Kempf/GuidestarLaser/ProjectRequirements/Project_Reviews/Project_Reeview_1/Pitch1.pptx

## Guide Star Laser Interface (Semiconductor Laser on Wattle)

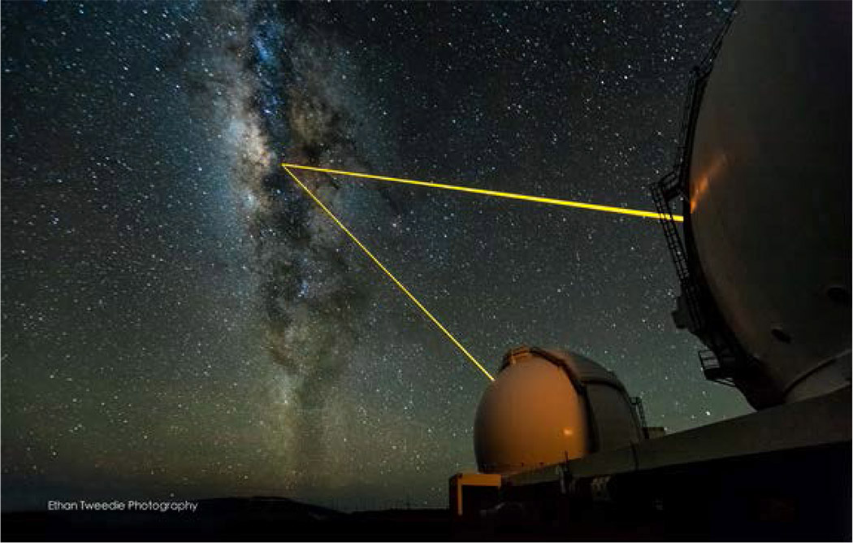
[picture p3: figure]

A. Stuchbery, G. Kennedy, J. Davies, M. Dirnberger, S. Nilon
Client: Céline D’Orgeville
Advanced Instrumentation and Technology Centre (AITC)
Space Environment Research Centre (SERC)

## Slide 2

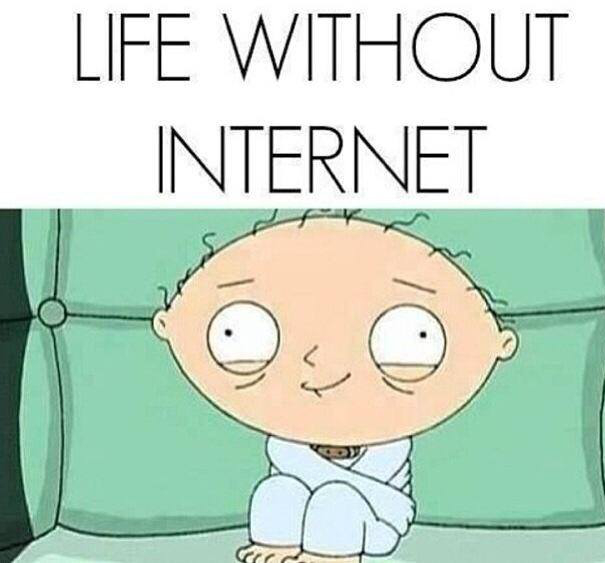
[picture p4: figure]

## Adaptive Optics (AO) – What is it?

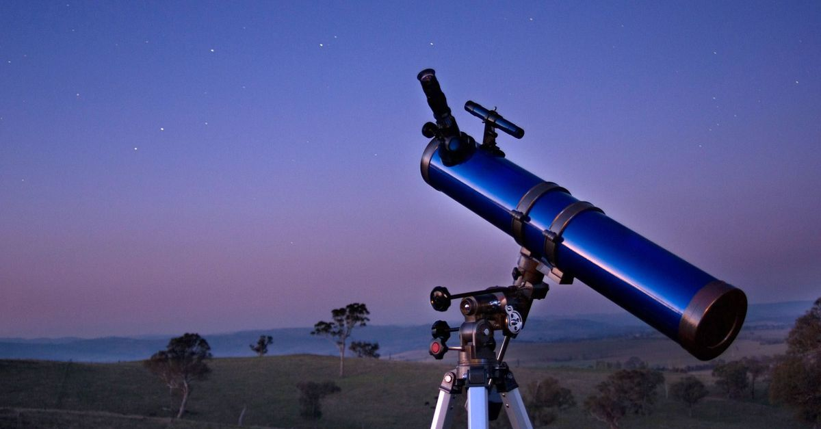
[picture p5: figure]

Animation curtesy of Anna Zovaro, PhD student

## Adaptive Optics (AO) – What is it good for?

Uranus
Credit Keck Observatory

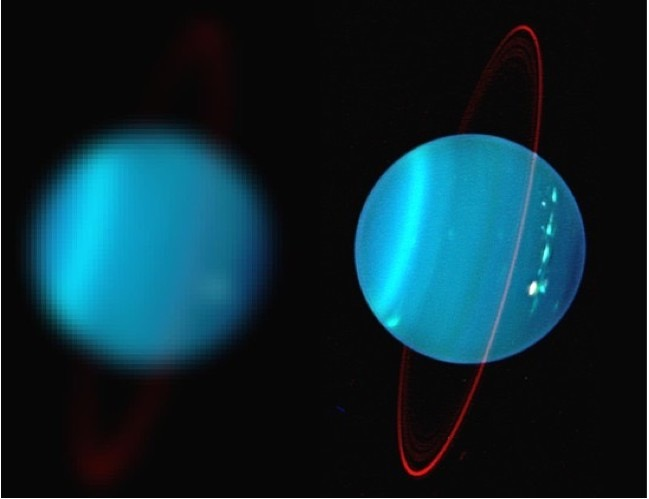
[picture p6: figure]

More than absolutely nothing!

Without AO

With AO

## Toptica Laser

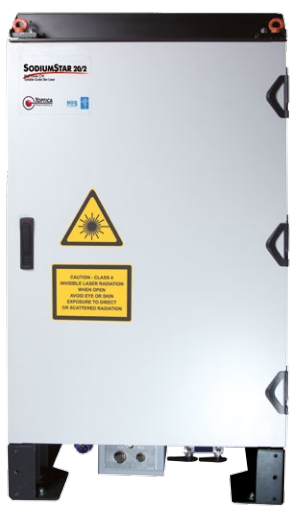
[picture p7: figure]
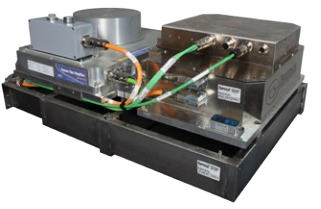
[picture p8: figure]

## Interface Tree

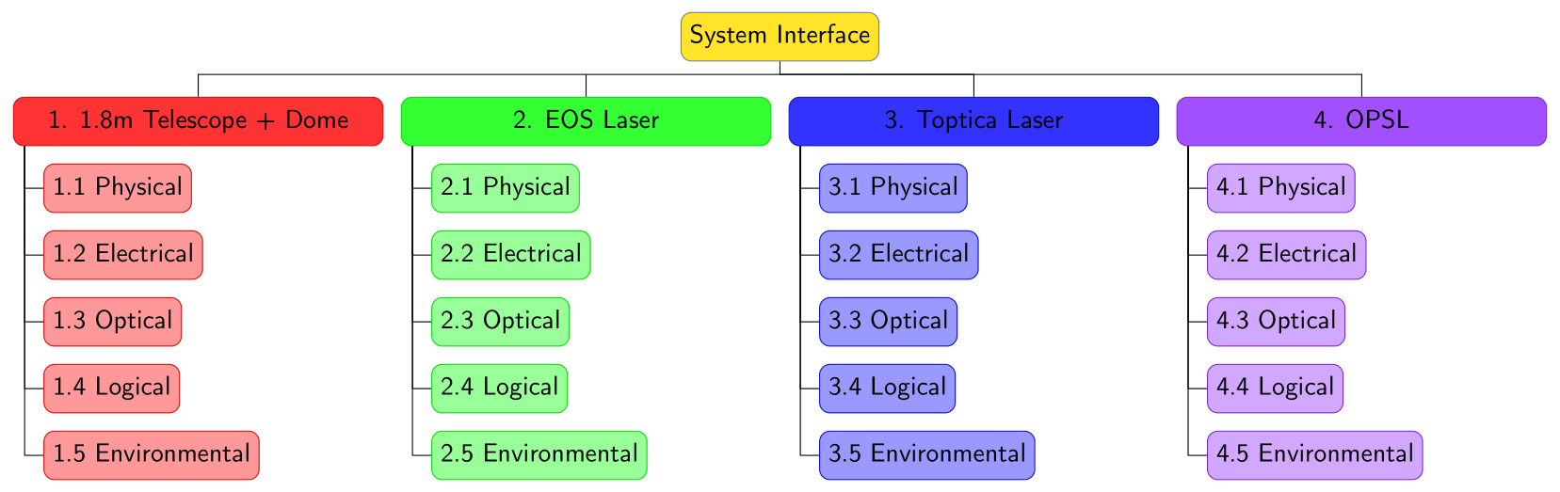
[picture p9: figure]
