Kempf/GuidestarLaser/ProjectRequirements/Resources/Background_Documents/Useful_Links.docx

Vibration Dampening Mounts Supplier with Fishwick Distribution Centre:

http://www.mackayrubber.com.au/products/vibration-isolators/
