Kempf/GuidestarLaser/ProjectRequirements/Solution_Concepts/Brainstorms/A-EOS_Toptica_ANU-VERT.pdf

⊗

Mounting Plate

EOS Breadboards

ANU GSL

Toptica
GSL
