Kempf/GuidestarLaser/ProjectRequirements/Solution_Concepts/Brainstorms/B-EOS_ANU.pdf

Mounting Plate

EOS Breadboard

EOS Breadboard

EOS Breadboard

ANU | GSL
| ⊗

ANU GSL
