Kempf/GuidestarLaser/ProjectRequirements/Solution_Concepts/Brainstorms/C-Toptica_ANU.pdf

Mounting Plate

⊗

Beam
Selector

Toptica
GSL

Breadboard

ANU GSL
