Kempf/GuidestarLaser/ProjectRequirements/Artefacts/Contact_list.xlsx

Name | Role | Contact about | Contact details
ANU ENGN4221
Chris Browne | Big Boss/Mastermind | Course questions | chris.browne@anu.edu.au
Cedric Scheerlinck | Tutor |  | cedric.scheerlinck@anu.edu.au
Our client at AITC
Céline d'Orgeville | Client/Supervisor | Everything, semiconductor laser | celine.dorgeville@anu.edu.au Office: (02) 6125 6374 AITC1 - First floor Mobile: +61 (0)451 681 991 Home: (02) 61667089 Skype: celine_dorgeville
Brady Espeland | Technical lead systems engineer mentor? |  | brady.espeland@anu.edu.au (02) 6125 6376 AITC Level 2
Bart Fordham | Opto-Mechanical Engineer |  | u5389681@anu.edu.au (02) 6197 0151 L1.06
Elliott Thorn | PhD in laser guide star facility |  | elliott.thorn@anu.edu.au (02) 6125 6372 L1.06
EOS (Electro Optic Systems)
James Webb | Chief Engineer/Scientist | EOS Laser ('inside the box') | jwebb@eosspacesystems.com +61 2 6222 7961
Mark Blundell | Project Manager | EOS Laser / Telescope | mblundell@eos-aus.com +61 (0)428 114 844 +61 2 6222 7941
Chris Moore | Telescope Site Manager | Telescope Access | cmoore@eos-aus.com
Allan Smith | IT
Andrew Gray | EOS Senior Technician
Jack Gray | Electronics stuff | CAN | Mechanical, left, left
