Kempf/GuidestarLaser/Current_Status/README.md

## Current_Status
Scheduling, organisation, etc.

### Directories

### Files

*	`Project_Schedule.xlsx`:	Outline of the semester dates, as well as key course deadlines. This will be updated to include milestones and additional deadlines
*	`Project_Hours.xlsx`: [google doc](https://docs.google.com/spreadsheets/d/1dUo6-rTq1Kz_F9VqjadB9rXlVd1LVuZzNobbM8MXEa4/edit?usp=sharing) covering hours done by team members - Note: Follow the following link
*	`Weekly_And_Audit_Summaries.pdf`:	Summary Document. Details the key events and outcomes for each week. Document also details the weekly events that are scheduled. Overleaf: https://www.overleaf.com/10734401hpdwygsbymfb
