Kempf/GuidestarLaser/Client_Communications/README.md

## Client Communications:

### Directories:
*	**Emails**: Contains all important email correspondences with clients
*	**Meeting_Notes**: contains information recieved in meetings with various personell
*	**Project_Background_Information**: Background files, papers and references.

### Files: 
Contains additional files relating to client correspondence (This will potentially contain duplicates of minutes for client meetings)

*   [Questions for AITC staff](https://docs.google.com/document/d/1zAk25DJ26Gl5TWY5K3axyuuhdbPYalDZMd1OXUz_-uc/edit?usp=sharing) (google doc)

*	[Questions for ANU Laser team](https://docs.google.com/document/d/101ov5f6TUorRwxF0RoaHoPD7qzghxyLS7KKh2AlDFOE/edit?usp=sharing) (google doc)
		
*	**Project_Contracts.pdf**:	Contains list of contacts for the project work
