Kempf/GuidestarLaser/ProjectRequirements/Project_Reviews/Project_Review_2/Pitch2.pptx

## Guide Star Laser Interface (Semiconductor Laser on Wattle)


A. Stuchbery, G. Kennedy, J. Davies, M. Dirnberger, S. Nilon
Client: Céline D’Orgeville
Advanced Instrumentation and Technology Centre (AITC)
Space Environment Research Centre (SERC)

## LIFE WITHOUT INTERNET

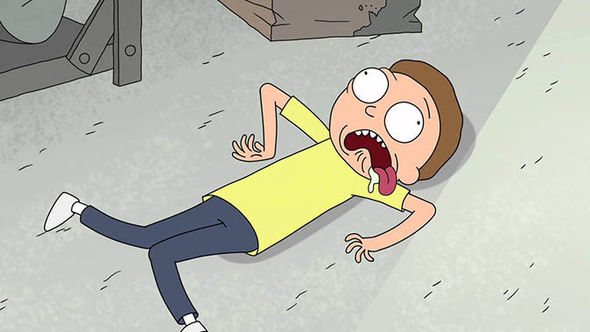
[picture p76: figure]

## Progress

- Verification of initial SSS
- Delivered 120+ preliminary requirements
- Solution agnostic conceptual designs
- Our Client is happy! So are all our stakeholders!

Stakeholders

Our Client Celine

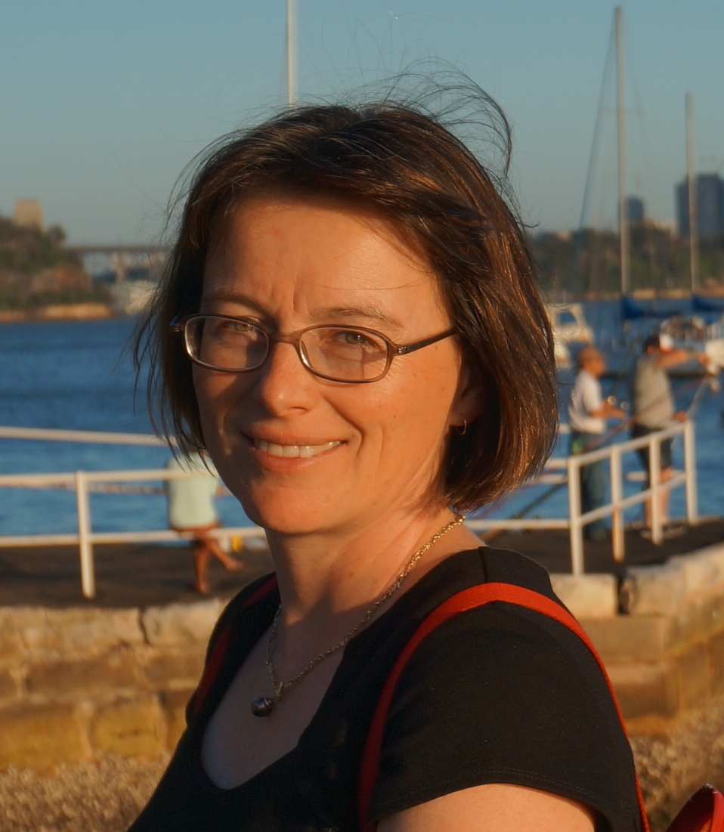
[picture p77: figure]
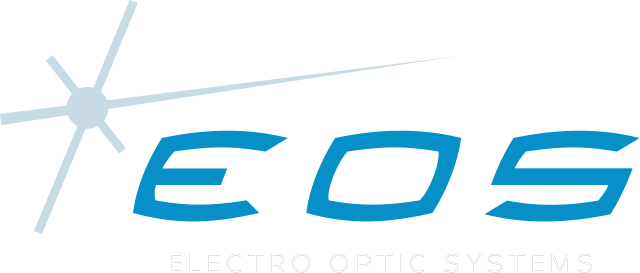
[picture p78: figure]

Notes: Also keeping our stakeholder in the loop, managing relations with all stakeholders
Logos

## Requirements

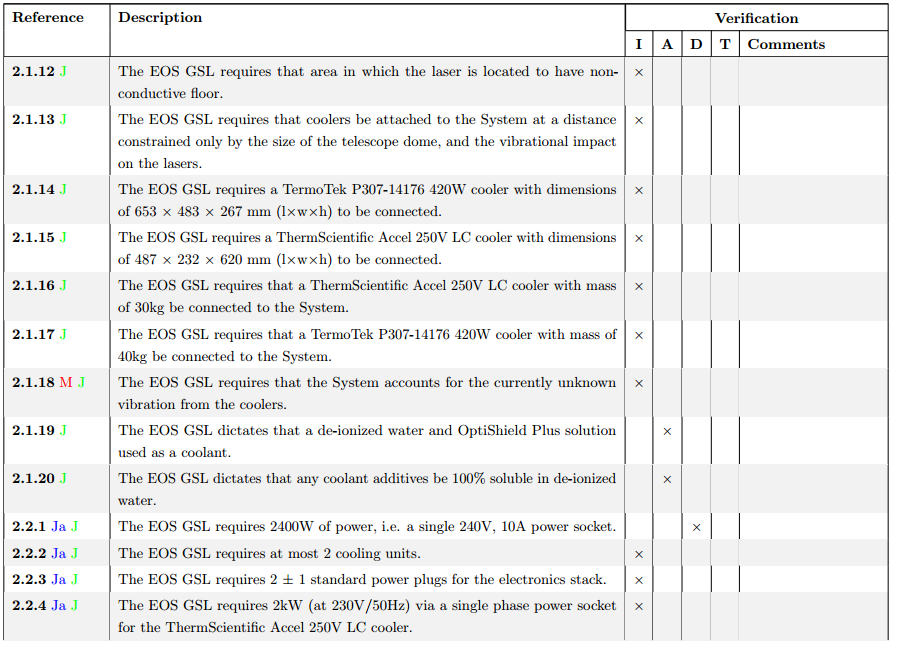
[picture p79: figure]

Notes: Also keeping our stakeholder in the loop, managing relations with all stakeholders
Logos

## Solution Agnostic Concepts

## System Requirements Management

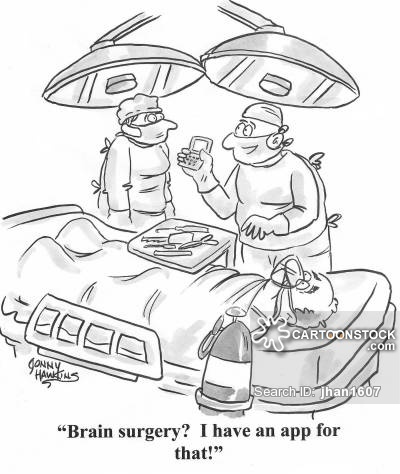
[picture p80: figure]

Our LaTeX macros are available on Tech Launcher. Thank you to Markus!
bit.do (http://bit.do/4221macros)/4221macros (http://bit.do/4221macros)

a macro

## Interface Management

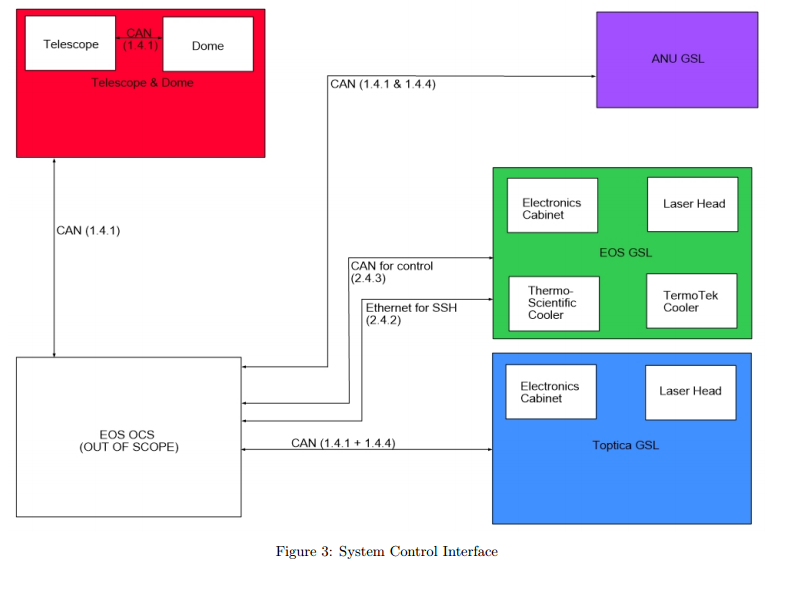
[picture p81: figure]

Notes: Also keeping our stakeholder in the loop, managing relations with all stakeholders
Logos

## From Here

- On schedule
- Facetime organise with out client
- Continue developing conceptual designs
- Finalise requirements
- Make sure our client stays Happy!

## Questions

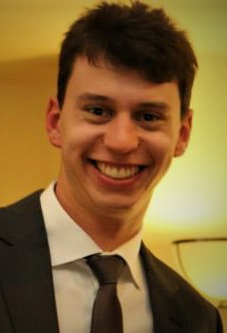
[picture p82: figure]

Alex
Sys-Eng, CAD

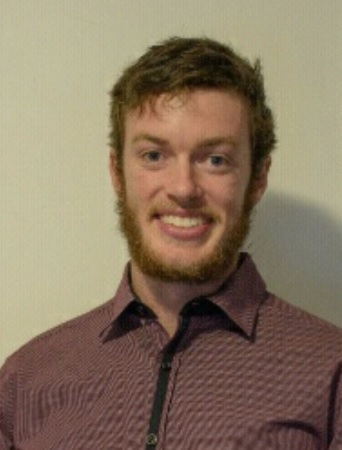
[picture p83: figure]

Gerard
Sys-Eng

Jordan
Sys-Eng

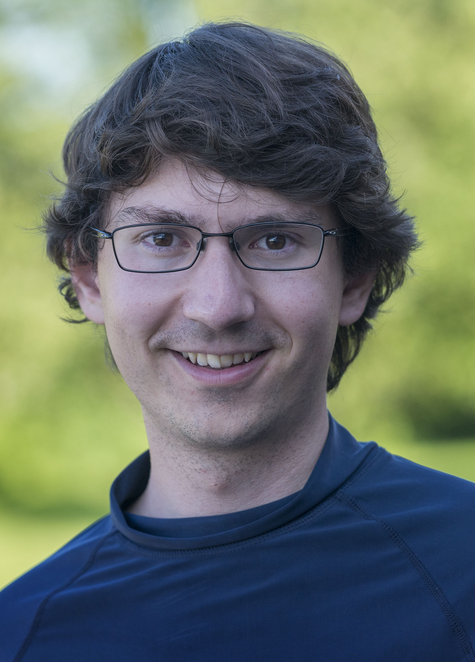
[picture p84: figure]

Markus
LaTeX Wizard

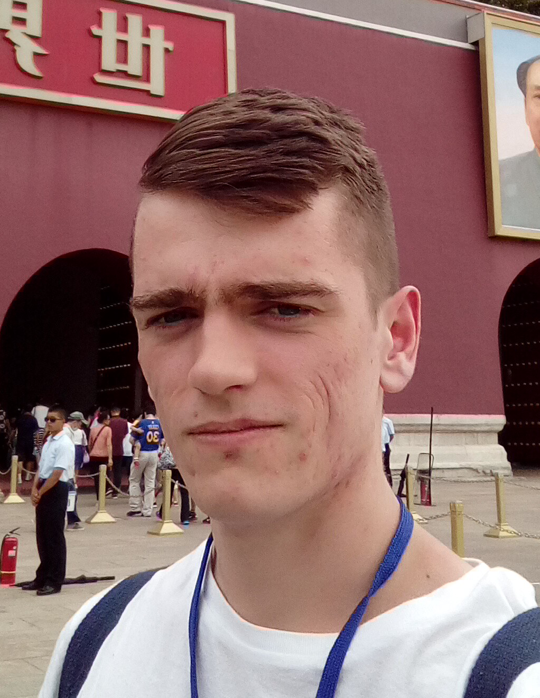
[picture p85: figure]

Samson
Control-Sys
