Kempf/GuidestarLaser/Working_Files/Concept_Design_Report_Documentation/EOS_DesignReport_Process.pdf

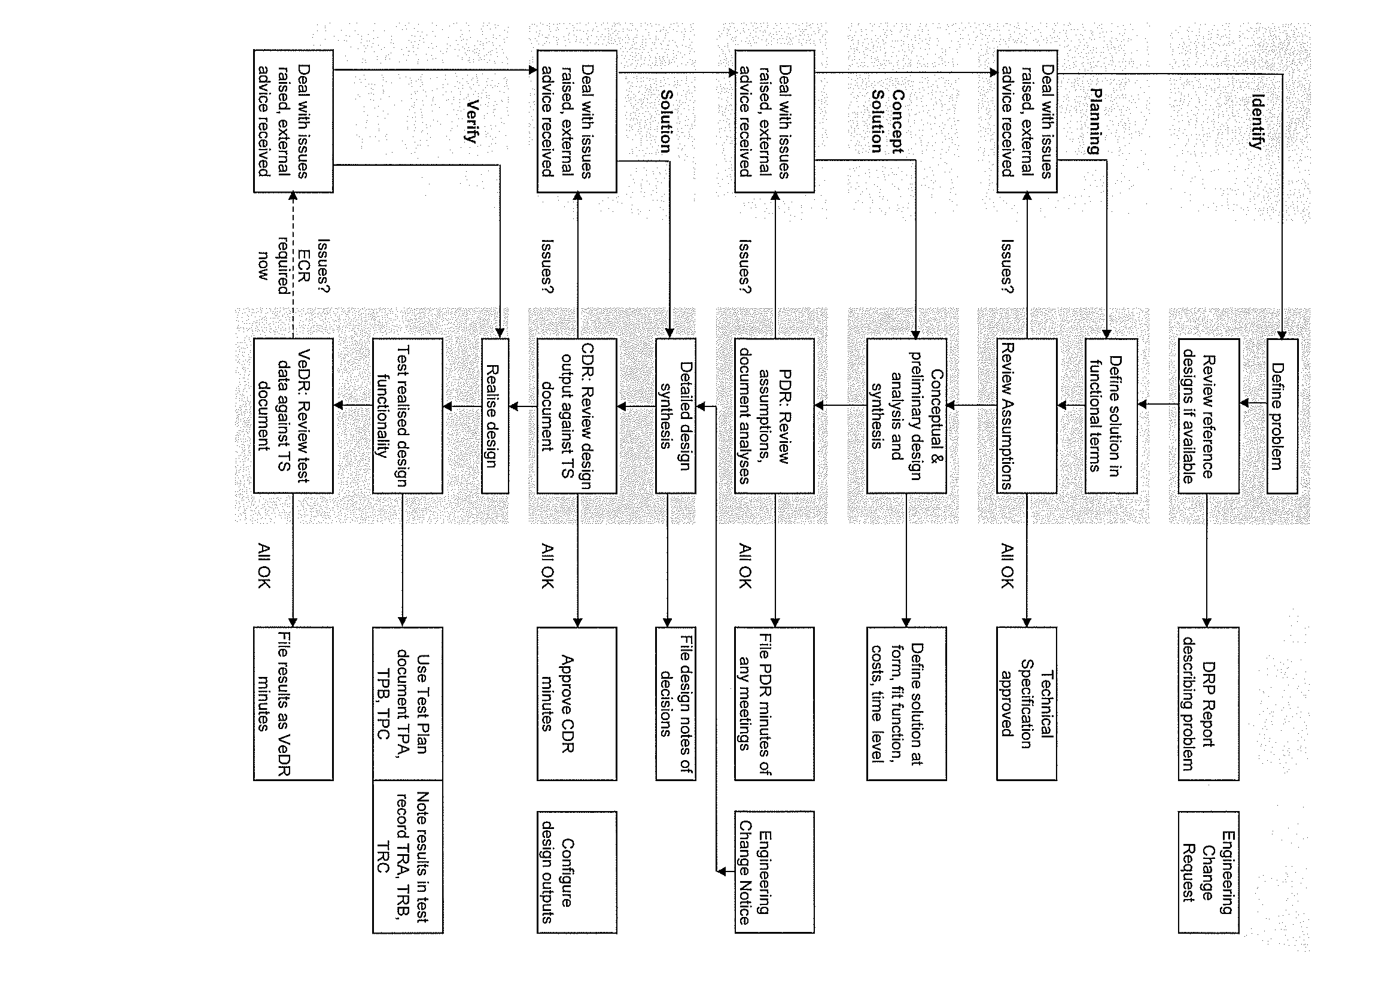
[picture p86: page 1]
