Kempf/GuidestarLaser/Client_Communications/Emails/Telescope_6_Oct_Jak.pdf

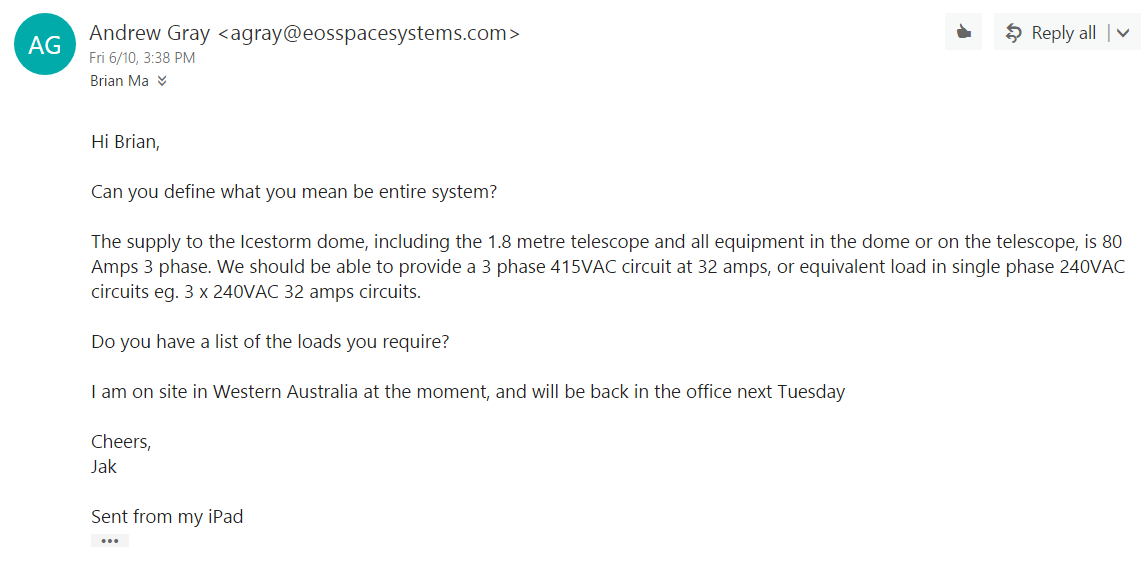
[picture p89: figure]
