Kempf/GuidestarLaser/ProjectRequirements/Artefacts/Project_Schedule.xlsx

Involve Celine | Involve Tutor | Involves Team | Involves Everyone | Course Schedule: | http://bit.do/TechLauncher
University Week | Monday | Tuesday | Wednesday | Thursday | Friday | Saturday | Sunday
1 | 2017-02-20 | 2017-02-21 | 2017-02-22 | 2017-02-23 | 2017-02-24 | 2017-02-25 | 2017-02-26
 |  |  |  |  |  | Team Foundation Day
2 | 2017-02-27 | 2017-02-28 | 2017-03-01 | 2017-03-02 | 2017-03-03 | 2017-03-04 | 2017-03-05
 |  |  |  | Client Meeting 1, 09:30, AITC
 |  |  |  | Tutor Meeting 1, 15:00-16:00, e240
3 | 2017-03-06 | 2017-03-07 | 2017-03-08 | 2017-03-09 | 2017-03-10 | 2017-03-11 | 2017-03-12
 | Getting Started Workshop |  | Extra Team Meeting |  | Work @ Stromlo 09:00 - 17:00
 | Course Feedback Session 1
4 | 2017-03-13 | 2017-03-14 | 2017-03-15 | 2017-03-16 | 2017-03-17 | 2017-03-18 | 2017-03-19
 | Pitching Workshop |  |  | Tutor Meeting 2, 13:30-14:30, e240 | Work @ Stromlo 09:00 - 17:00
5 | 2017-03-20 | 2017-03-21 | 2017-03-22 | 2017-03-23 | 2017-03-24 | 2017-03-25 | 2017-03-26
Project Review 1 (25%) |  |  |  | Pitch 1, 1600-1700, Physics Link | Work @ Stromlo 09:00 - 17:00
Date TBA
6 | 2017-03-27 | 2017-03-28 | 2017-03-29 | 2017-03-30 | 2017-03-31 | 2017-04-01 | 2017-04-02
 | Course Imporvement Focus Groups |  |  | Tutor Meeting 3, 13:30-14:30, e240 | Work @ Stromlo 09:00 - 17:00
Teaching Break | 2017-04-03 | 2017-04-04 | 2017-04-05 | 2017-04-06 | 2017-04-07 | 2017-04-08 | 2017-04-09
 | Course Feedback Session 2
Teaching Break | 2017-04-10 | 2017-04-11 | 2017-04-12 | 2017-04-13 | 2017-04-14 | 2017-04-15 | 2017-04-16
 |  |  |  |  | Work @ Stromlo 09:00 - 17:00
7 | 2017-04-17 | 2017-04-18 | 2017-04-19 | 2017-04-20 | 2017-04-21 | 2017-04-22 | 2017-04-23
 |  |  |  | Tutor Meeting 4, 13:30-14:30, e240 | Work @ Stromlo 09:00 - 17:00
8 | 2017-04-24 | 2017-04-25 | 2017-04-26 | 2017-04-27 | 2017-04-28 | 2017-04-29 | 2017-04-30
Project Review 2 (25%) |  |  |  |  | Work @ Stromlo 09:00 - 17:00
Date TBA
9 | 2017-05-01 | 2017-05-02 | 2017-05-03 | 2017-05-04 | 2017-05-05 | 2017-05-06 | 2017-05-07
Poster (5%) | Networking Workshop |  |  | Tutor Meeting 5, 13:30-14:30, e240 | Work @ Stromlo 09:00 - 17:00
10 | 2017-05-08 | 2017-05-09 | 2017-05-10 | 2017-05-11 | 2017-05-12 | 2017-05-13 | 2017-05-14
Project Showcase (5%) |  |  |  |  | Work @ Stromlo 09:00 - 17:00
Date TBA
11 | 2017-05-15 | 2017-05-16 | 2017-05-17 | 2017-05-18 | 2017-05-19 | 2017-05-20 | 2017-05-21
Project Review 3 (25%) | Course Improvement Focus Groups |  |  | Tutor Meeting 6, 13:30-14:30, e240
Date TBA
12 | 2017-05-22 | 2017-05-23 | 2017-05-24 | 2017-05-25 | 2017-05-26 | 2017-05-27 | 2017-05-28
