Kempf/GuidestarLaser/ProjectRequirements/Previous_Team_Work_Contents.pdf

Google Drive Contents Page

(For the benefit of markers)

Home Page Files:
- Contents Page
- Project Hours: This sheet is where we log what tasks we have each worked on or completed with the corresponding hours spent. Note that our weeks run from Friday to Thursday to be structured around the client meetings on Fridays.

Folder contents:
- Artefacts: contains documents, schematics, files relevant to project.
- Constraint calcs: Copies of constraint calculations.
- Diagrams: contains 3D renders of laser and telescope systems and subsystems
- Meetings: contains meeting agendas that are emailed to the relevant attendees prior to each meeting, and updated with notes post meeting.
- Project Reviews: contains Pitch outlines and Project reports
- Resources: contains relevant background information, articles, etc
- Background Documents: contains academic papers
■ Toptica Laser: Documents relating to the toptica laser
- Toptica @ ESO: Papers about ESO implementation of Toptica laser
■ International case studies: General information on similar implementation strategies
- Course Information: contains pdfs of all course information
- Textbooks: contains relevant textbooks
- Press Images: Nice pictures for posters and visualisation
- Solution Concepts: contains solution illustration files
- SolidWorks: contains Solidworks solution files
- Brainstorms: contains brainstorming solution scribbles
- Other: contains other stuffs
