Kempf/GuidestarLaser/Previous_Team_Work/Project_Reviews/OLD/Pitch_2.pptx

## Guide Star Laser Interface (Semiconductor Laser on Wattle)

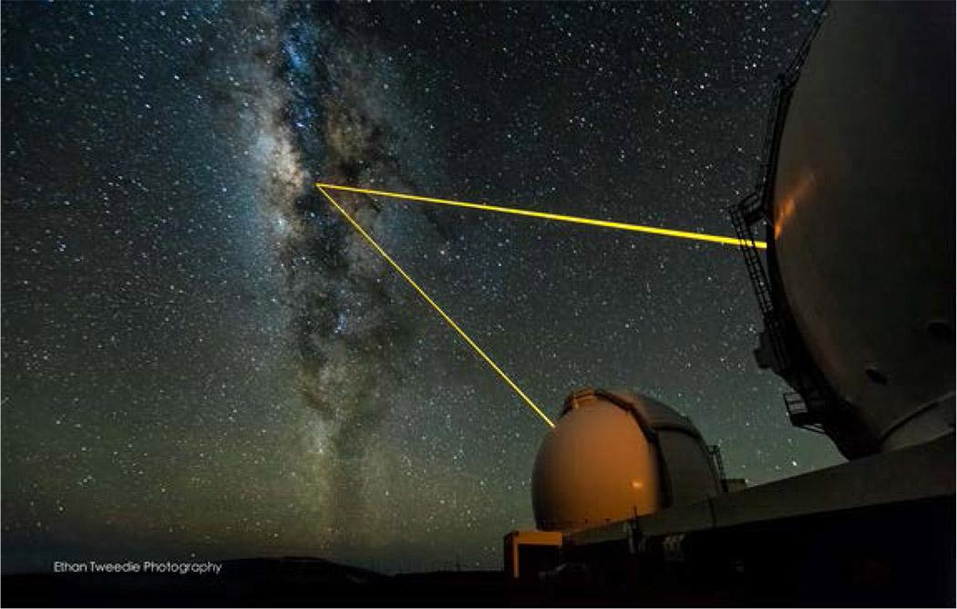
[picture p90: figure]

A. Stuchbery, G. Kennedy, J. Davies, M. Dirnberger, S. Nilon
Client: Céline D’Orgeville
Advanced Instrumentation and Technology Centre (AITC)
Space Environment Research Centre (SERC)

## LIFE WITHOUT INTERNET


## Progress

- Verification of Initial SSS
- Delivered 120+ Preliminary Requirements
- Solution Agnostic Preliminary Concepts
- Our Client is happy! So are all our stakeholders!


Our Client Celine

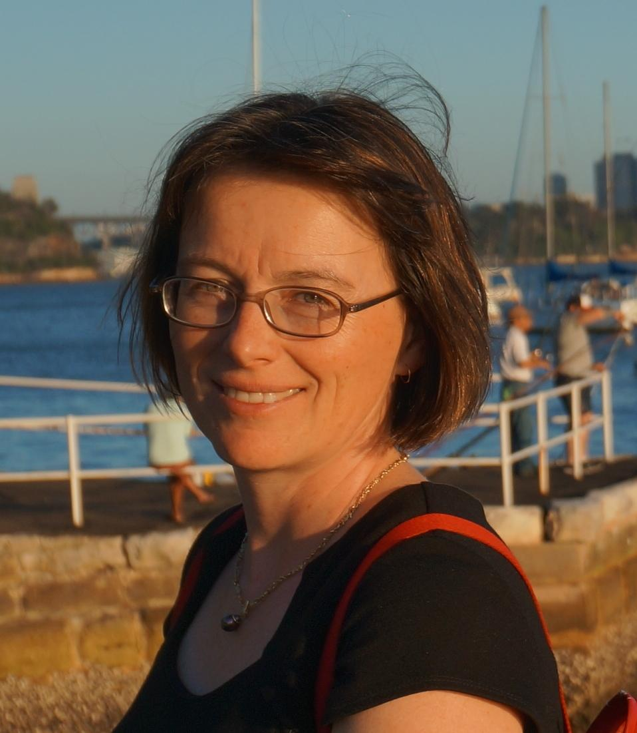
[picture p91: figure]
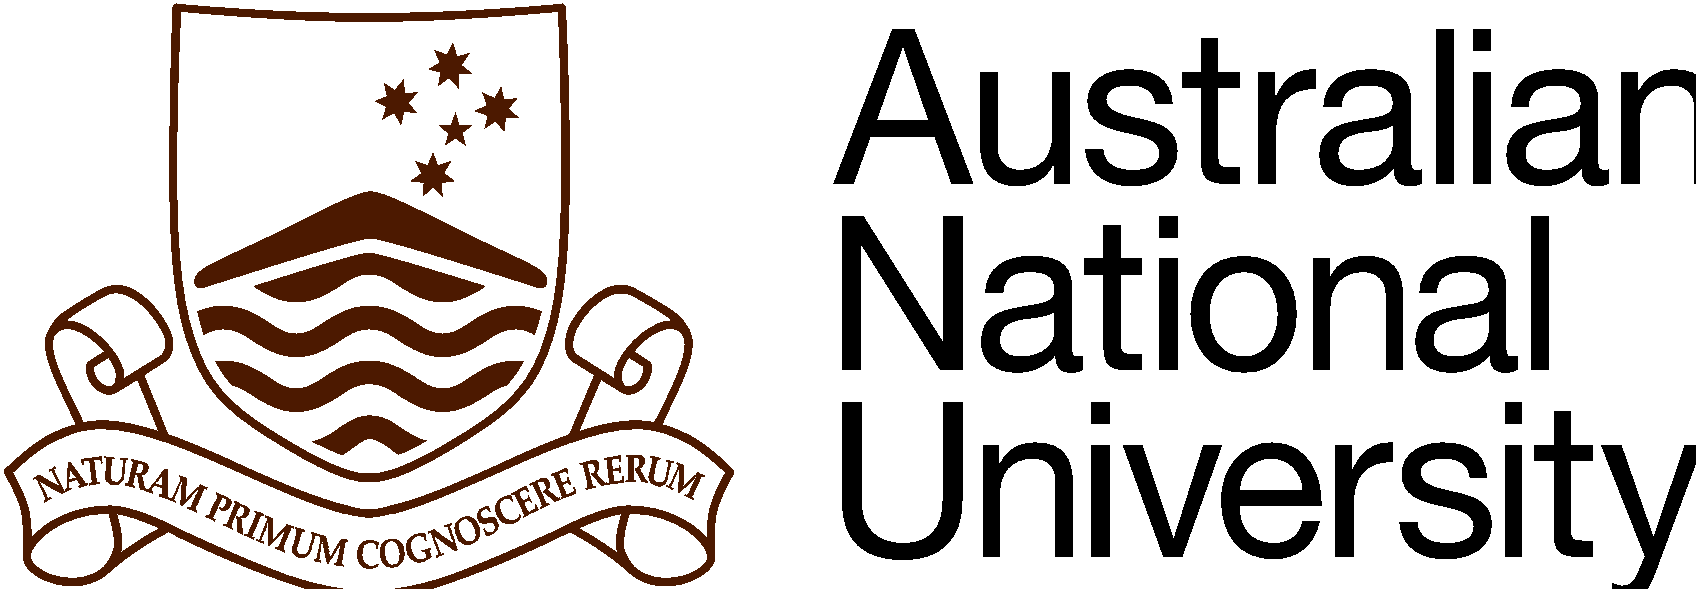
[picture p92: figure]
anu-logo-colour.pdf

Notes: Also keeping our stakeholder in the loop, managing relations with all stakeholders
Logos

## Solution Agnostic Concepts

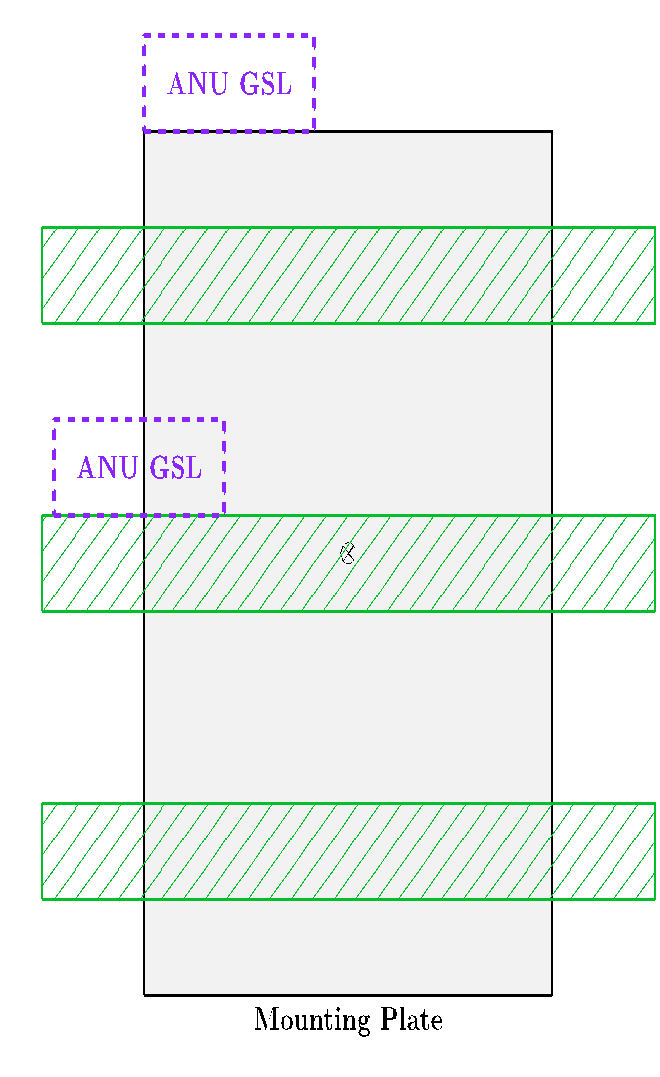
[picture p93: figure]
2 EOS_OPSL.pdf
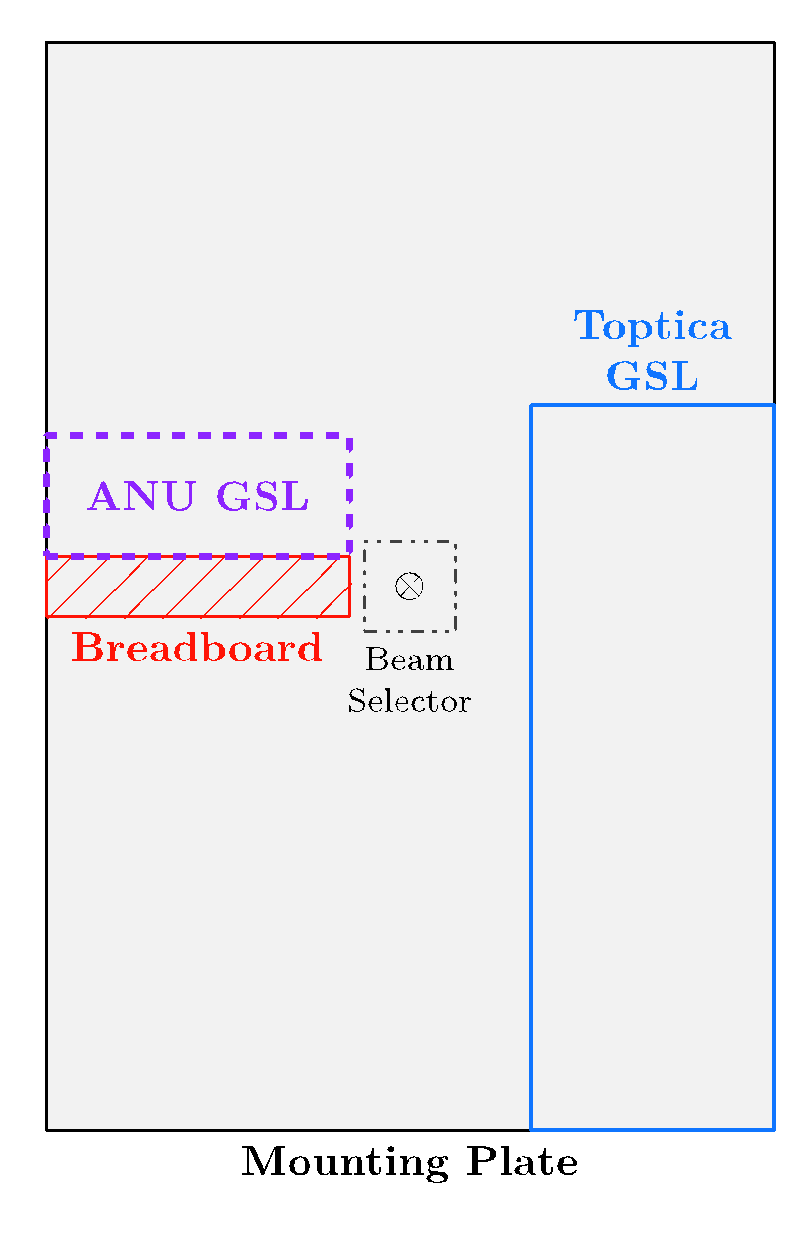
[picture p94: figure]
2 Toptica_OPSL.pdf
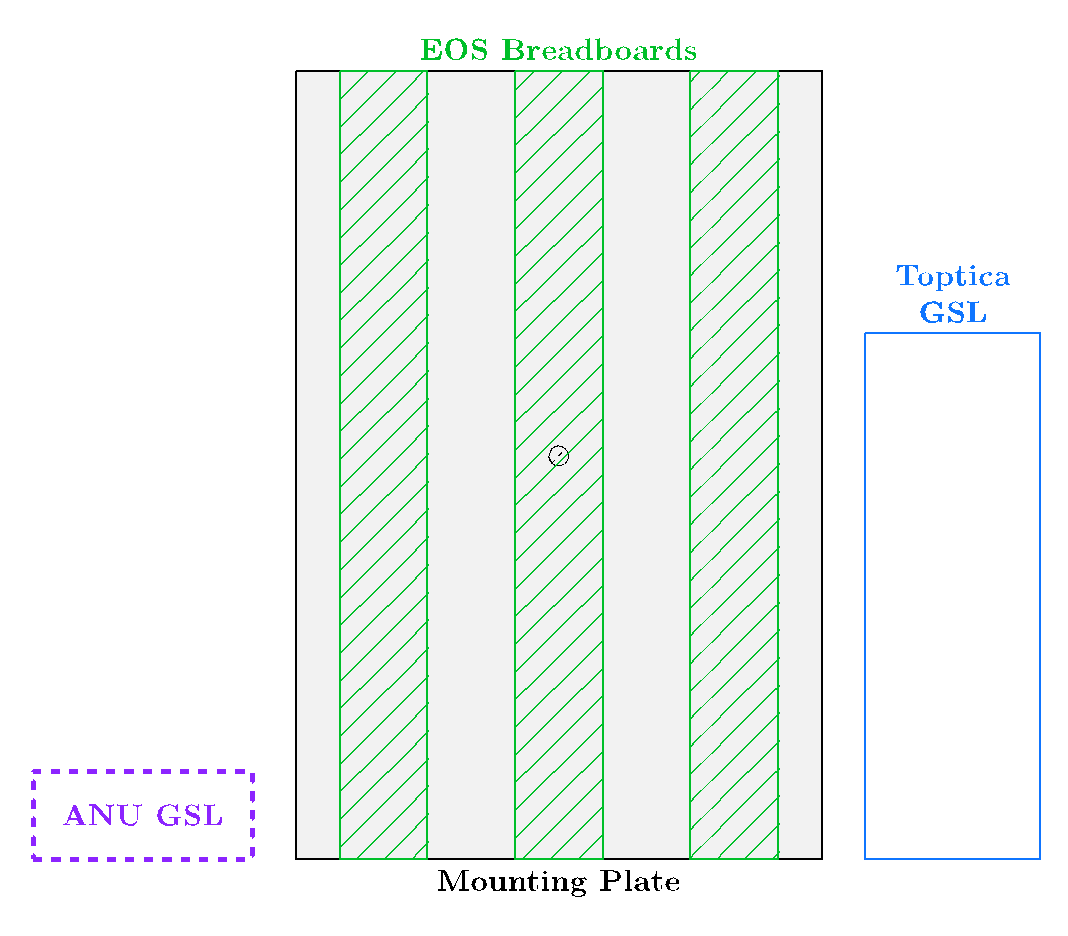
[picture p95: figure]
3 EOS_Toptica_ANU_VERT.pdf

## System Requirements Management


Our LaTeX macros are available on Tech Launcher. Thank you to Markus!
bit.do/4221macros

a macro

## From Here

- On schedule
- Facetime organise with out client
- Continue developing conceptual designs
- Finalise requirements
- Make sure our client stays Happy!

## Questions

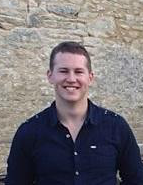
[picture p96: figure]

Jordan
Sys-Eng

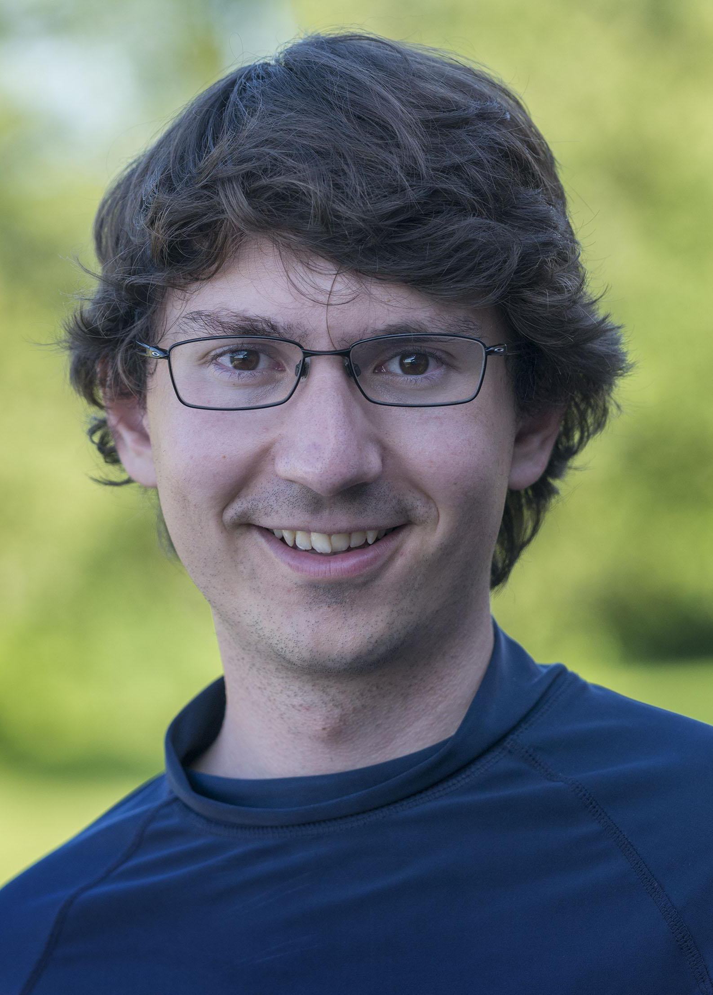
[picture p97: figure]

Markus
LaTeX Wizard

Alex
Sys-Eng

Gerard
Sys-Eng

Samson
Pick a RO
