Kempf/GuidestarLaser/Client_Communications/Meeting_Notes/J_Webb_8_9/breadboard_diagram.jpg

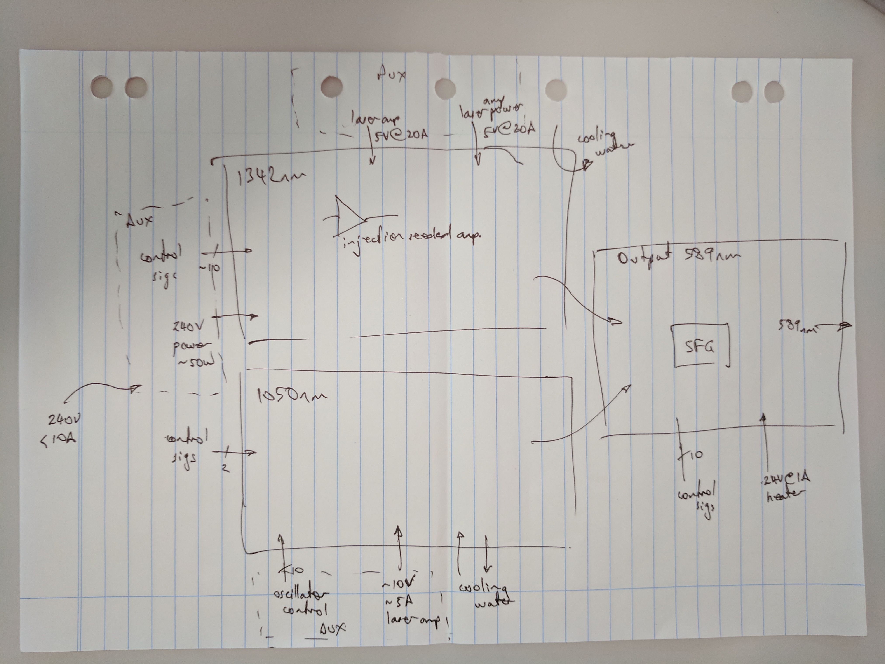
Client_Communications/Meeting_Notes/J_Webb_8_9/breadboard_diagram.jpg
