Kempf/GuidestarLaser/Client_Communications/Meeting_Notes/J_Webb_8_9/vibration_sensitivity.jpg

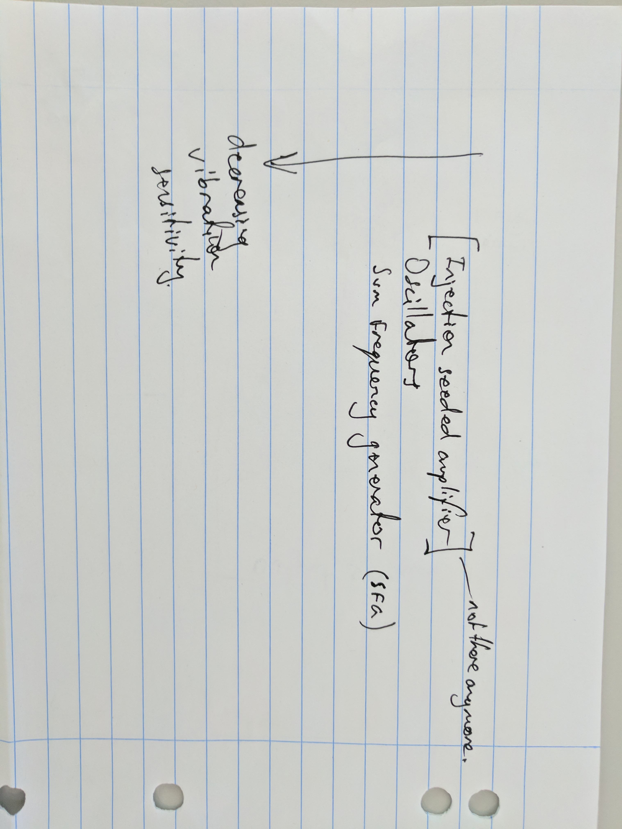
Client_Communications/Meeting_Notes/J_Webb_8_9/vibration_sensitivity.jpg
