Kempf/GuidestarLaser/ProjectRequirements/Artefacts/ConstraintCalcs/20170421_160722.jpg

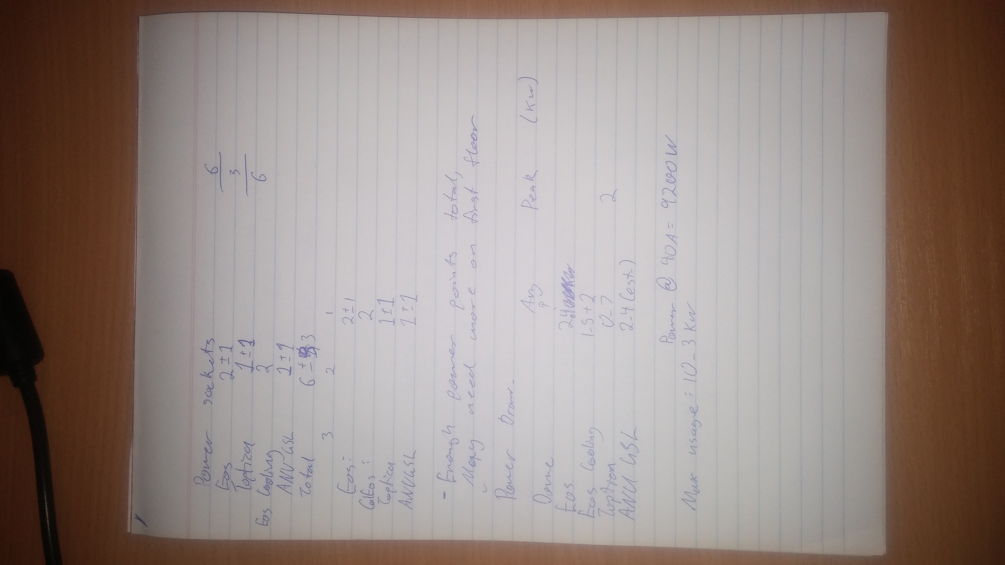
ProjectRequirements/Artefacts/ConstraintCalcs/20170421_160722.jpg
