Kempf/GuidestarLaser/ProjectRequirements/Other/Schematics/PowerInterface.jpg

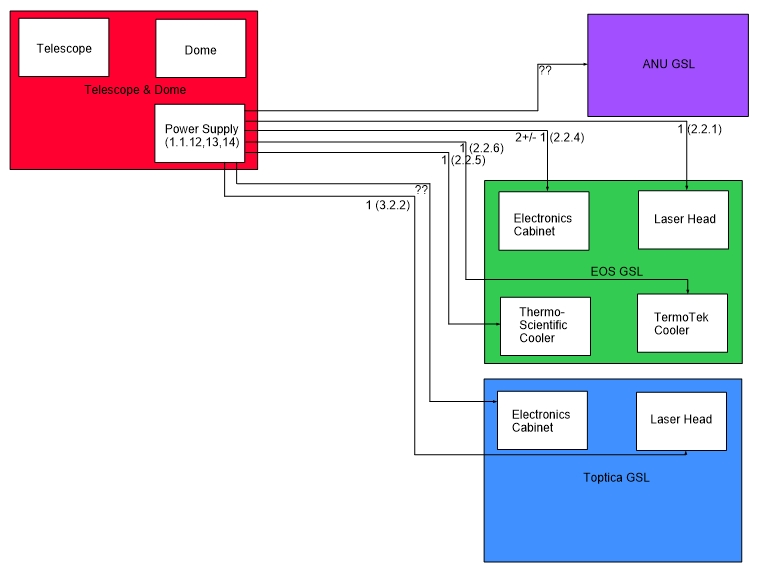
ProjectRequirements/Other/Schematics/PowerInterface.jpg
