Kempf/GuidestarLaser/ProjectRequirements/Project_Reviews/Poster/Context-idea.png

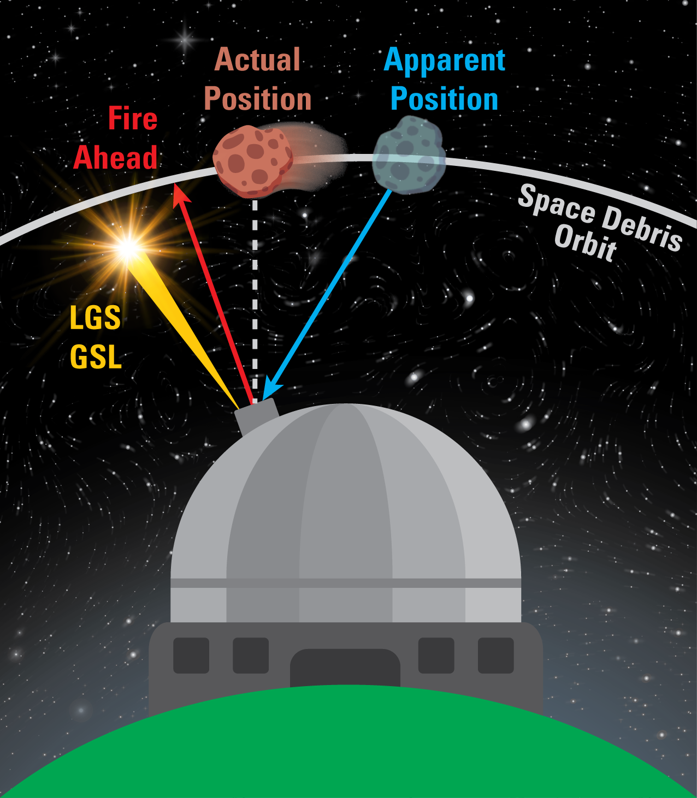
ProjectRequirements/Project_Reviews/Poster/Context-idea.png
