Kempf/GuidestarLaser/ProjectRequirements/Resources/Photographs_ESO-Paranal/eso1613d.jpg

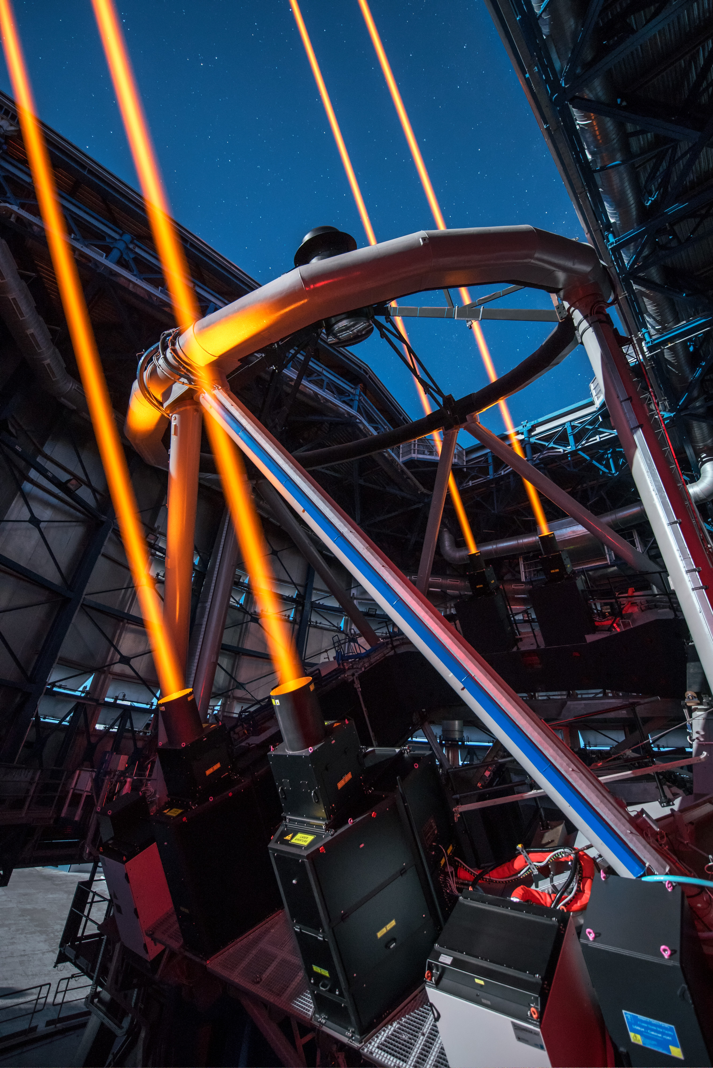
ProjectRequirements/Resources/Photographs_ESO-Paranal/eso1613d.jpg
