Kempf/GuidestarLaser/ProjectRequirements/Resources/Photographs_ESO-Paranal/eso1613g.jpg

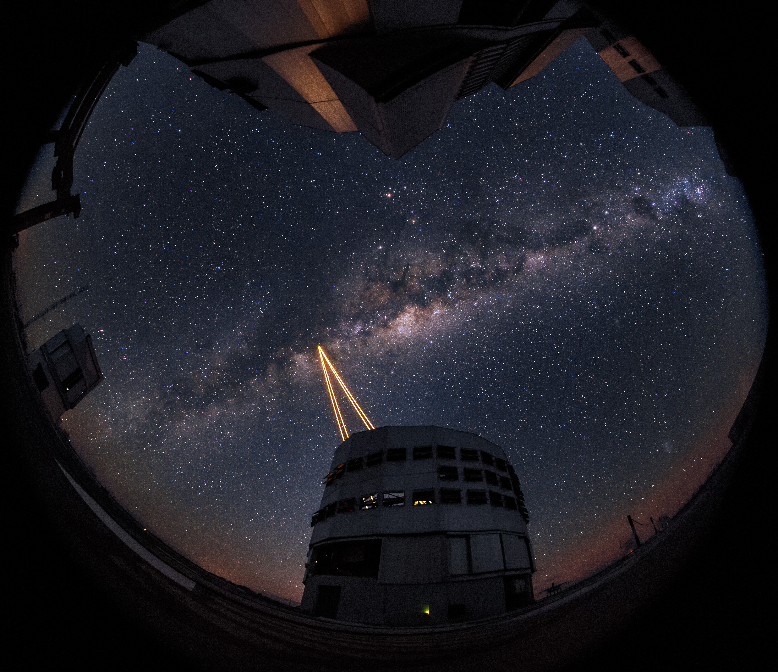
ProjectRequirements/Resources/Photographs_ESO-Paranal/eso1613g.jpg
