Kempf/GuidestarLaser/ProjectRequirements/Solution_Concepts/Brainstorms/A-EOS_Toptica_ANU-VERT.jpg

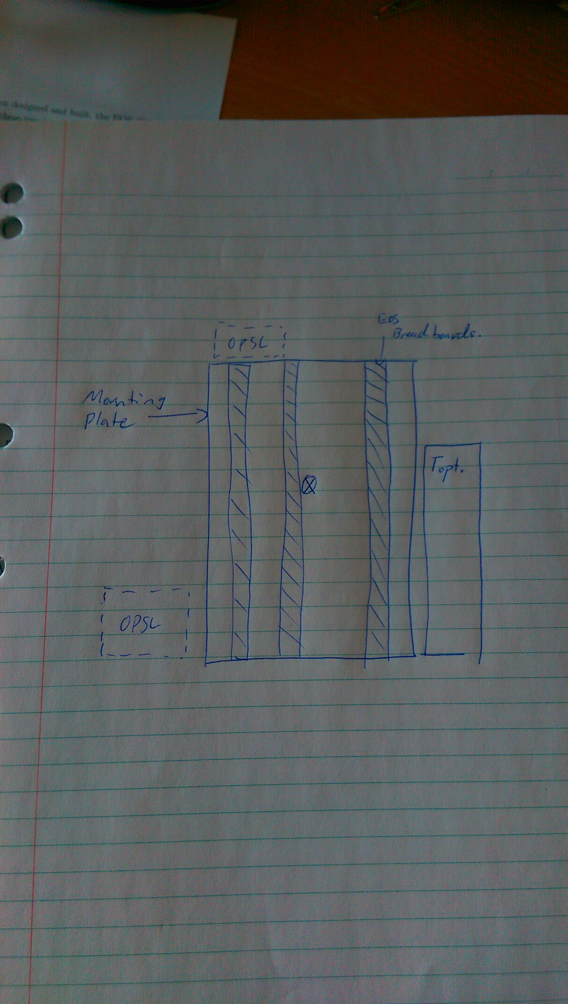
ProjectRequirements/Solution_Concepts/Brainstorms/A-EOS_Toptica_ANU-VERT.jpg
