Kempf/GuidestarLaser/ProjectRequirements/Solution_Concepts/Brainstorms/B-EOS_ANU.jpg

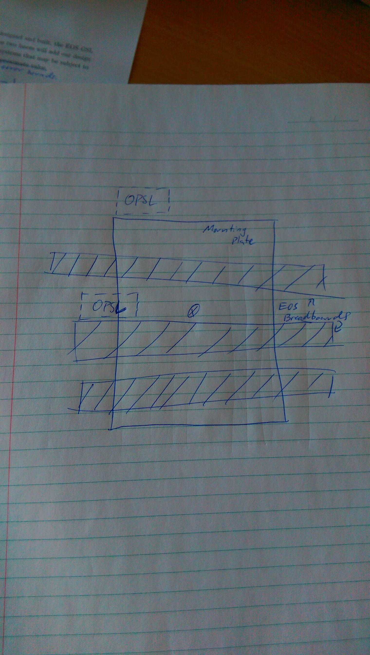
ProjectRequirements/Solution_Concepts/Brainstorms/B-EOS_ANU.jpg
