Kempf/GuidestarLaser/ProjectRequirements/Solution_Concepts/Brainstorms/C-Toptica_ANU.jpg

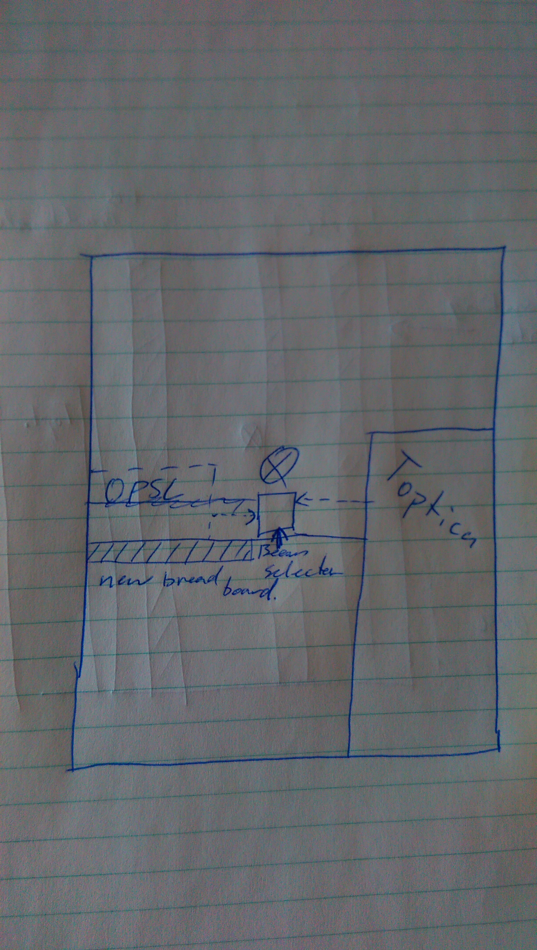
ProjectRequirements/Solution_Concepts/Brainstorms/C-Toptica_ANU.jpg
