Kempf/GuidestarLaser/Working_Files/Dome_Photos/1A.jpg

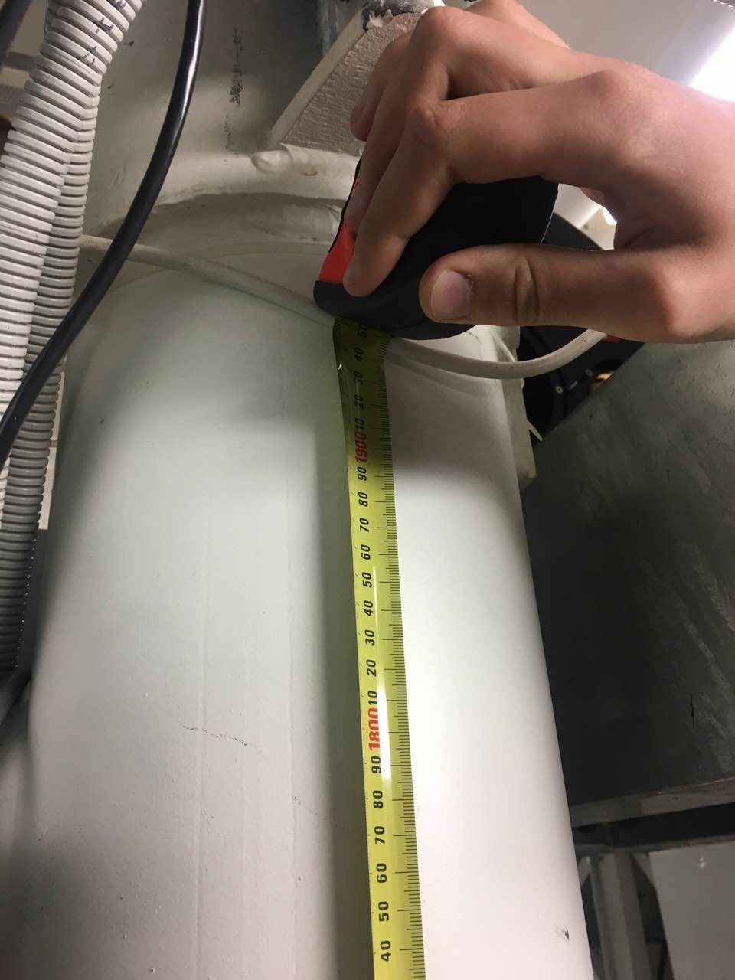
Working_Files/Dome_Photos/1A.jpg
