Kempf/GuidestarLaser/Working_Files/Dome_Photos/1B.jpg

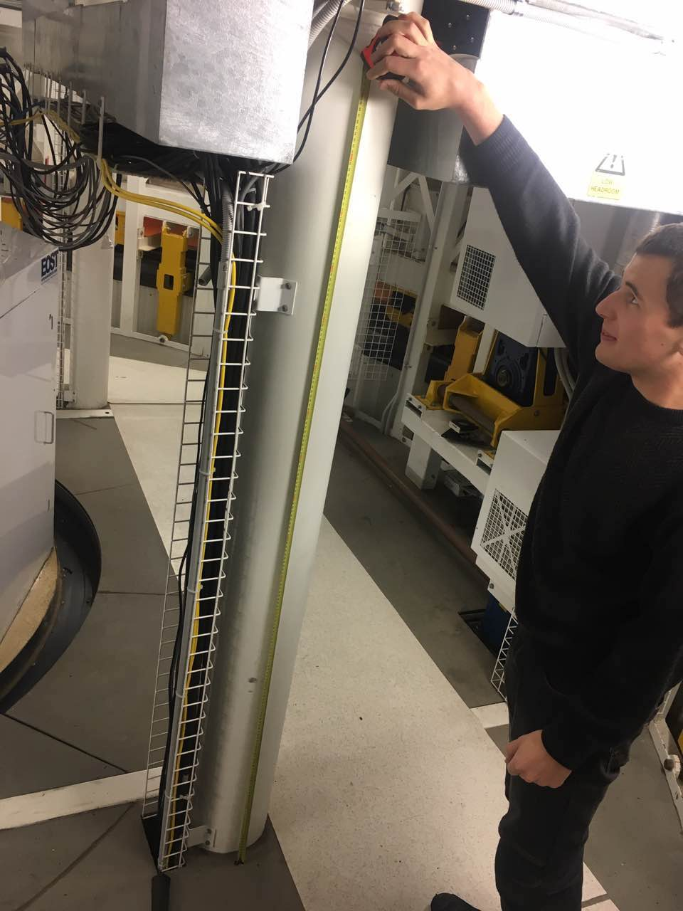
Working_Files/Dome_Photos/1B.jpg
