Kempf/GuidestarLaser/Working_Files/Dome_Photos/2A.jpg

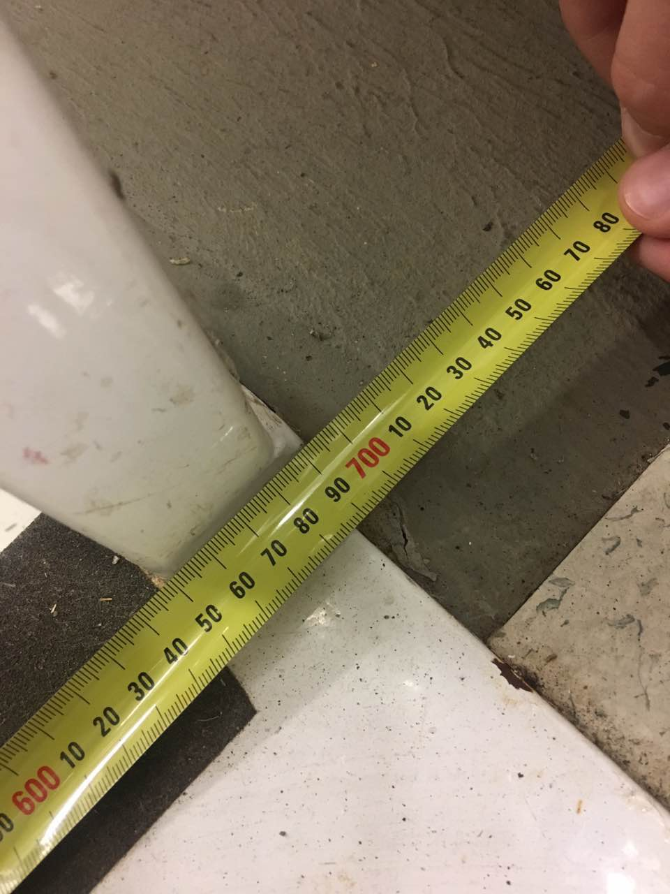
Working_Files/Dome_Photos/2A.jpg
