Kempf/GuidestarLaser/Working_Files/Dome_Photos/2B.jpg

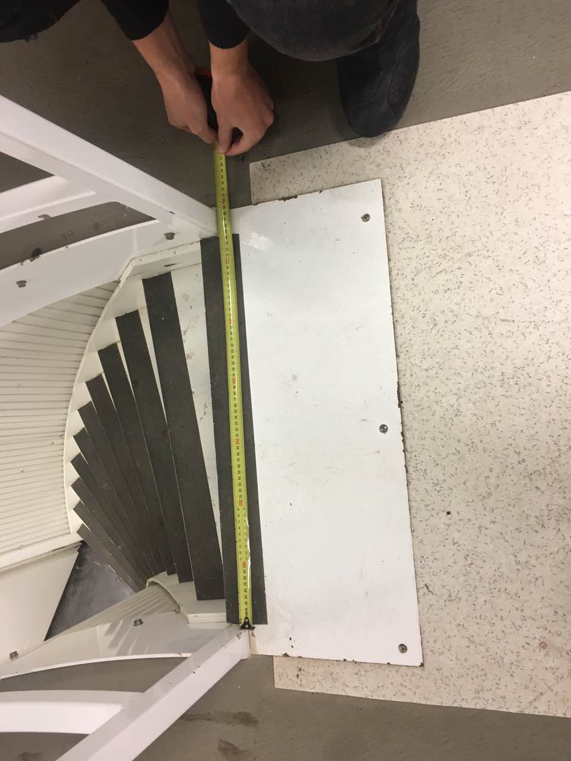
Working_Files/Dome_Photos/2B.jpg
