Kempf/GuidestarLaser/Working_Files/Dome_Photos/3A.jpg

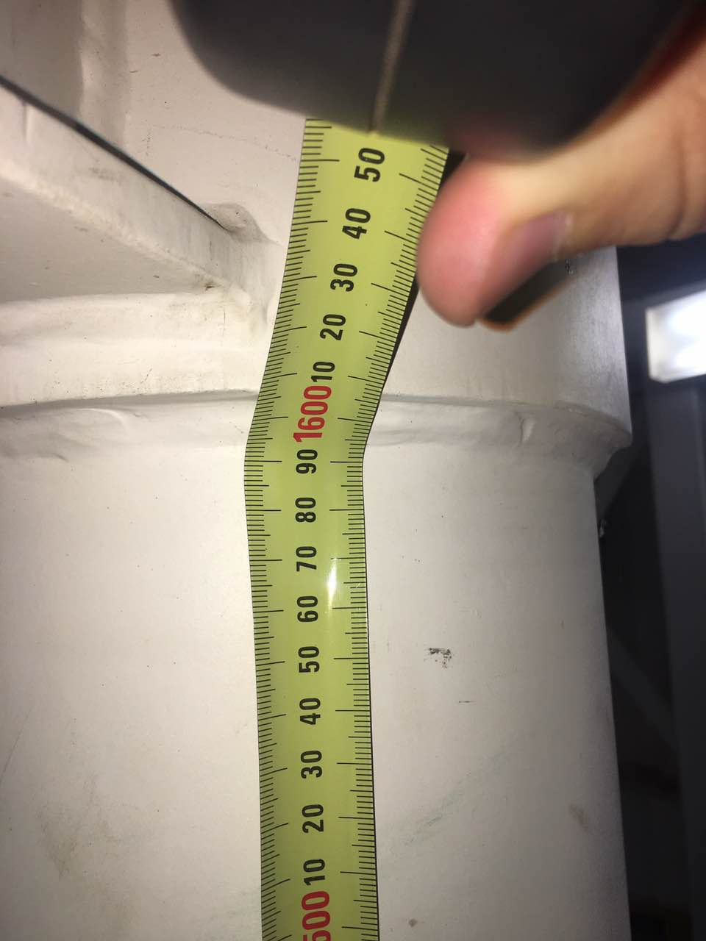
Working_Files/Dome_Photos/3A.jpg
