Kempf/GuidestarLaser/Working_Files/Dome_Photos/3B.jpg

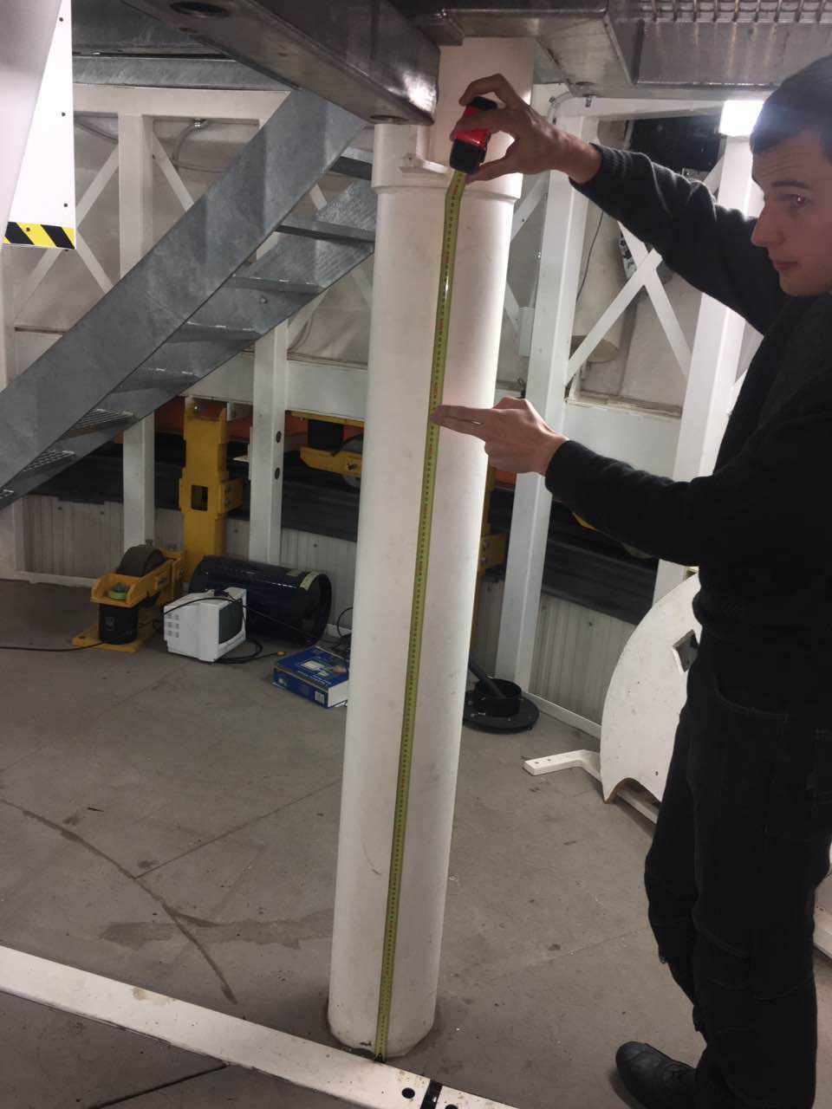
Working_Files/Dome_Photos/3B.jpg
