Kempf/GuidestarLaser/Working_Files/Dome_Photos/4A.jpg

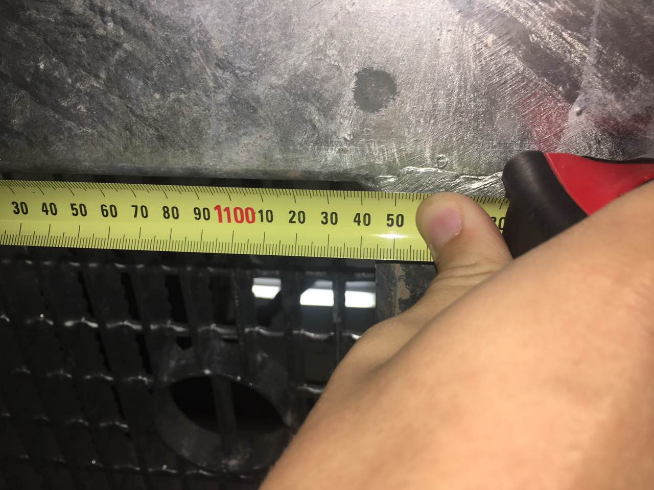
Working_Files/Dome_Photos/4A.jpg
