Kempf/GuidestarLaser/Working_Files/Dome_Photos/4B.jpg

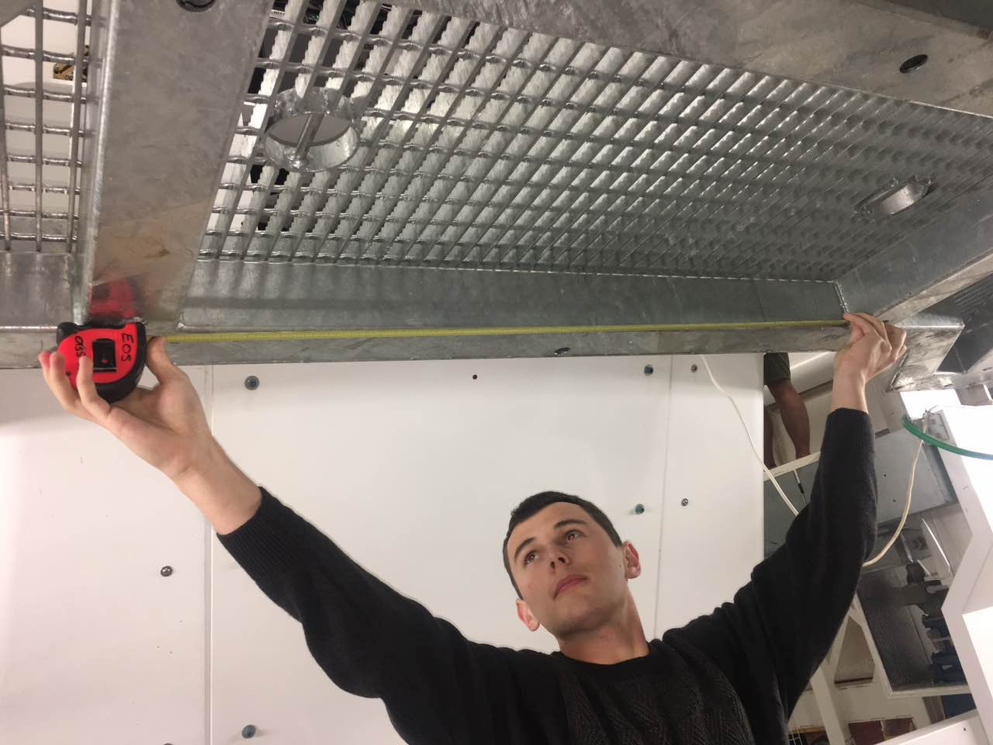
Working_Files/Dome_Photos/4B.jpg
