Kempf/GuidestarLaser/Working_Files/Dome_Photos/5A.jpg

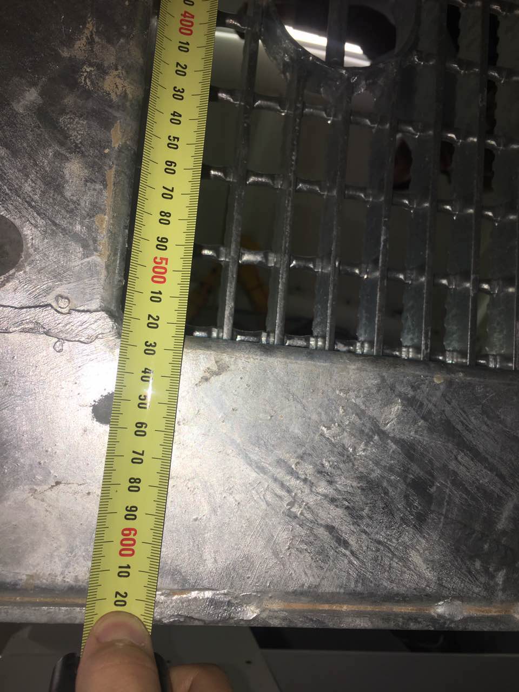
Working_Files/Dome_Photos/5A.jpg
