Kempf/GuidestarLaser/Working_Files/Dome_Photos/5B.jpg

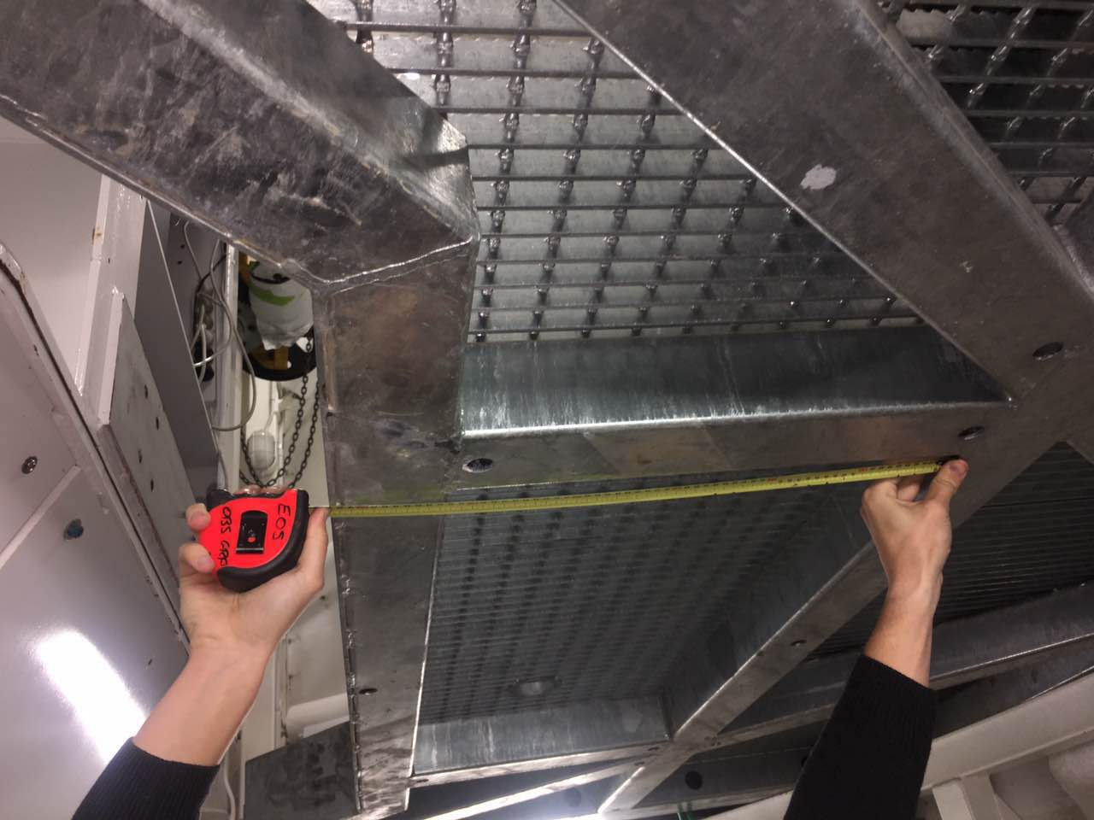
Working_Files/Dome_Photos/5B.jpg
