Kempf/GuidestarLaser/Working_Files/Dome_Photos/6A.jpg

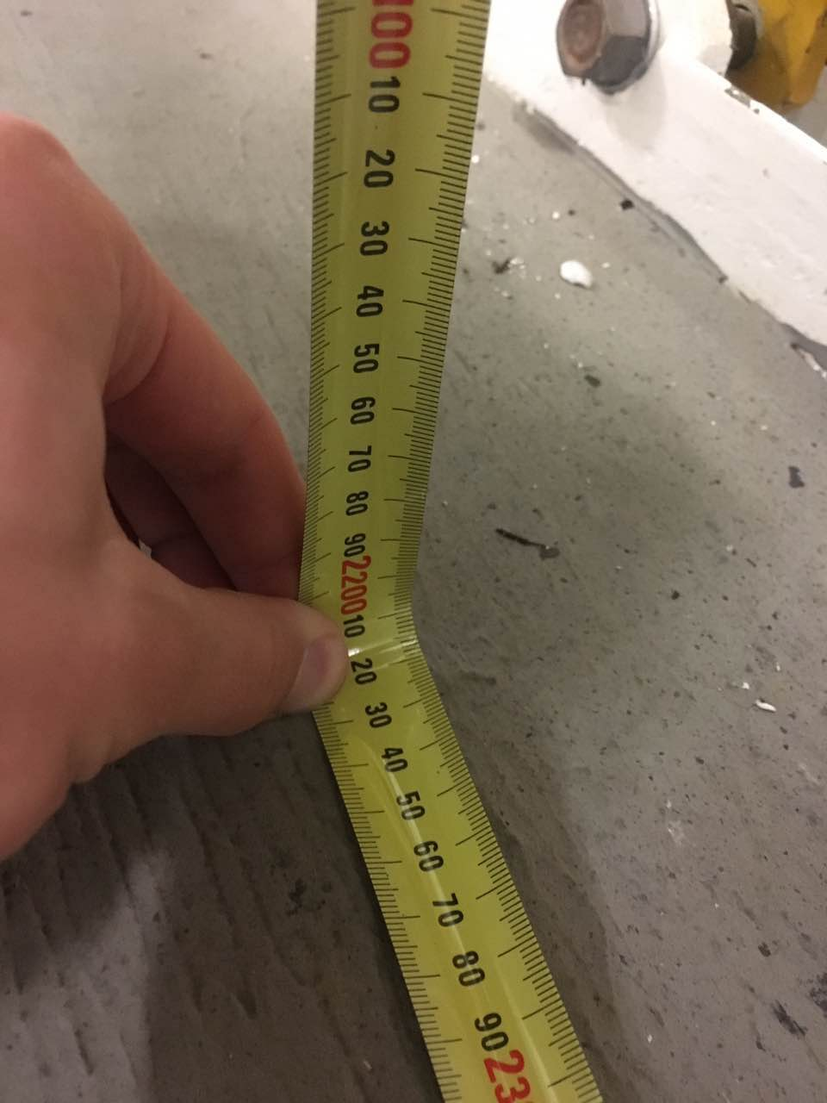
Working_Files/Dome_Photos/6A.jpg
