Kempf/GuidestarLaser/Working_Files/Dome_Photos/6B.jpg

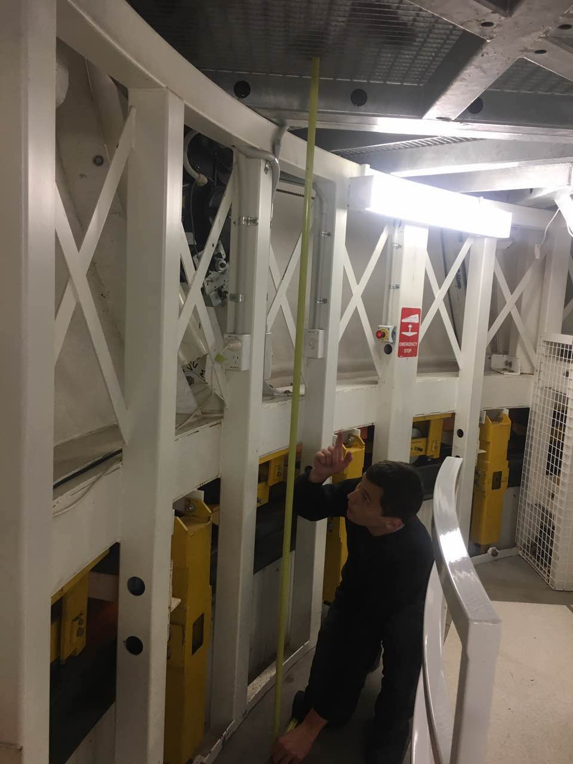
Working_Files/Dome_Photos/6B.jpg
