Kempf/GuidestarLaser/Working_Files/Dome_Photos/7A.jpg

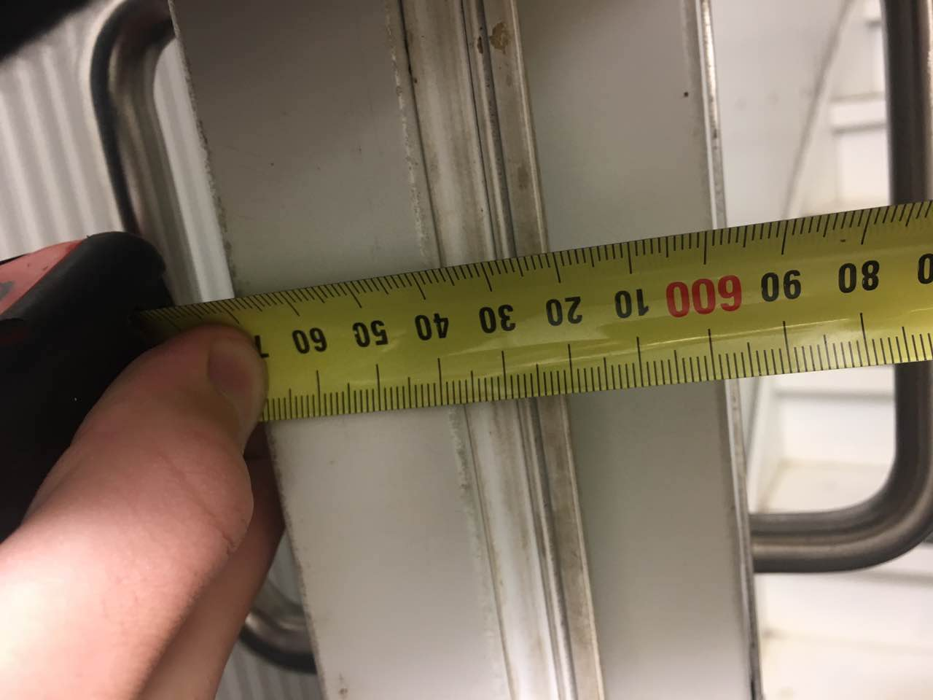
Working_Files/Dome_Photos/7A.jpg
