Kempf/GuidestarLaser/Working_Files/Dome_Photos/7B.jpg

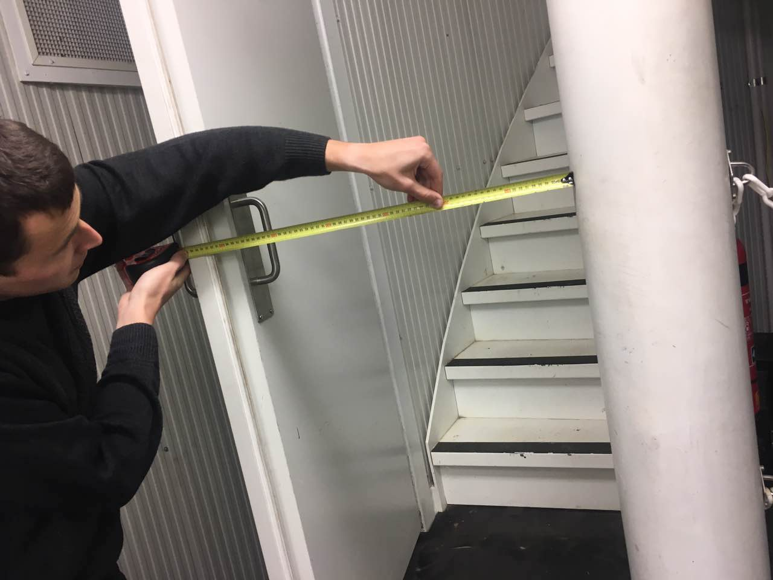
Working_Files/Dome_Photos/7B.jpg
