Kempf/GuidestarLaser/Working_Files/Dome_Photos/8A.jpg

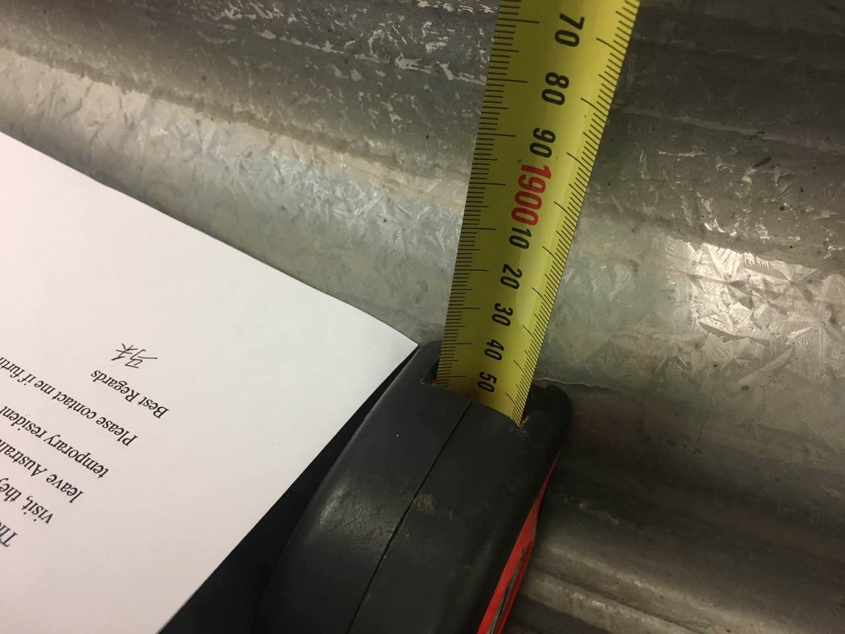
Working_Files/Dome_Photos/8A.jpg
