Kempf/GuidestarLaser/Working_Files/Dome_Photos/8B.jpg

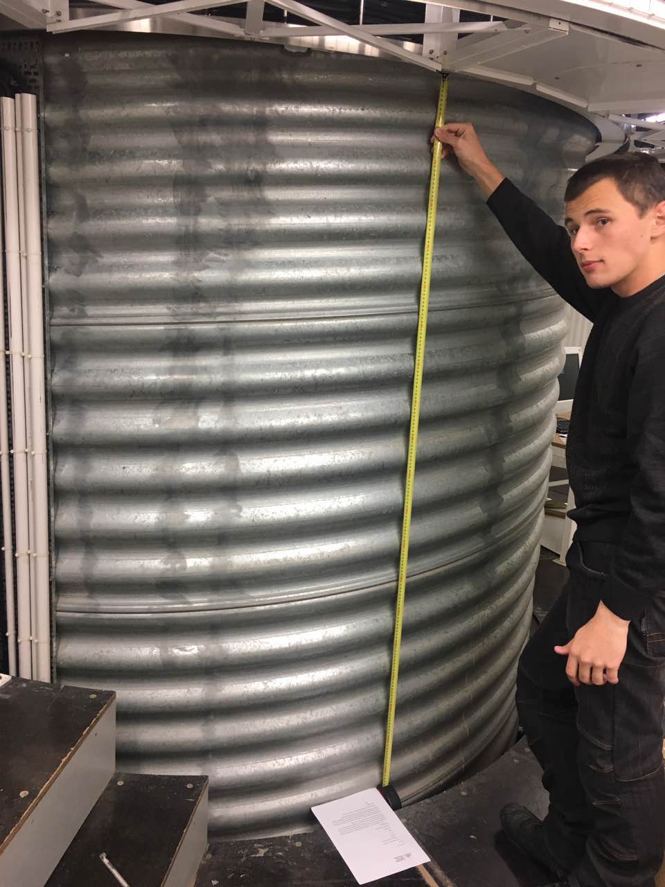
Working_Files/Dome_Photos/8B.jpg
