Kempf/GuidestarLaser/Working_Files/Dome_Photos/9A.jpg

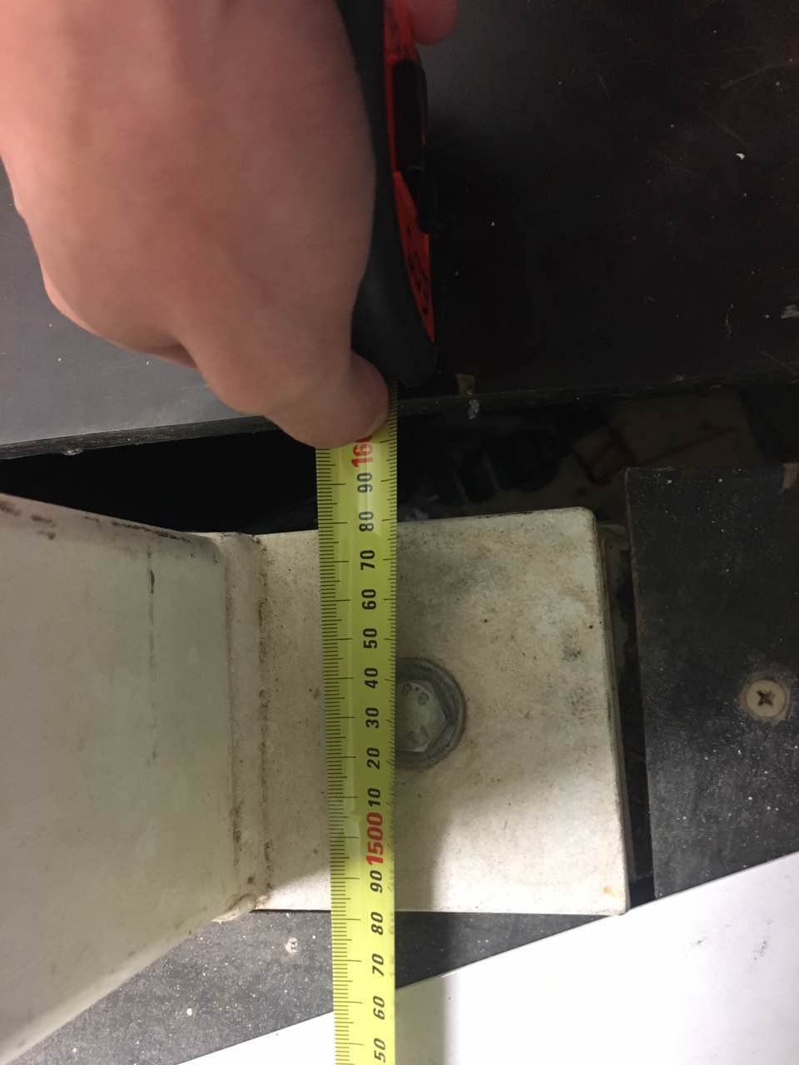
Working_Files/Dome_Photos/9A.jpg
