Kempf/GuidestarLaser/Working_Files/Dome_Photos/9B.jpg

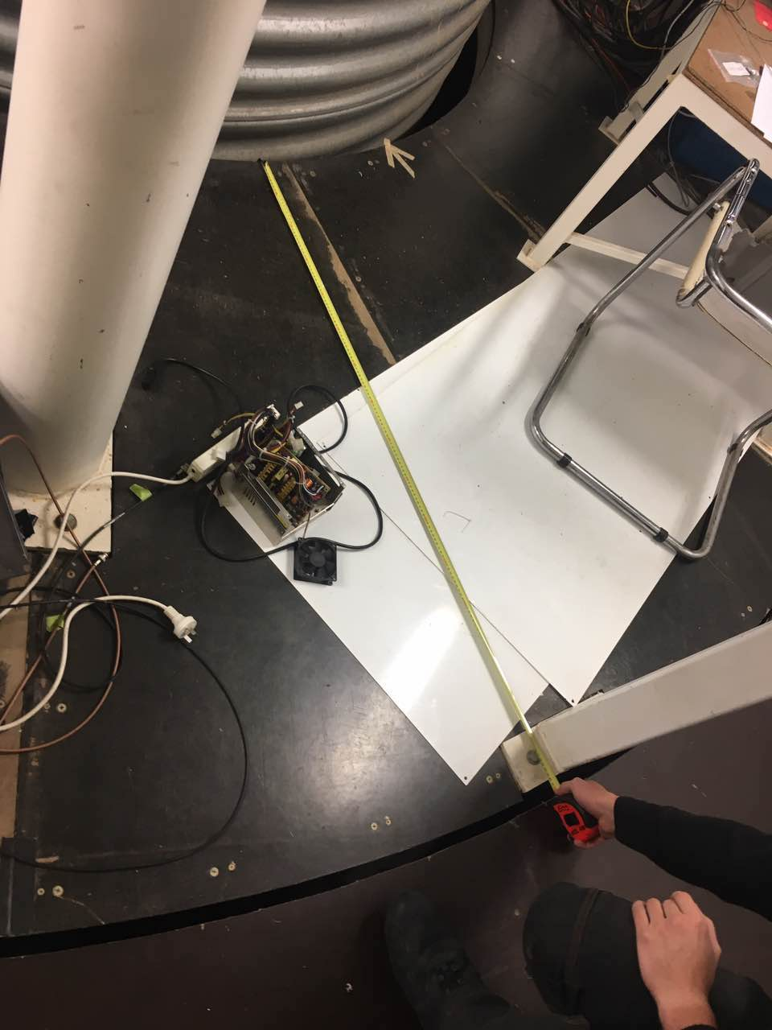
Working_Files/Dome_Photos/9B.jpg
