Kempf/GuidestarLaser/Working_Files/Dome_Photos/10A.jpg

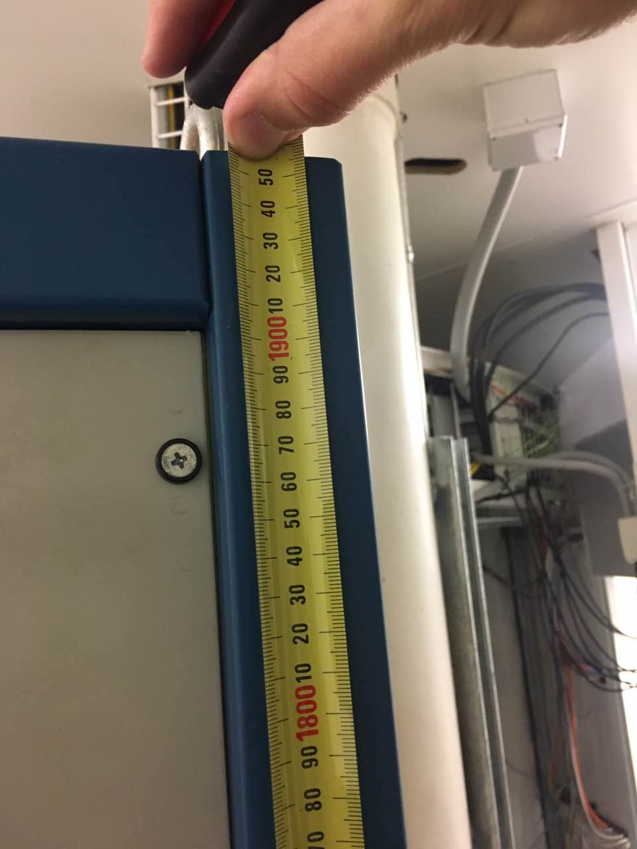
Working_Files/Dome_Photos/10A.jpg
