Kempf/GuidestarLaser/Working_Files/Dome_Photos/10B.jpg

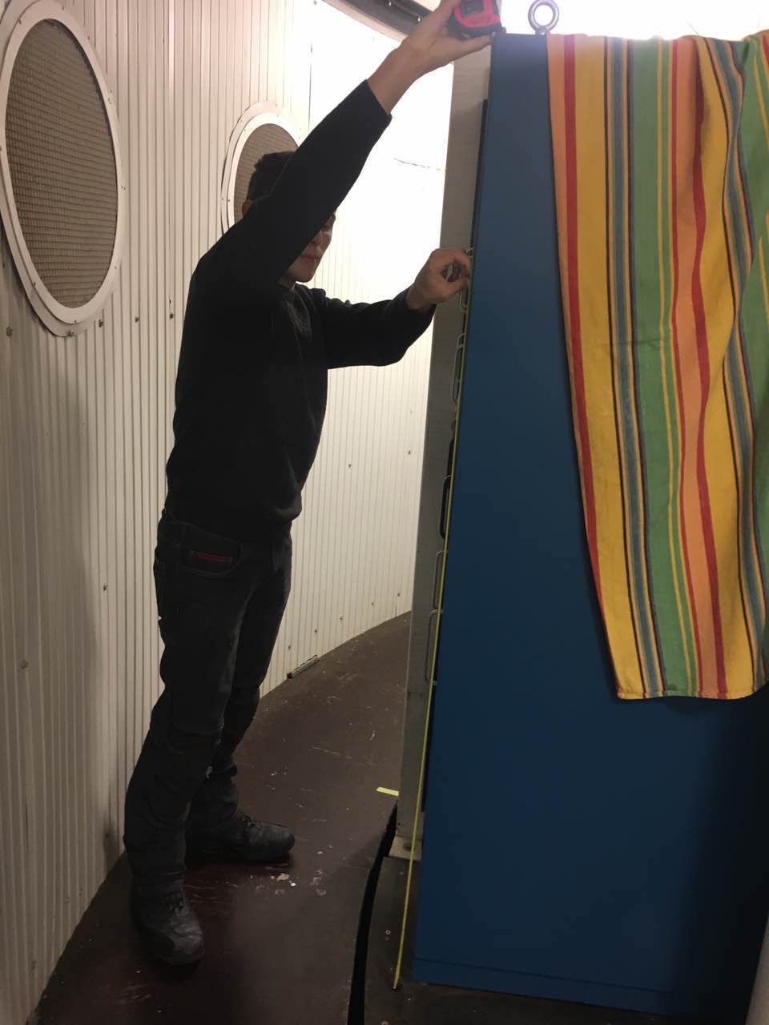
Working_Files/Dome_Photos/10B.jpg
