Kempf/GuidestarLaser/Working_Files/Dome_Photos/11A.jpg

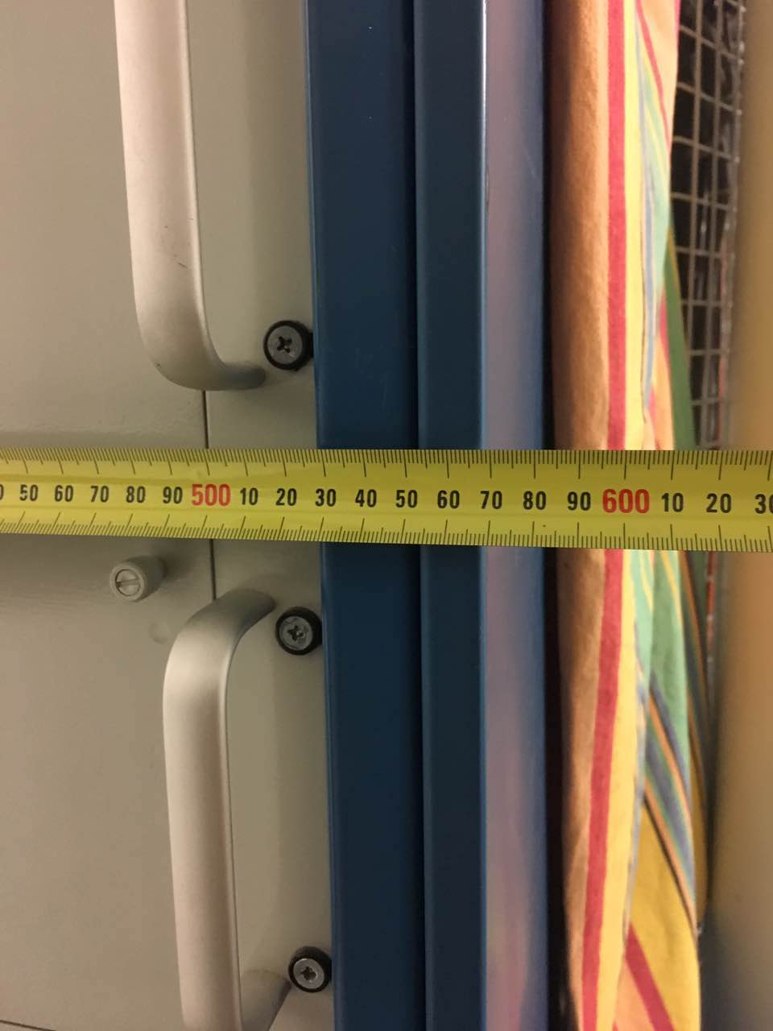
Working_Files/Dome_Photos/11A.jpg
