Kempf/GuidestarLaser/Working_Files/Dome_Photos/11B.jpg

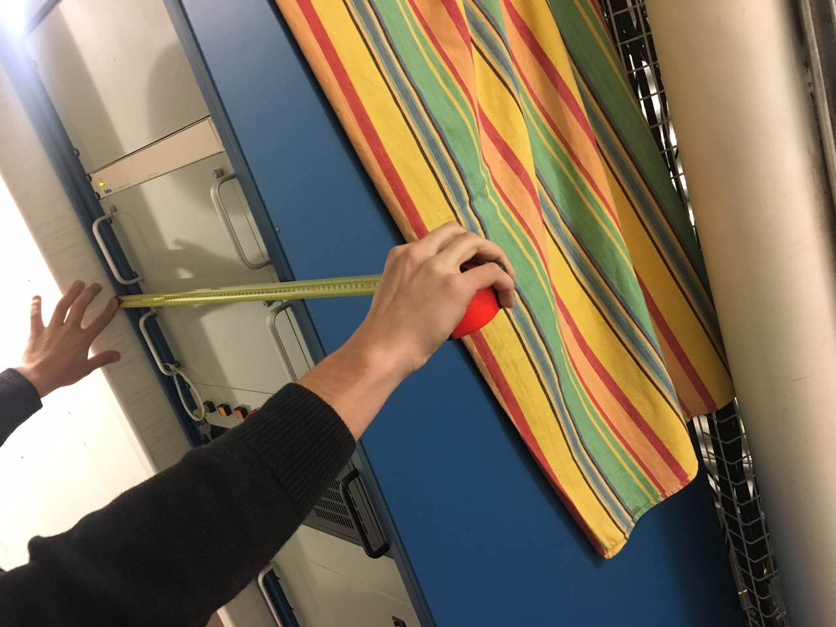
Working_Files/Dome_Photos/11B.jpg
