Kempf/GuidestarLaser/Working_Files/Dome_Photos/12A.jpg

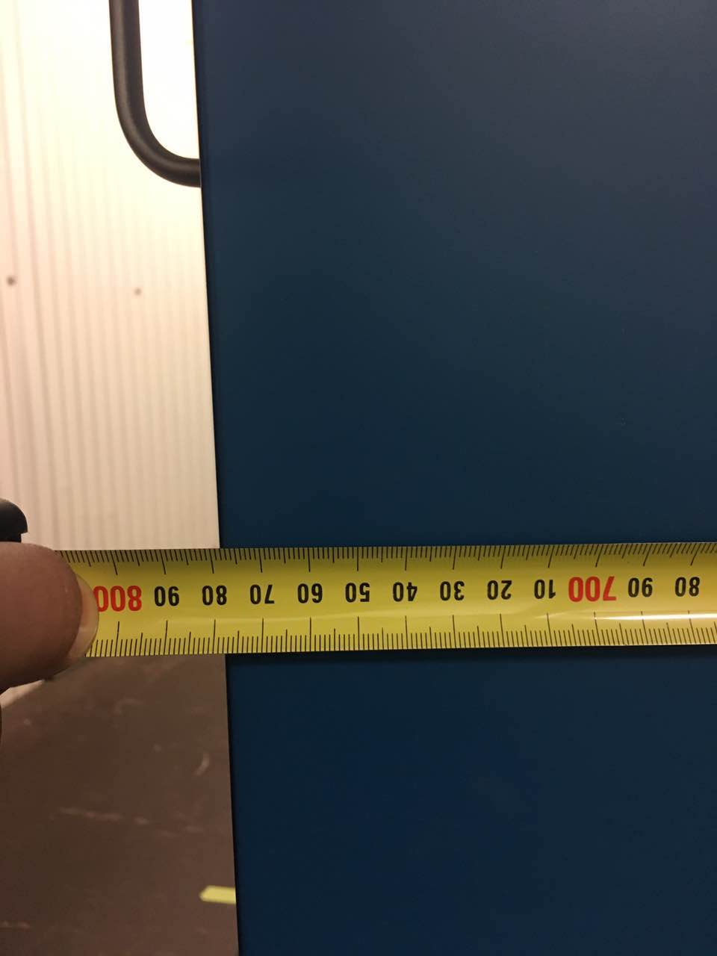
Working_Files/Dome_Photos/12A.jpg
