Kempf/GuidestarLaser/Working_Files/Dome_Photos/12B.jpg

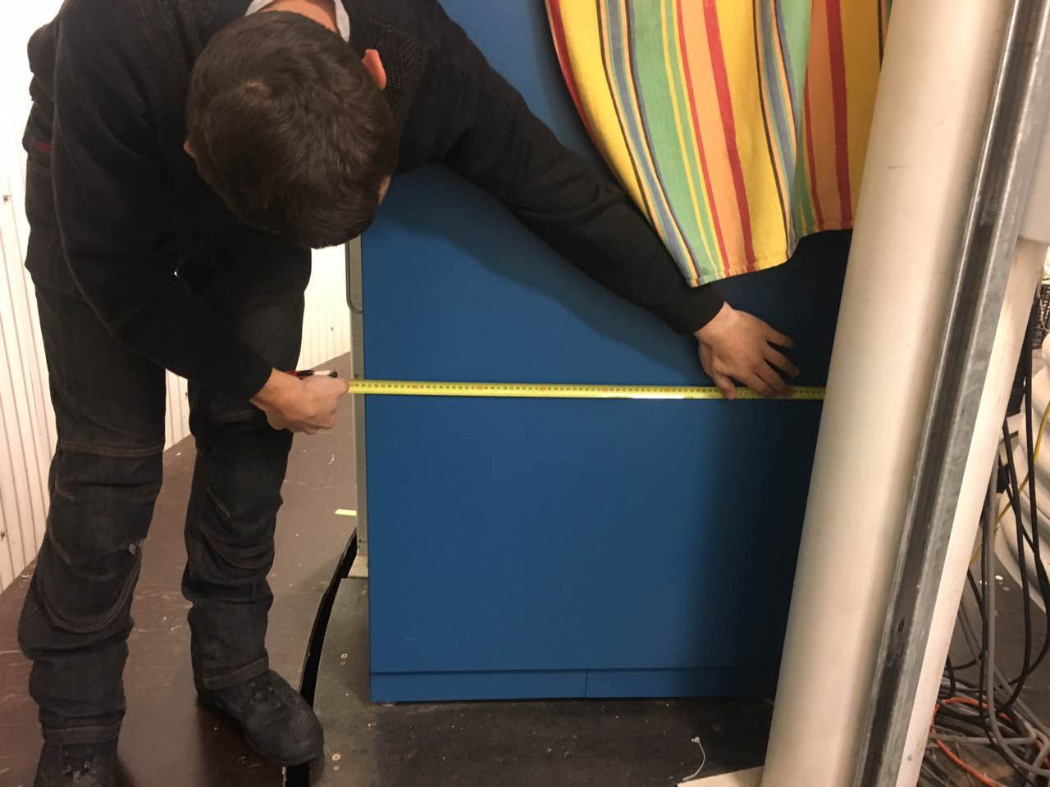
Working_Files/Dome_Photos/12B.jpg
