Kempf/GuidestarLaser/Working_Files/Dome_Photos/13A.jpg

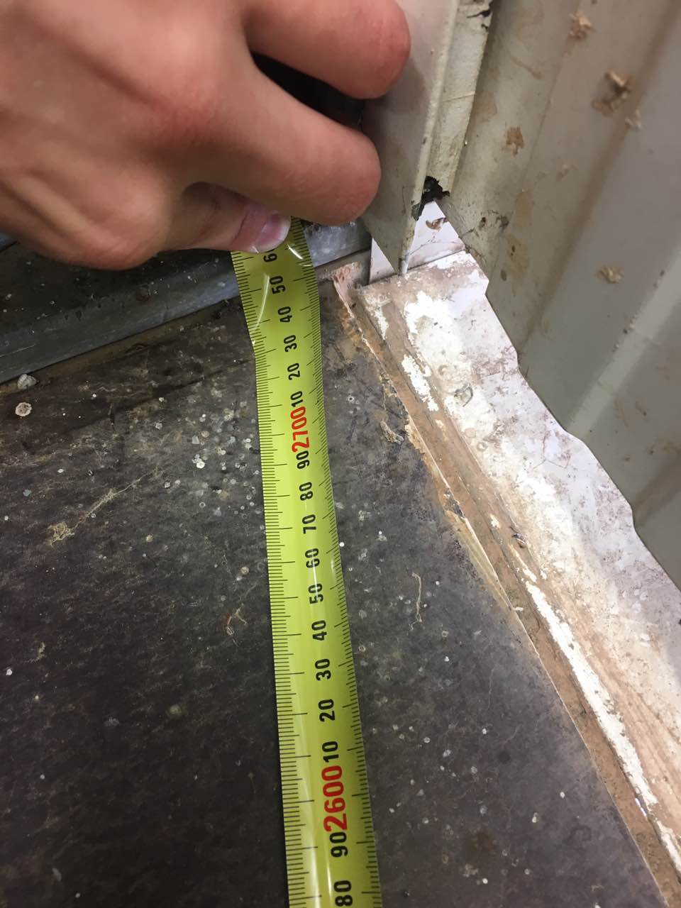
Working_Files/Dome_Photos/13A.jpg
