Kempf/GuidestarLaser/Working_Files/Dome_Photos/13B.jpg

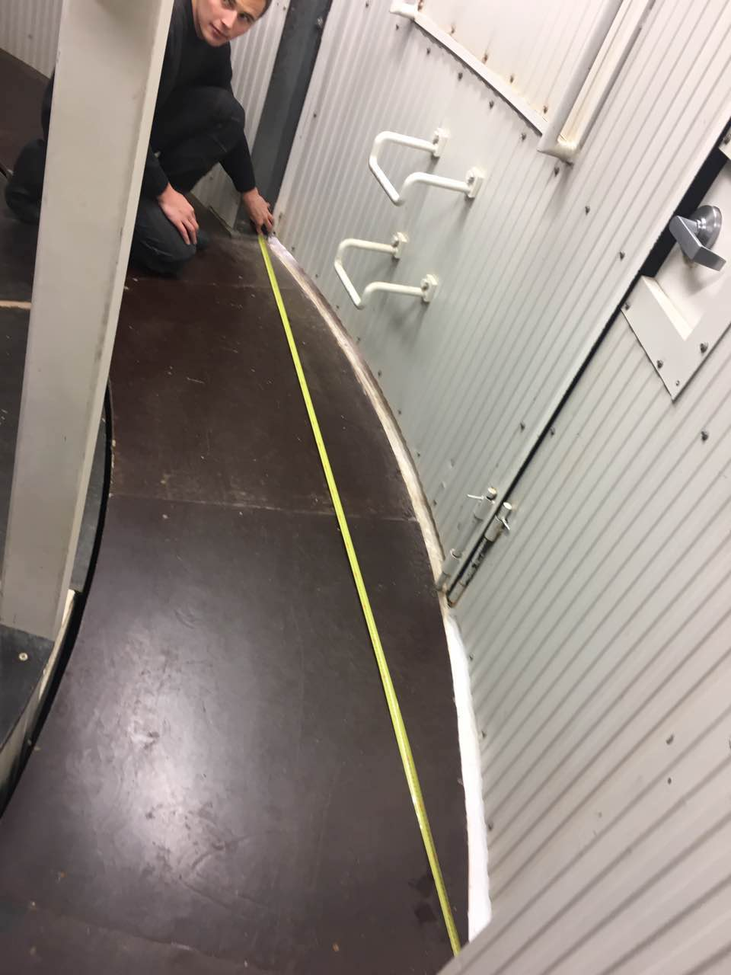
Working_Files/Dome_Photos/13B.jpg
