Kempf/GuidestarLaser/Working_Files/Dome_Photos/14A.jpg

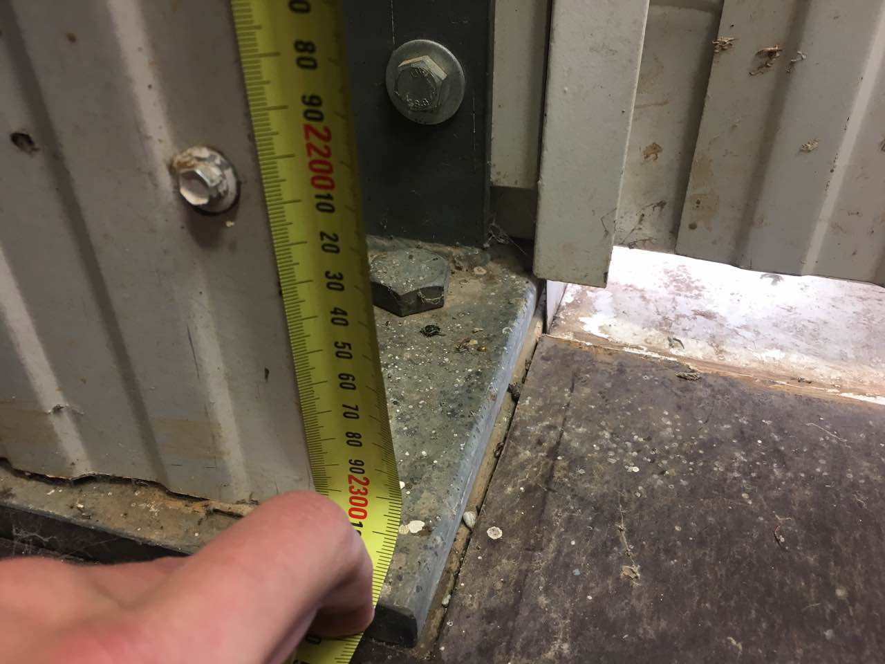
Working_Files/Dome_Photos/14A.jpg
