Kempf/GuidestarLaser/Working_Files/Dome_Photos/14B.jpg

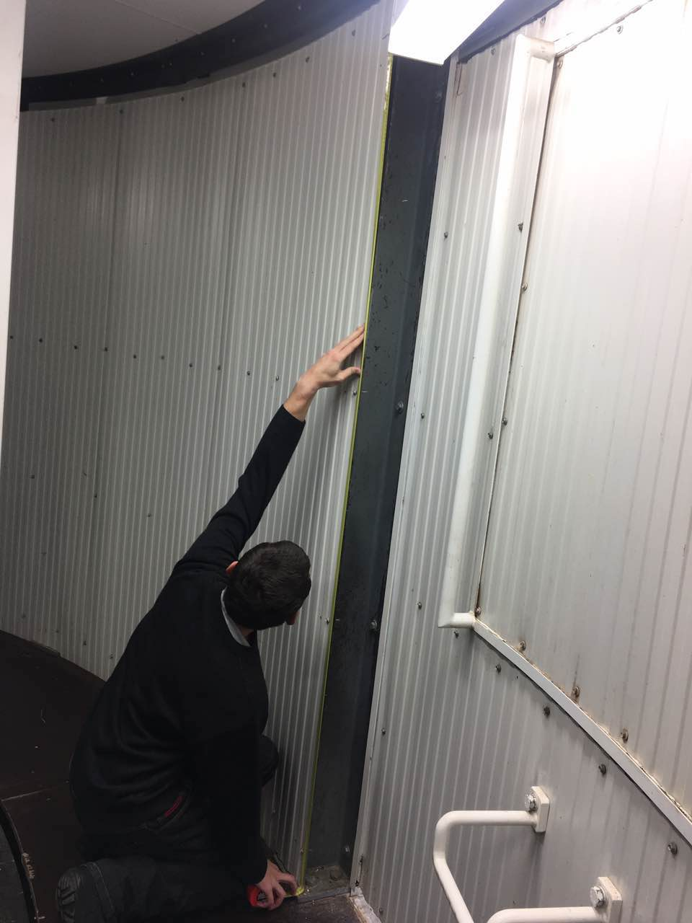
Working_Files/Dome_Photos/14B.jpg
