Kempf/GuidestarLaser/Working_Files/Electrical_Interface_Preliminary_Design/levels.png

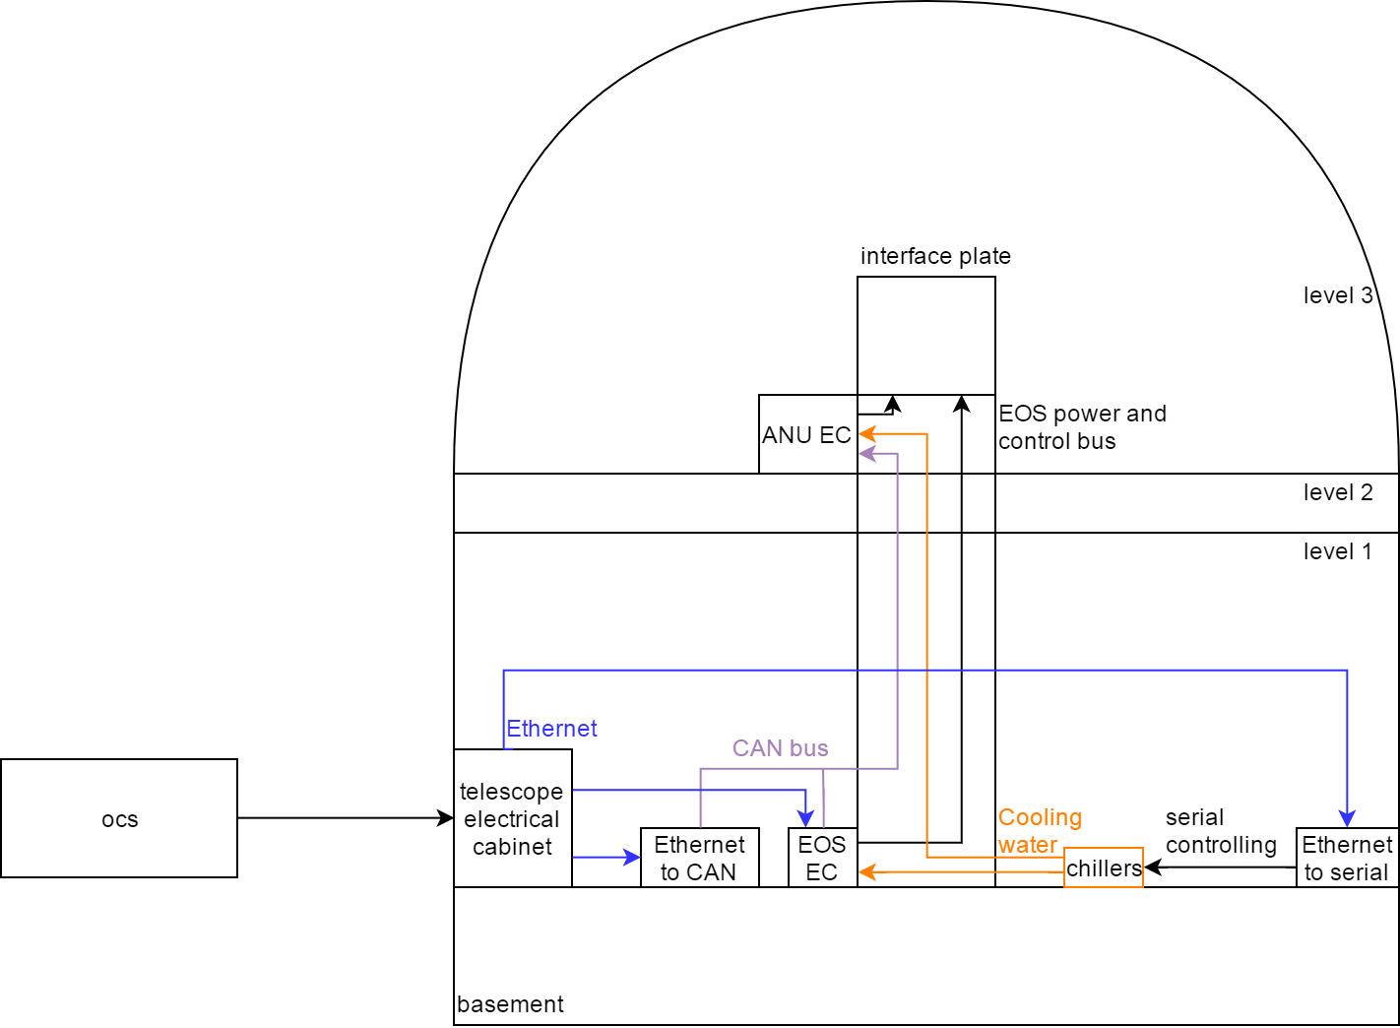
Working_Files/Electrical_Interface_Preliminary_Design/levels.png
