Kempf/GuidestarLaser/Working_Files/Electrical_Interface_Preliminary_Design/top_level.png

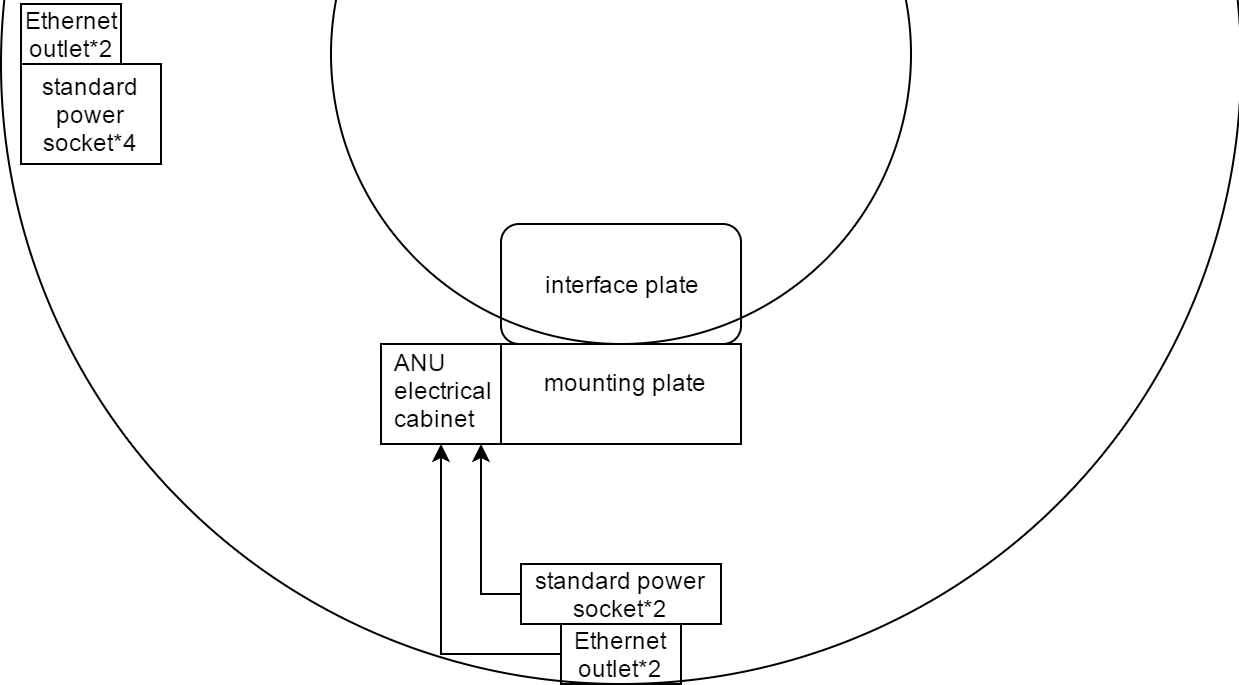
Working_Files/Electrical_Interface_Preliminary_Design/top_level.png
