Kempf/GuidestarLaser/Working_Files/Environmental_Interface_Preliminary_Design/Air2.PNG

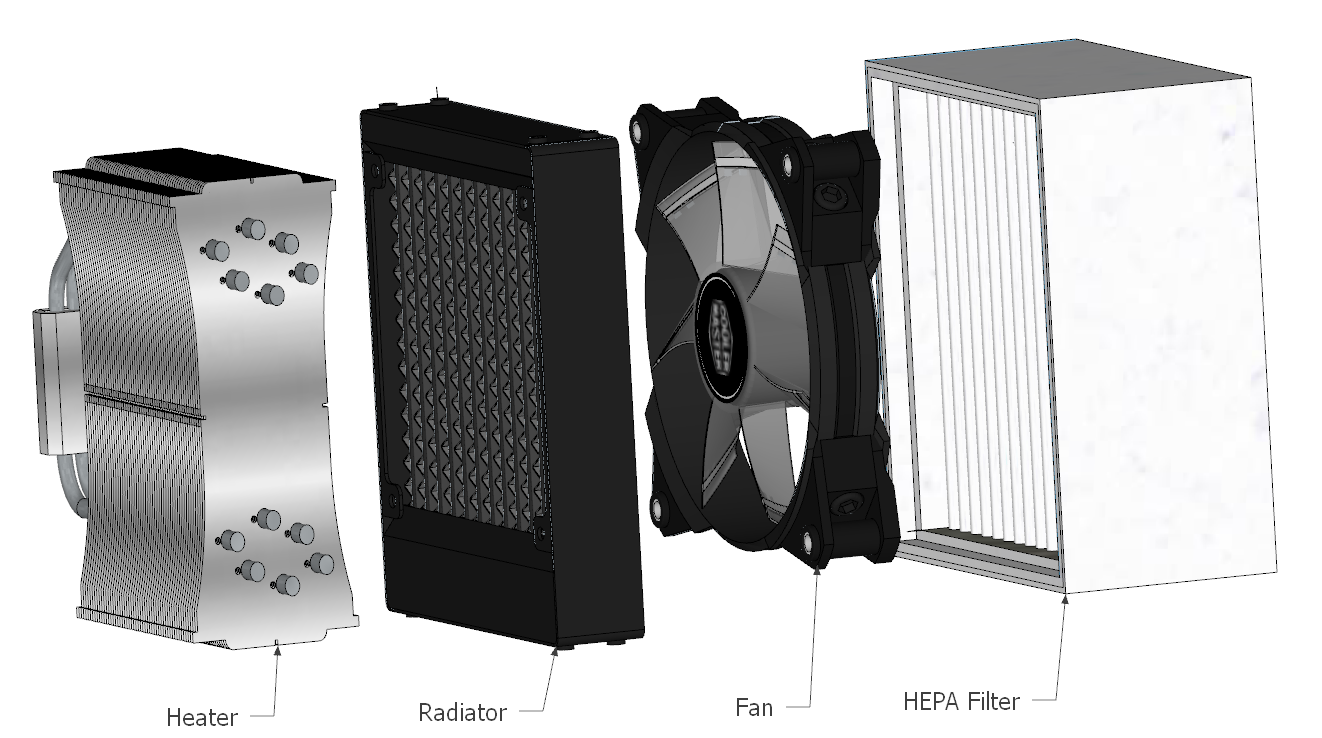
Working_Files/Environmental_Interface_Preliminary_Design/Air2.PNG
