Kempf/GuidestarLaser/Working_Files/Environmental_Interface_Preliminary_Design/AirflowSystemModel.png

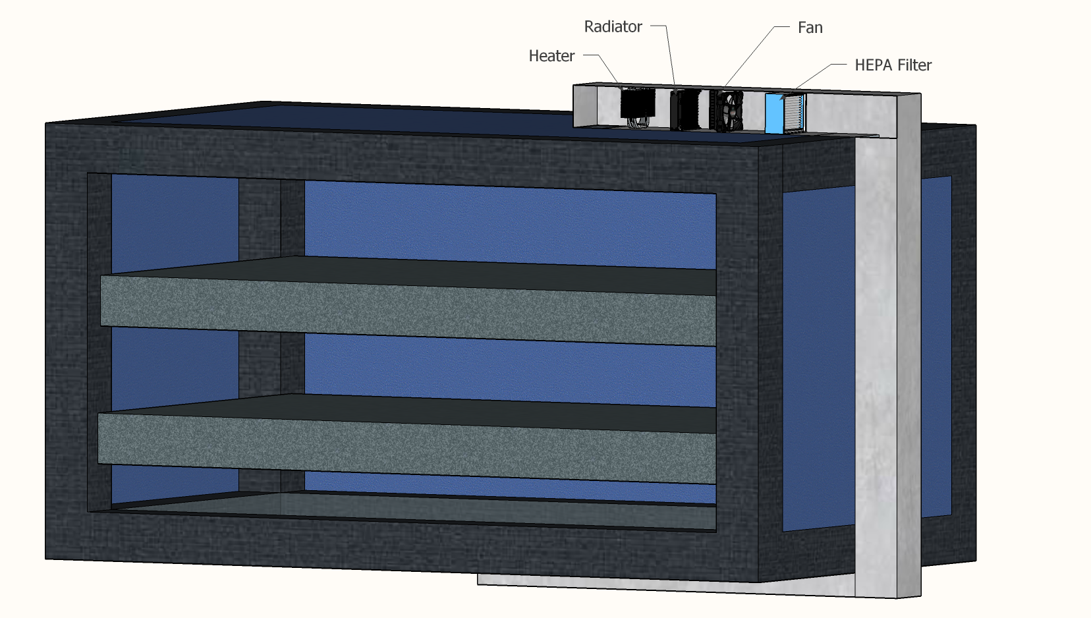
Working_Files/Environmental_Interface_Preliminary_Design/AirflowSystemModel.png
