Kempf/GuidestarLaser/Working_Files/Environmental_Interface_Preliminary_Design/cooling.png

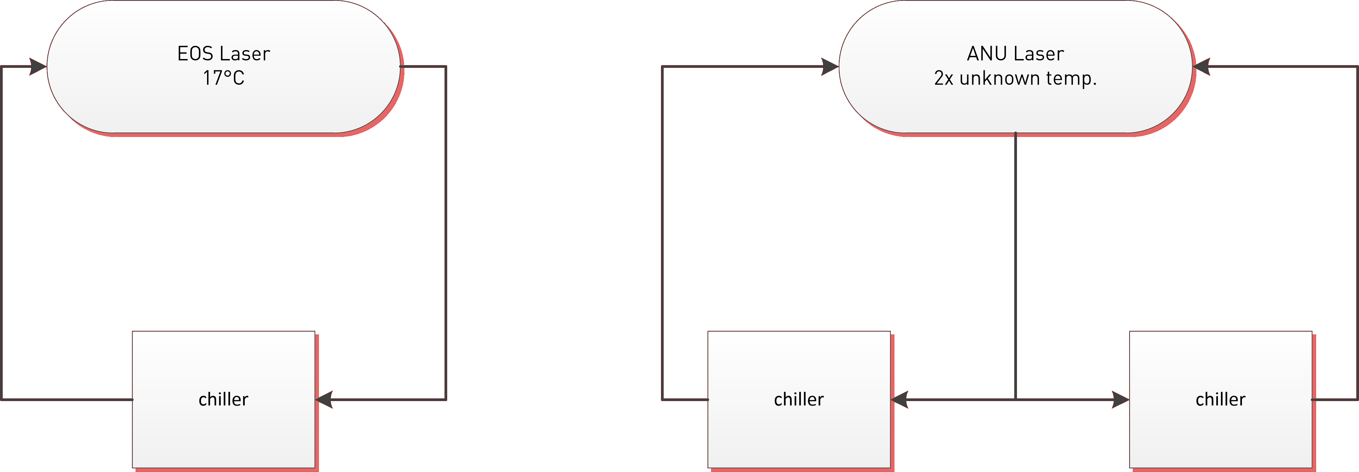
Working_Files/Environmental_Interface_Preliminary_Design/cooling.png
