Kempf/GuidestarLaser/Working_Files/Environmental_Interface_Preliminary_Design/Diagramv2.png

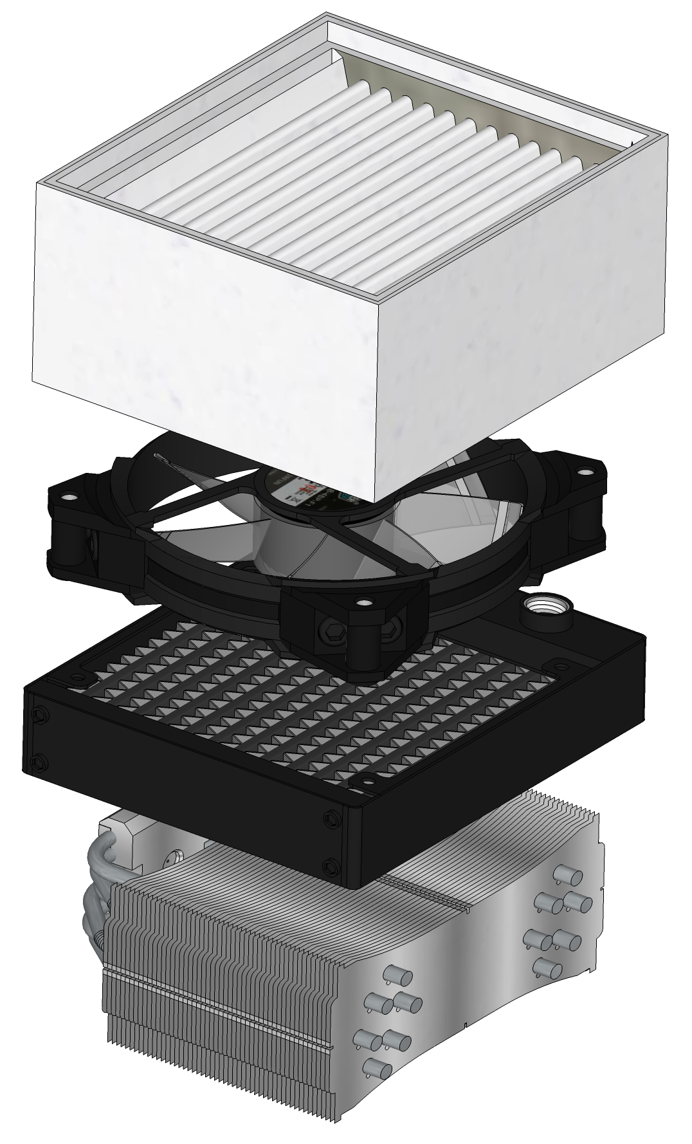
Working_Files/Environmental_Interface_Preliminary_Design/Diagramv2.png
