Kempf/GuidestarLaser/Working_Files/Environmental_Interface_Preliminary_Design/mat.png

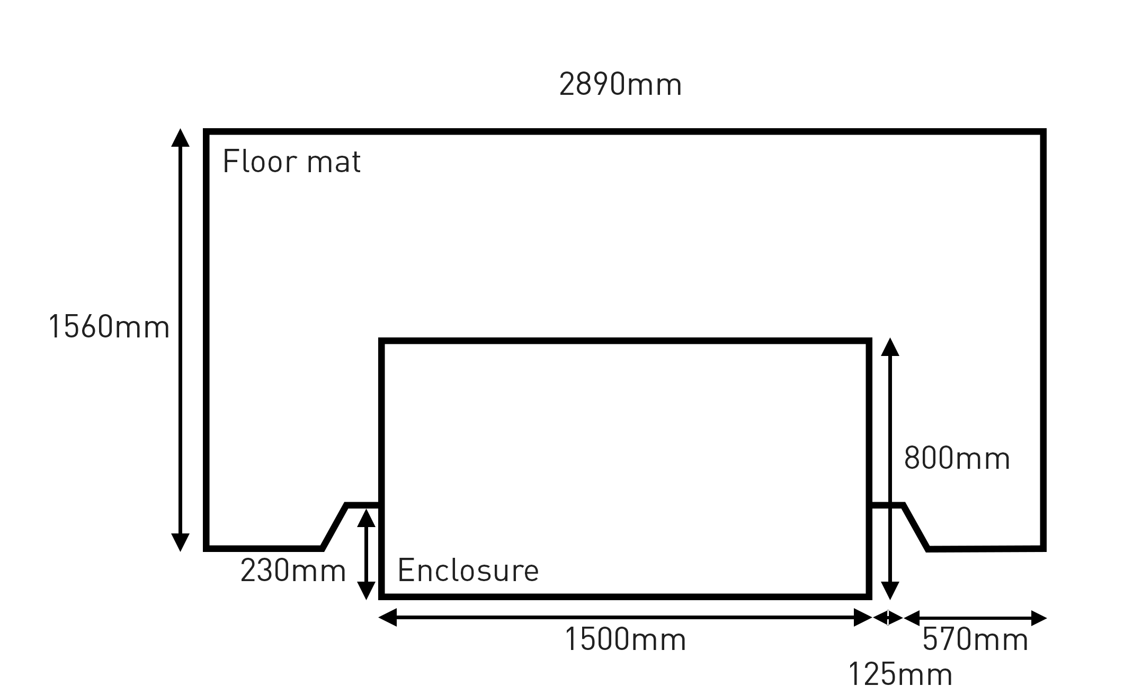
Working_Files/Environmental_Interface_Preliminary_Design/mat.png
