Kempf/GuidestarLaser/Working_Files/Figures/breadboard_interface.PNG

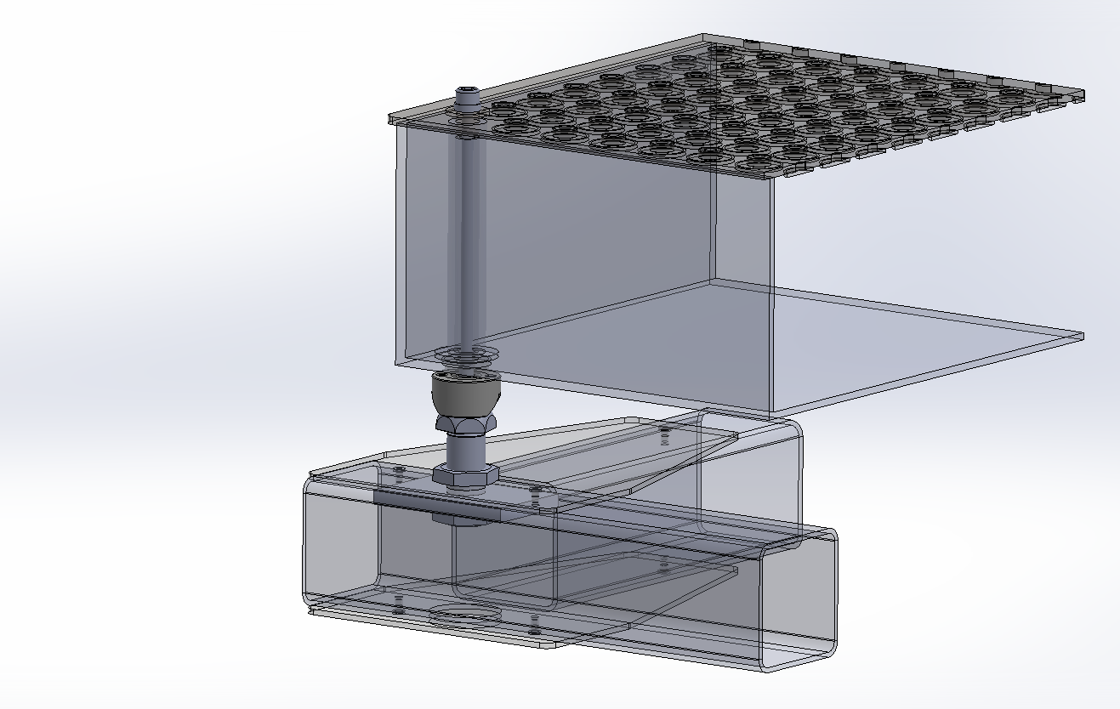
Working_Files/Figures/breadboard_interface.PNG
