Kempf/GuidestarLaser/Working_Files/Figures/c1.png

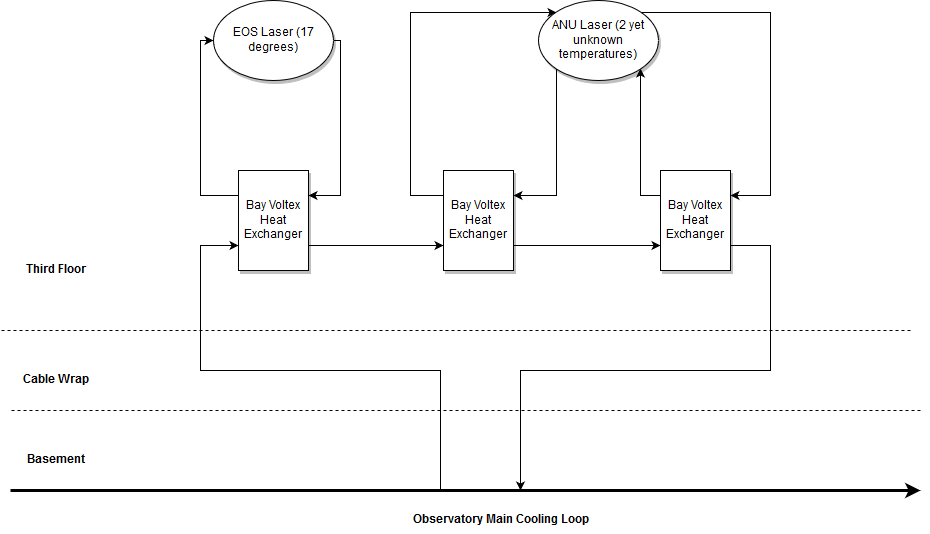
Working_Files/Figures/c1.png
