Kempf/GuidestarLaser/Working_Files/Figures/c3.png

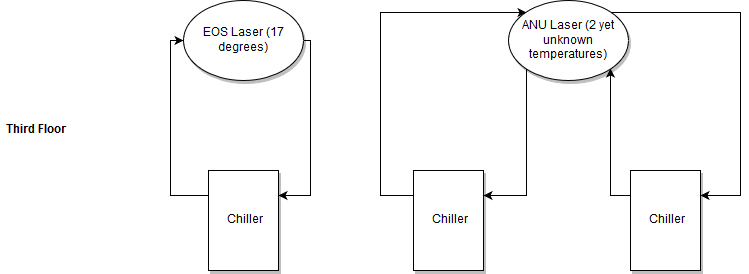
Working_Files/Figures/c3.png
