Kempf/GuidestarLaser/Working_Files/Figures/Cabling Diagram.PNG

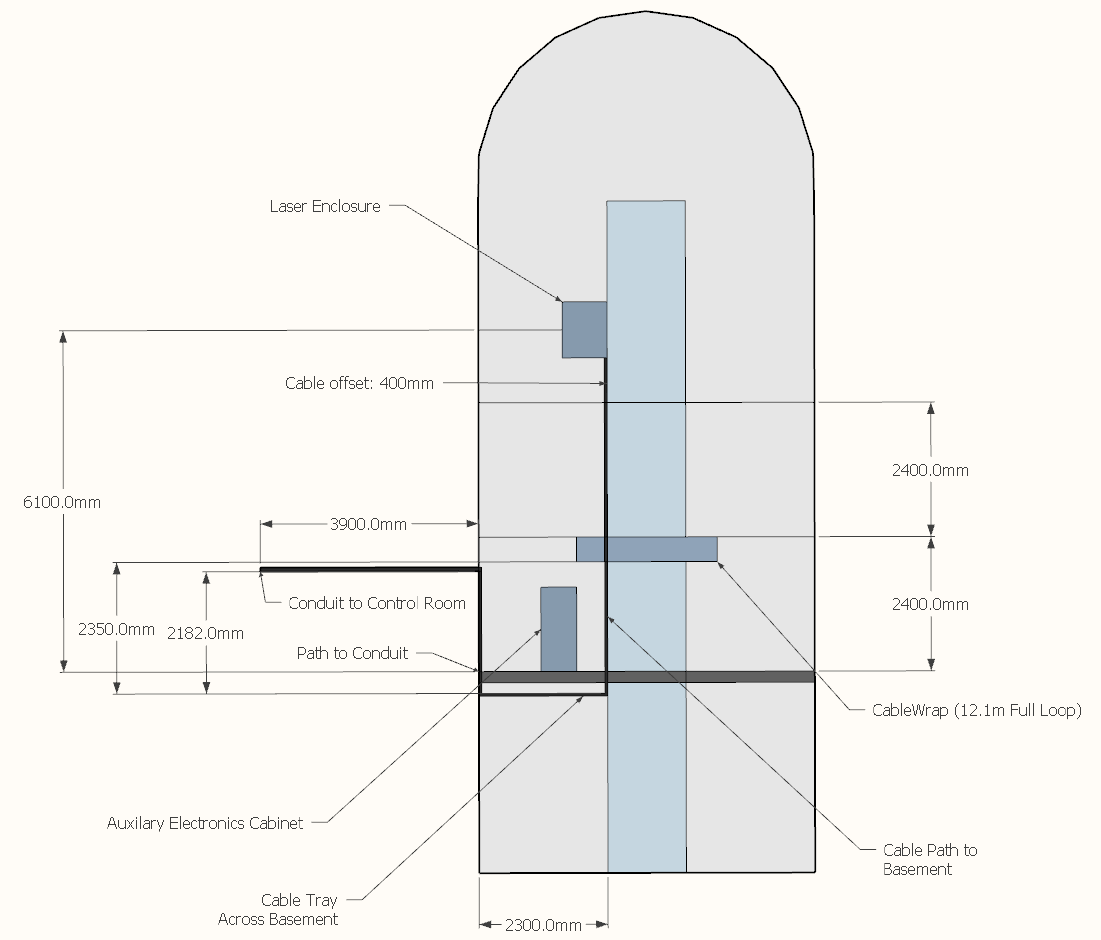
Working_Files/Figures/Cabling Diagram.PNG
