Kempf/GuidestarLaser/Working_Files/Figures/dome_w_frame.PNG

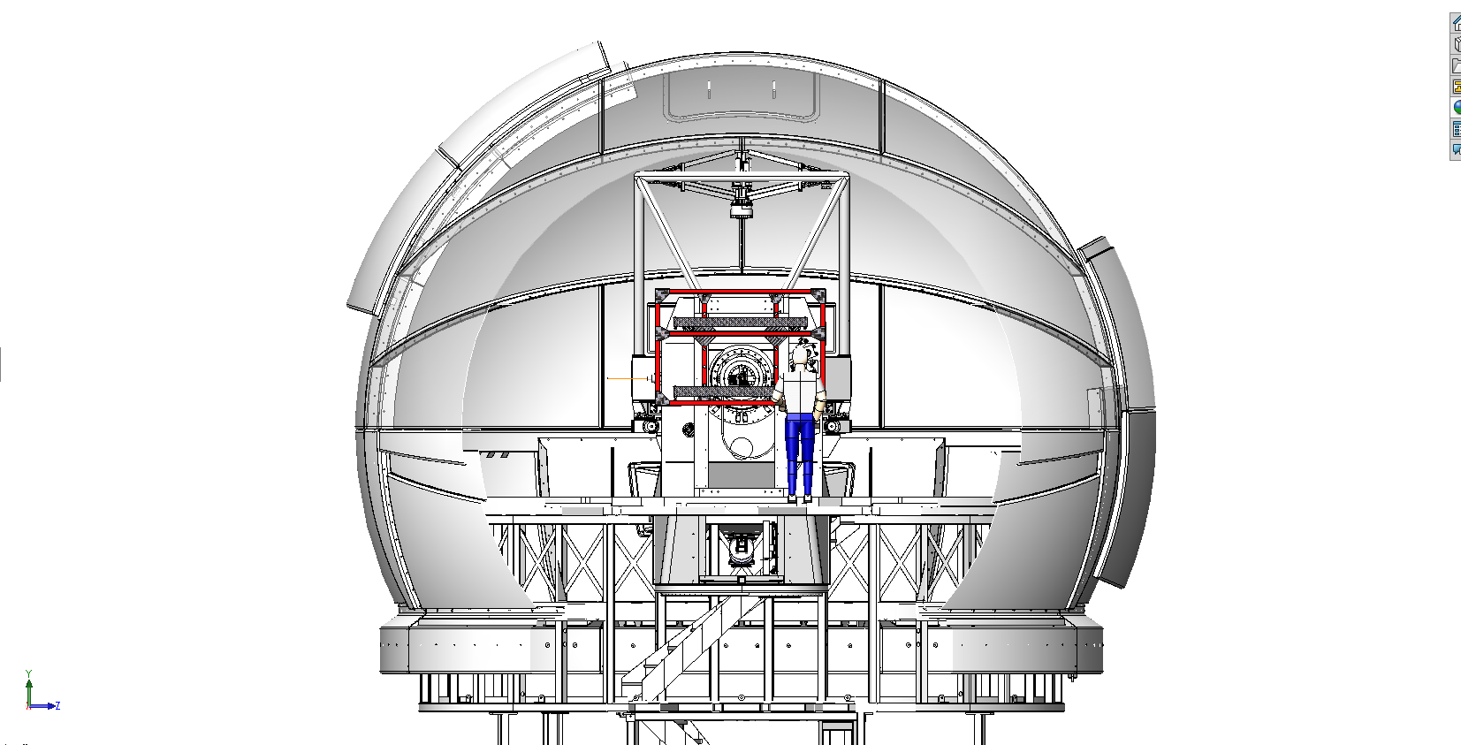
Working_Files/Figures/dome_w_frame.PNG
