Kempf/GuidestarLaser/Working_Files/Figures/gantt.png

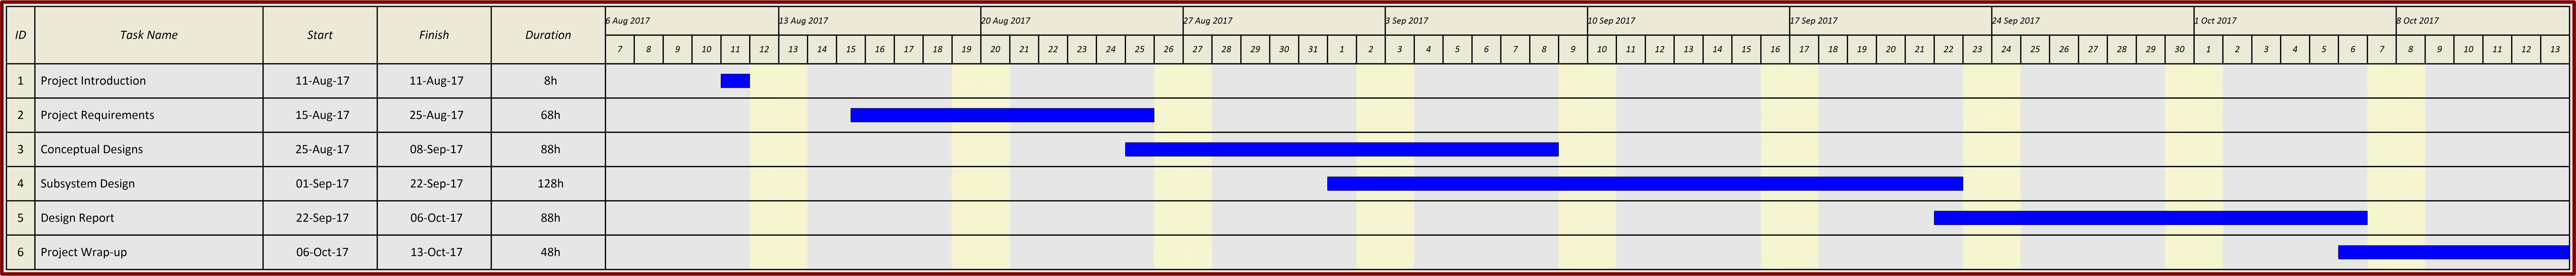
Working_Files/Figures/gantt.png
