Kempf/GuidestarLaser/Working_Files/Figures/Im1.PNG

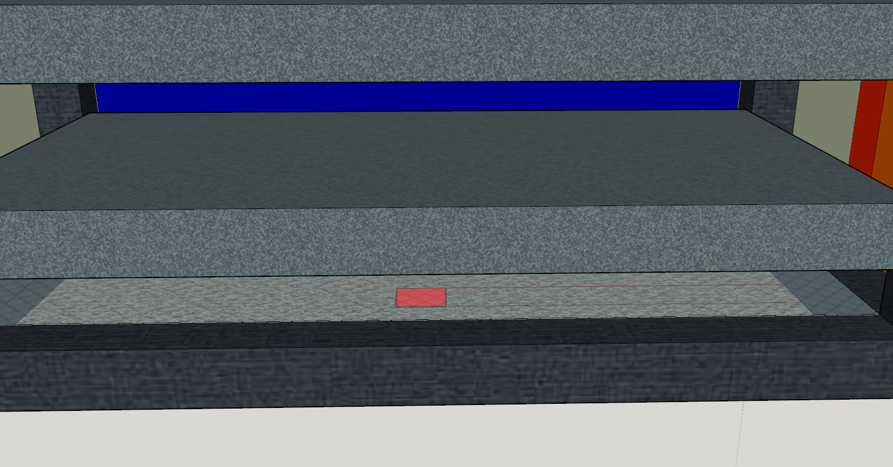
Working_Files/Figures/Im1.PNG
