Kempf/GuidestarLaser/Working_Files/Figures/im2.PNG

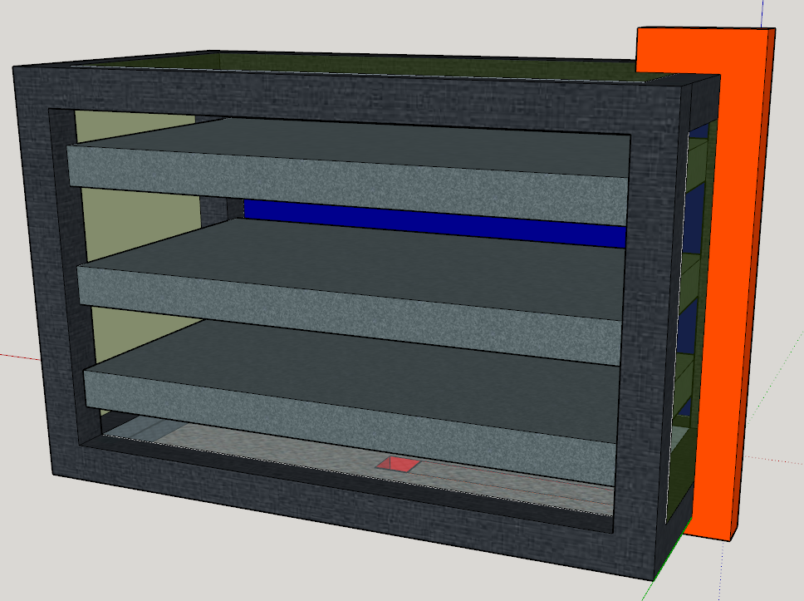
Working_Files/Figures/im2.PNG
