Kempf/GuidestarLaser/Working_Files/Figures/interconnections.PNG

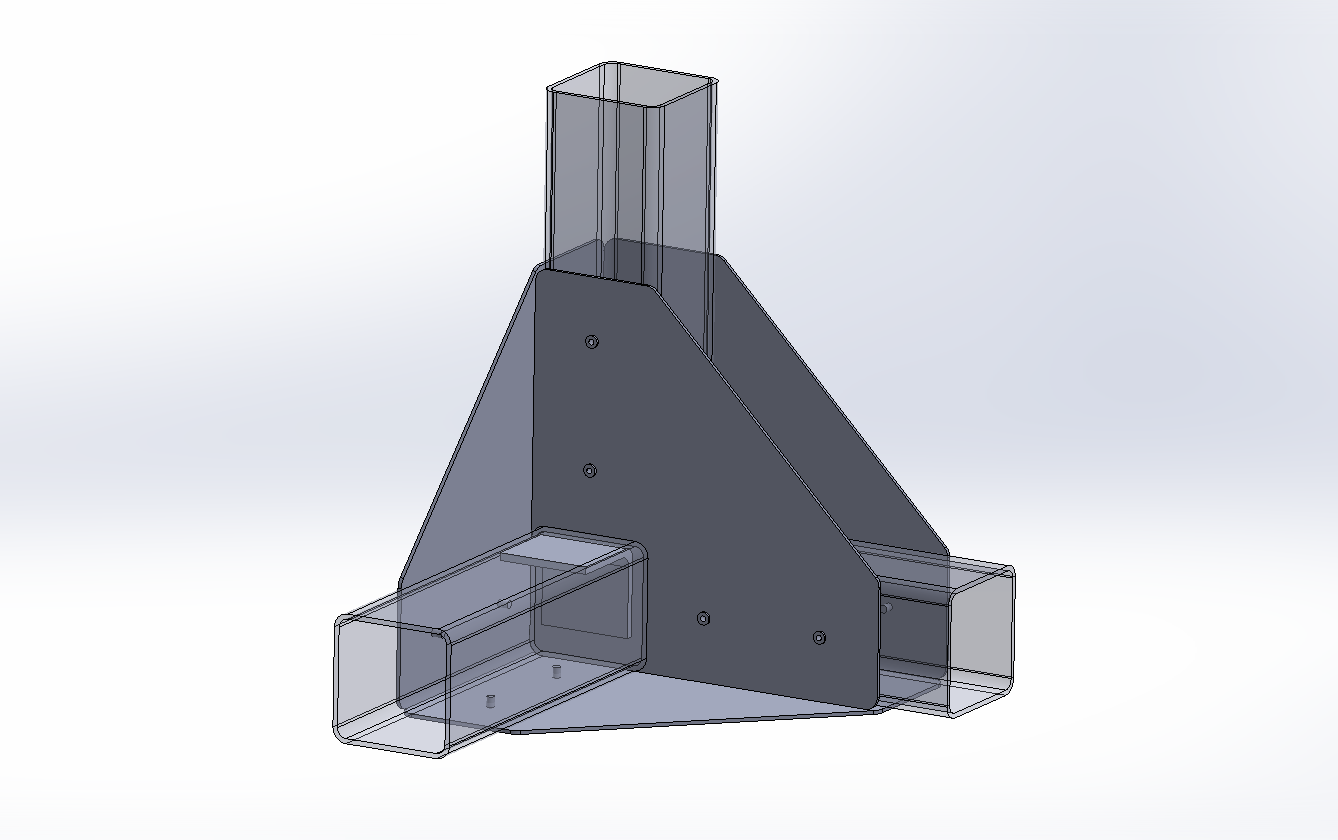
Working_Files/Figures/interconnections.PNG
