Kempf/GuidestarLaser/Working_Files/Figures/mat.png

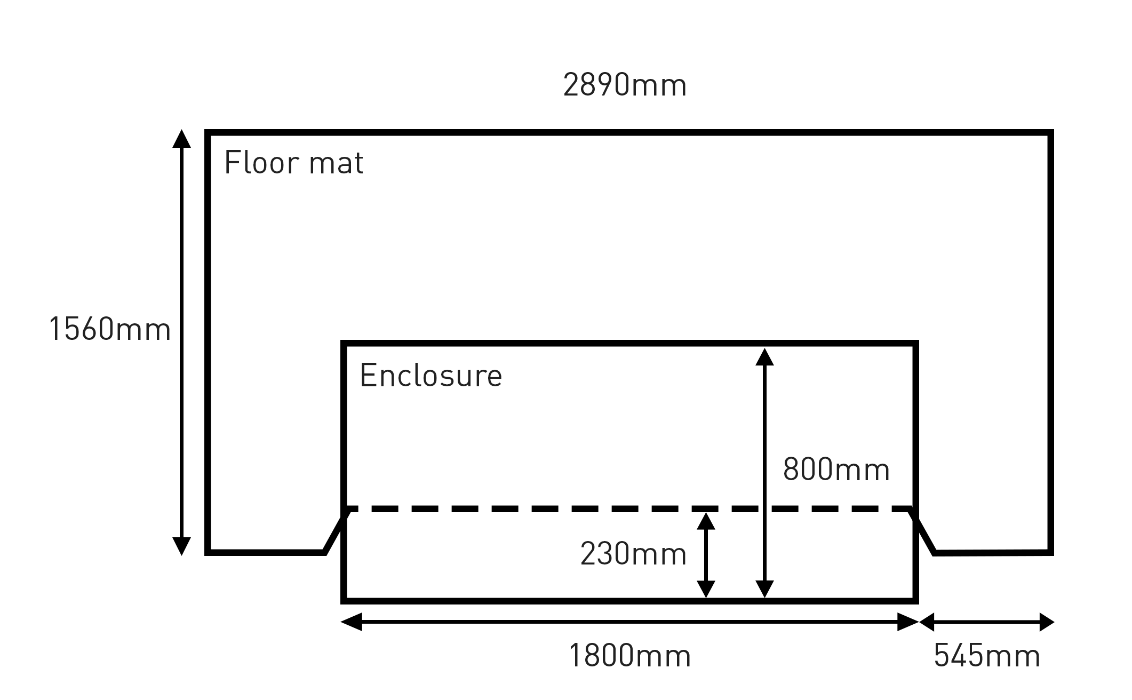
Working_Files/Figures/mat.png
