Kempf/GuidestarLaser/Working_Files/Figures/mounting_plate_interface.PNG

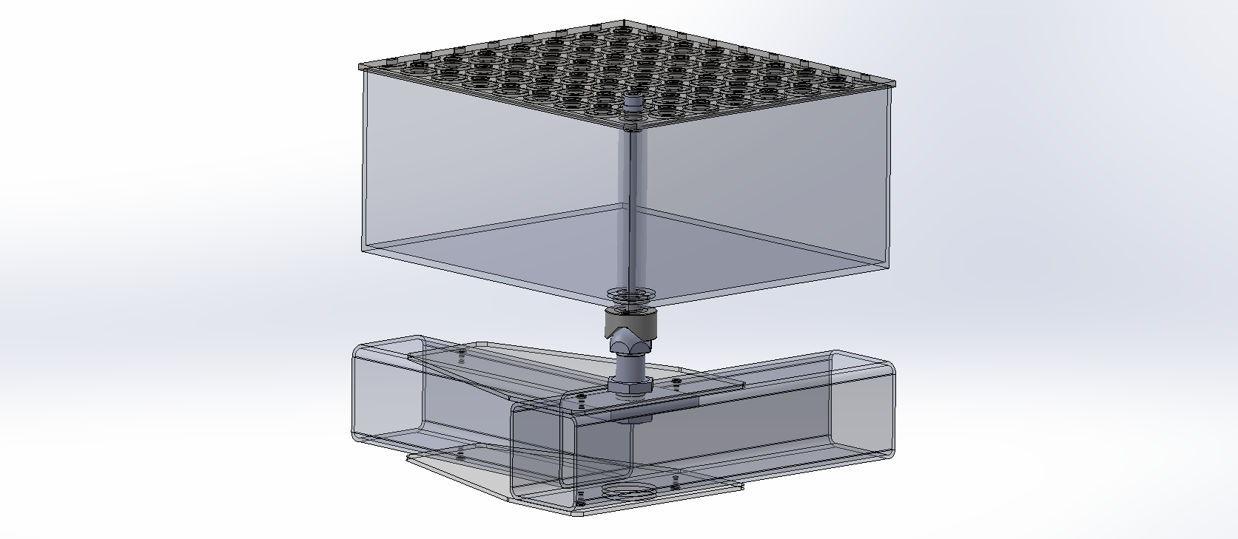
Working_Files/Figures/mounting_plate_interface.PNG
