Kempf/GuidestarLaser/Working_Files/Figures/telescope_outside_cropped.png

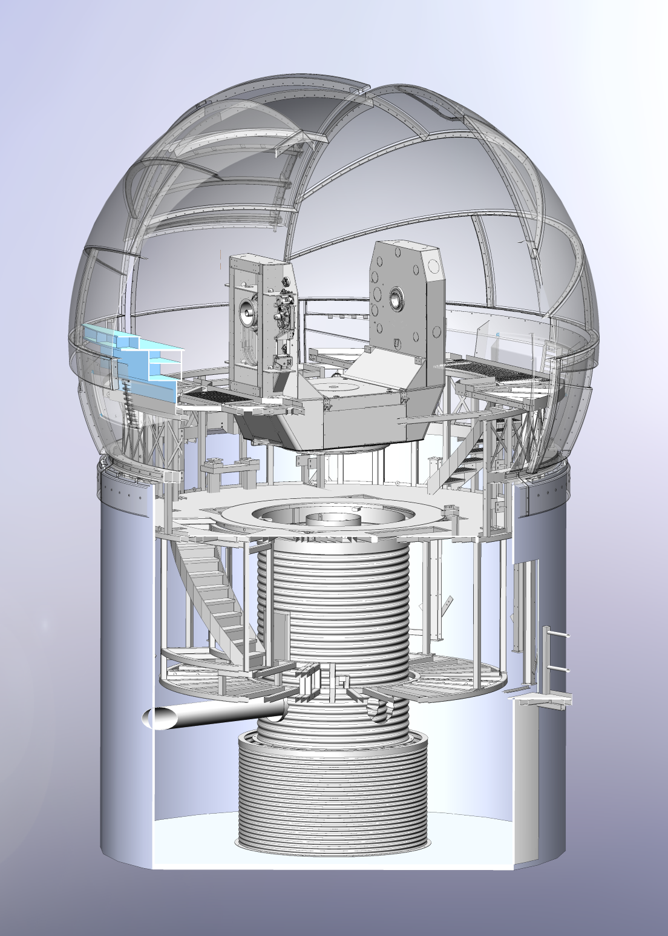
Working_Files/Figures/telescope_outside_cropped.png
