Kempf/GuidestarLaser/Working_Files/Figures/vib2.png

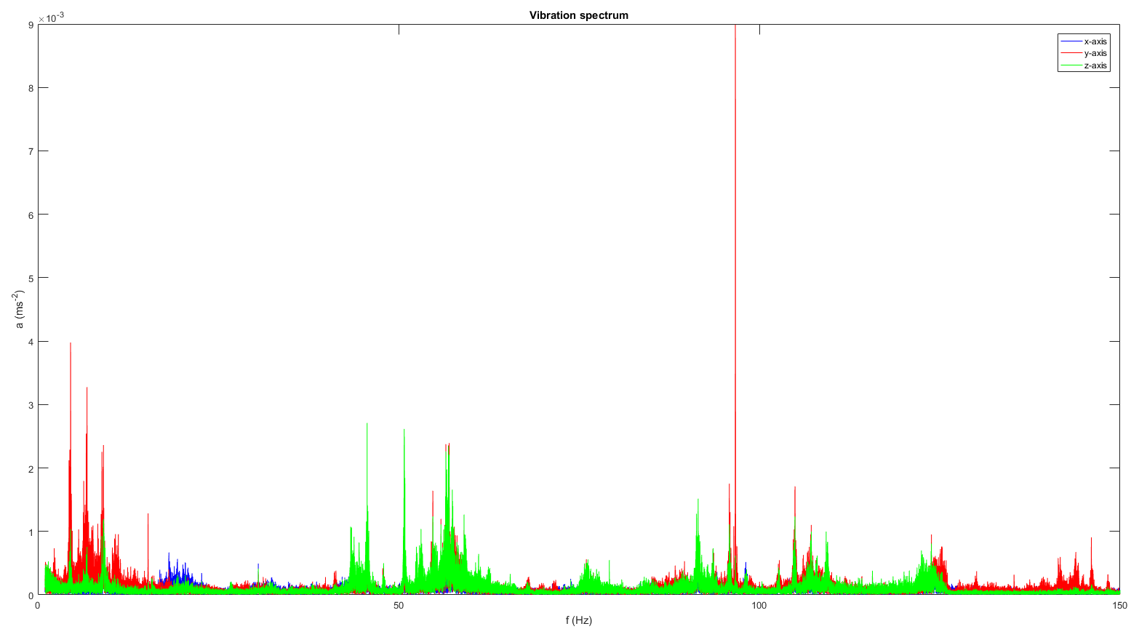
Working_Files/Figures/vib2.png
