Kempf/GuidestarLaser/Working_Files/Figures/vib3.png

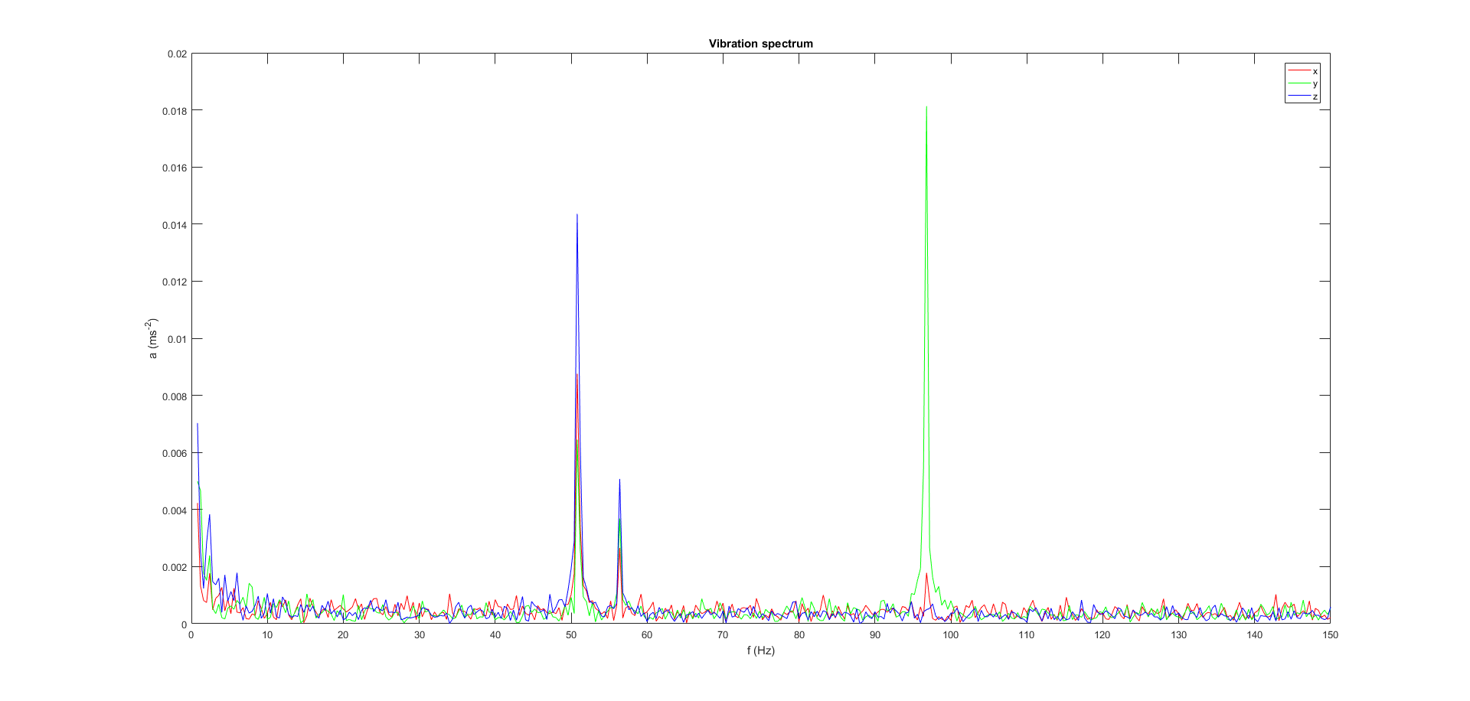
Working_Files/Figures/vib3.png
