Kempf/GuidestarLaser/Working_Files/Poster/draft_design.png

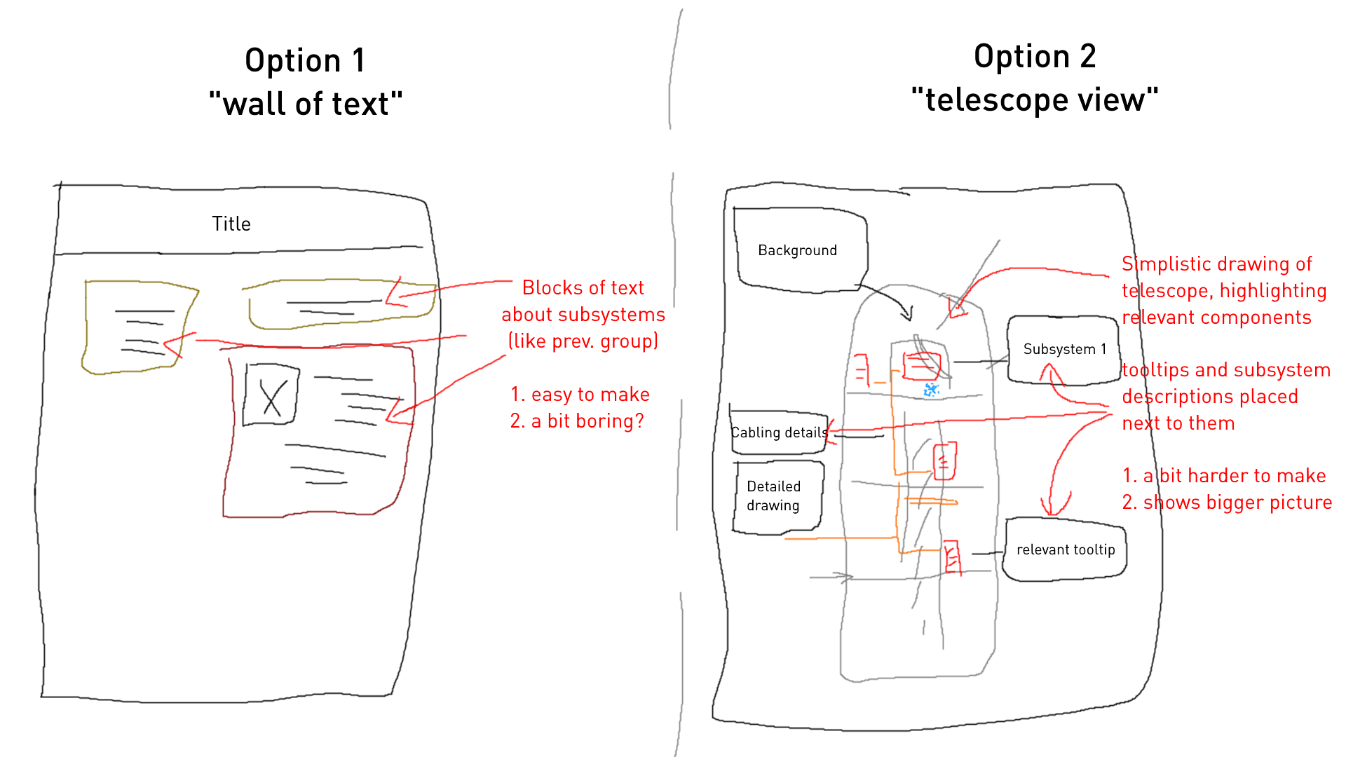
Working_Files/Poster/draft_design.png
