Kempf/GuidestarLaser/Working_Files/Poster/poster.png

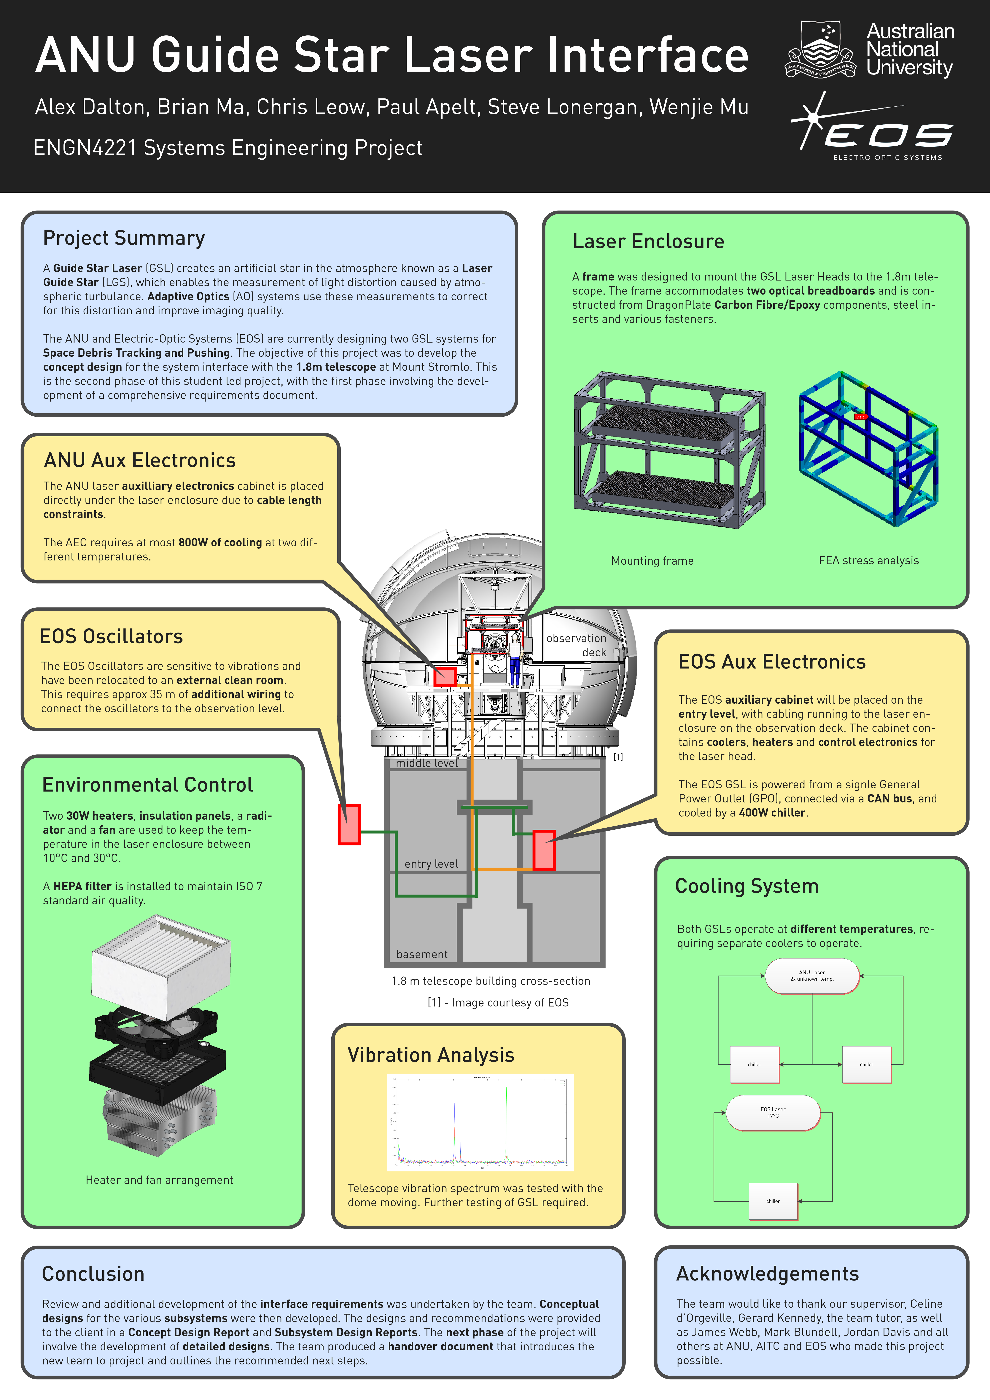
Working_Files/Poster/poster.png
