Kempf/GuidestarLaser/Project_Deliverables/CAD/2inch_90degCorner170927.sldprt

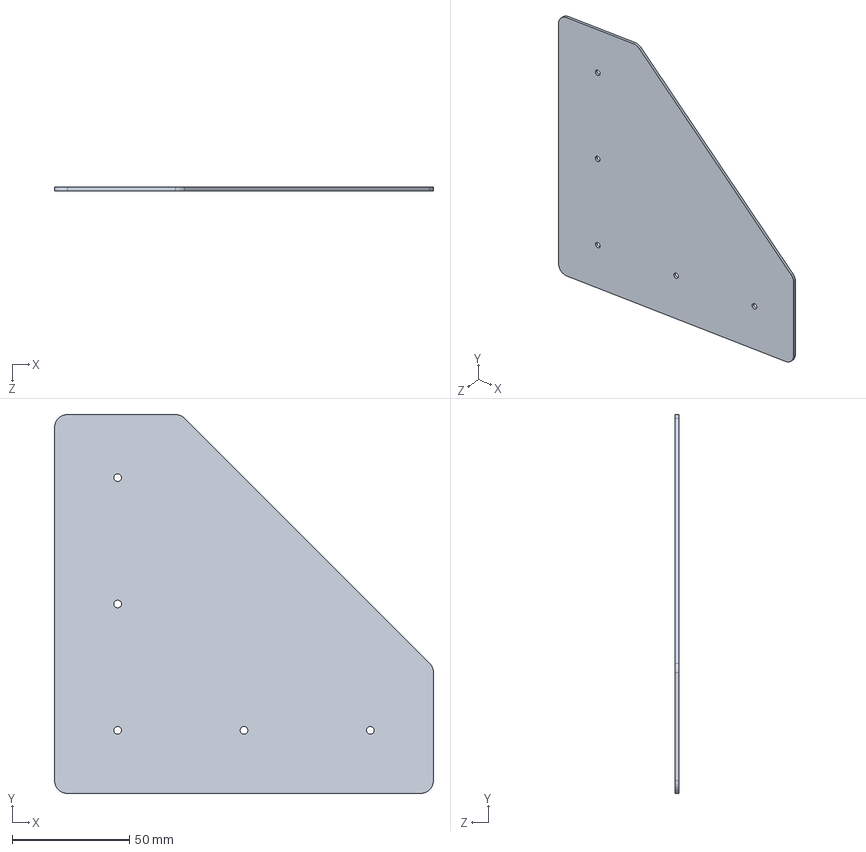
[picture p176: CAD file, 2017-10-06]
Project_Deliverables/CAD/2inch_90degCorner170927.sldprt
161.9 x 161.9 x 1.59 mm
