Kempf/GuidestarLaser/Project_Deliverables/CAD/ball_adjuster_mount.SLDPRT

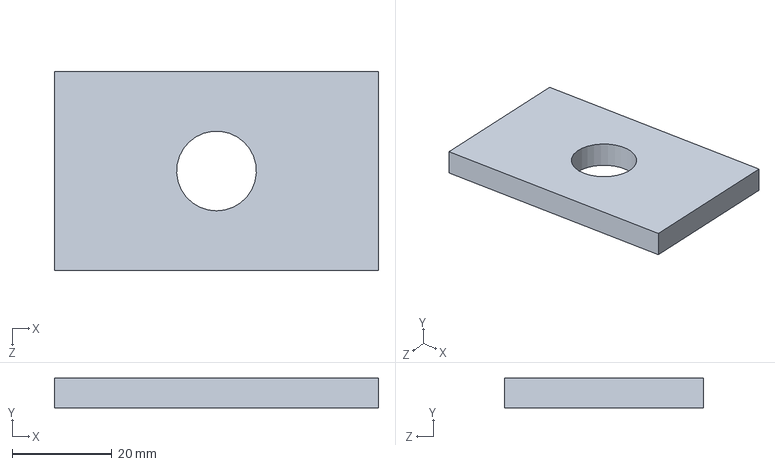
[picture p177: CAD file, 2017-10-06]
Project_Deliverables/CAD/ball_adjuster_mount.SLDPRT
65.0 x 6.00 x 40.0 mm
