Kempf/GuidestarLaser/Project_Deliverables/CAD/Part40- ANU 2.sldprt

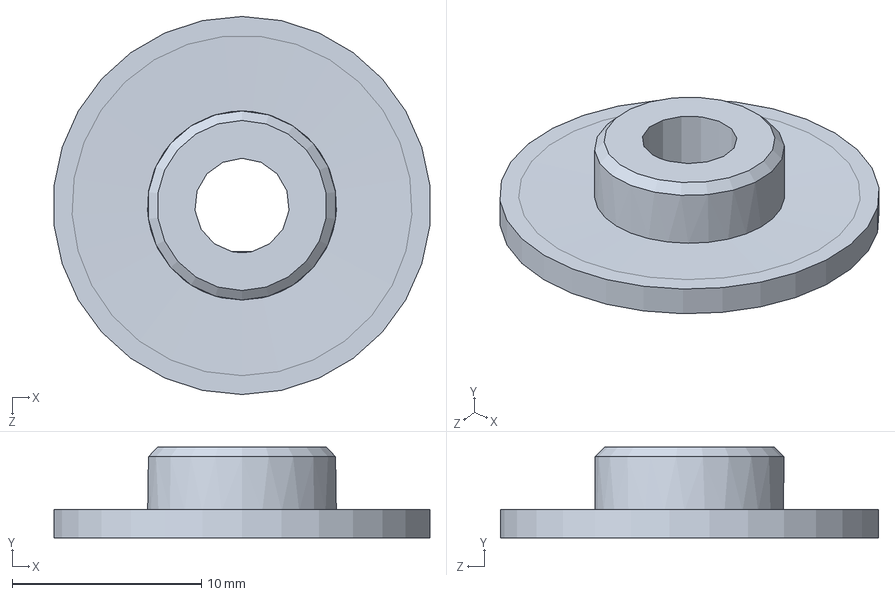
[picture p178: CAD file, 2017-10-06]
Project_Deliverables/CAD/Part40- ANU 2.sldprt
19.9 x 4.80 x 20.0 mm
