Kempf/GuidestarLaser/Project_Deliverables/CAD/Part37- ANU 2.sldprt

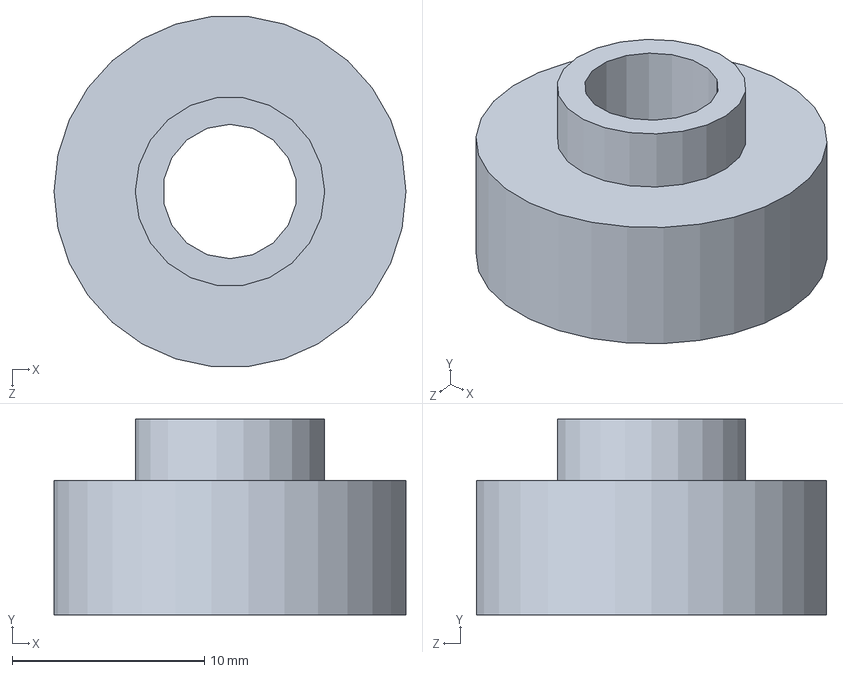
[picture p179: CAD file, 2017-10-06]
Project_Deliverables/CAD/Part37- ANU 2.sldprt
18.3 x 10.2 x 18.2 mm
