Kempf/GuidestarLaser/Project_Deliverables/CAD/2inch_cross170927.SLDPRT

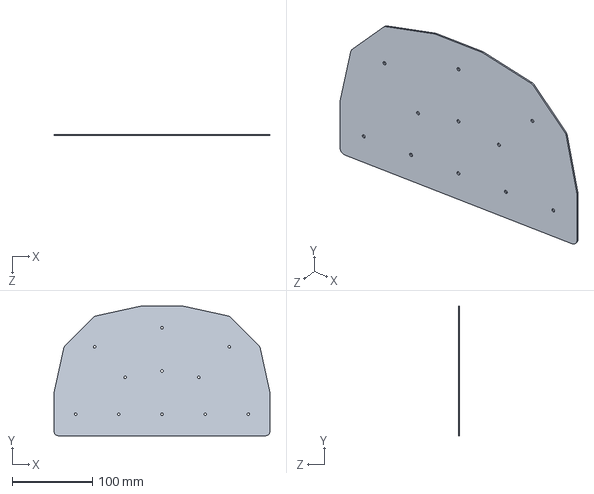
[picture p180: CAD file, 2017-10-06]
Project_Deliverables/CAD/2inch_cross170927.SLDPRT
269.9 x 161.9 x 1.59 mm
