Kempf/GuidestarLaser/Project_Deliverables/CAD/custom_T_gusset.SLDPRT

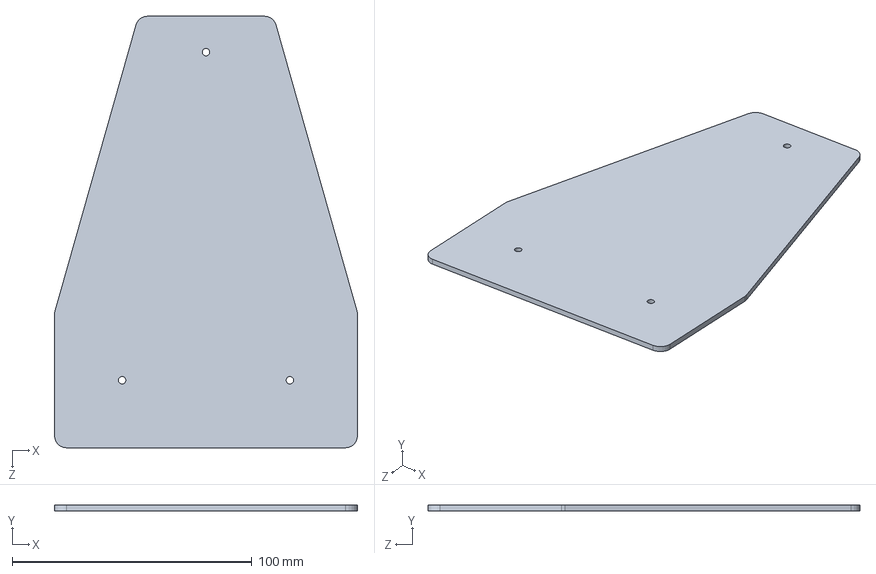
[picture p181: CAD file, 2017-10-06]
Project_Deliverables/CAD/custom_T_gusset.SLDPRT
126.4 x 2.36 x 180.0 mm
