Kempf/GuidestarLaser/Project_Deliverables/CAD/VB-75-SM-MODIFIED- ANU 2.SLDPRT

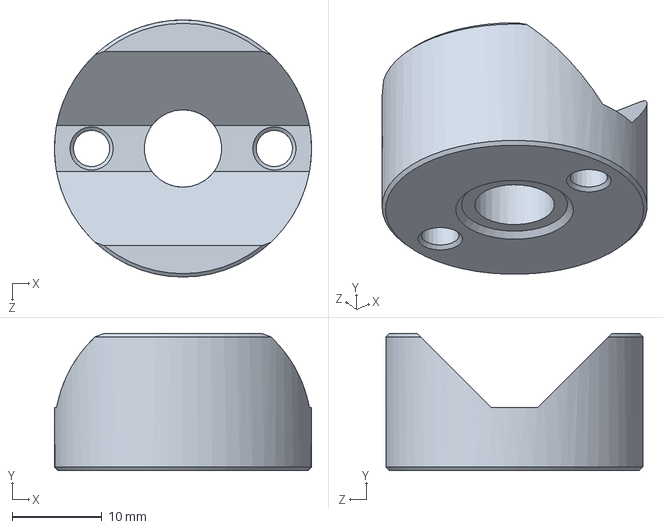
[picture p182: CAD file, 2017-10-06]
Project_Deliverables/CAD/VB-75-SM-MODIFIED- ANU 2.SLDPRT
28.6 x 15.2 x 28.6 mm
