Kempf/GuidestarLaser/Project_Deliverables/CAD/2inch_90degCorner_45170927.SLDPRT

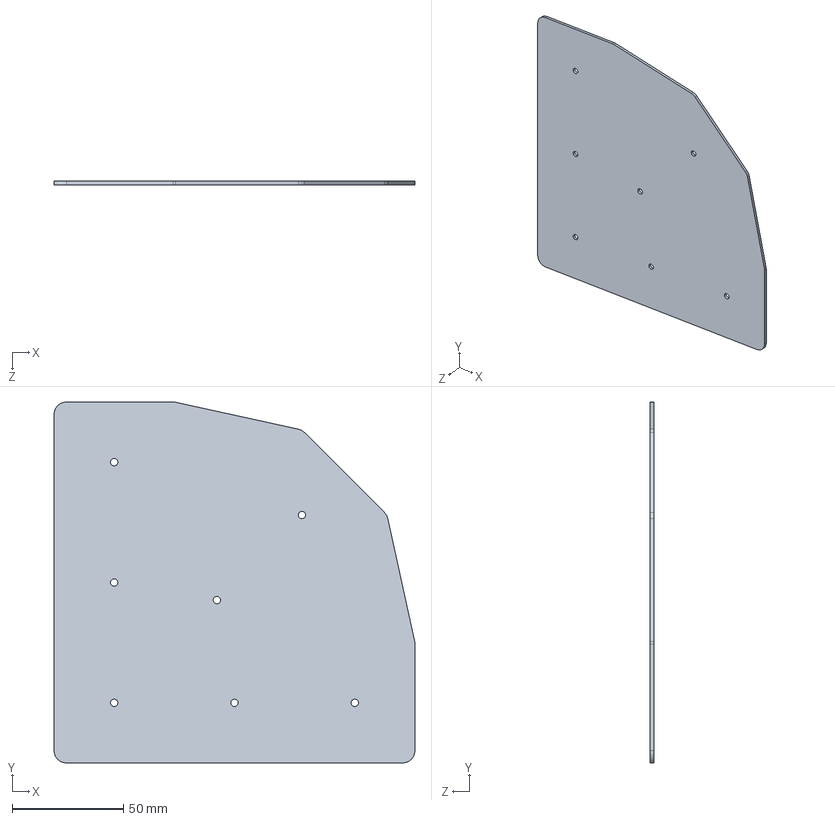
[picture p183: CAD file, 2017-10-06]
Project_Deliverables/CAD/2inch_90degCorner_45170927.SLDPRT
161.9 x 161.9 x 1.59 mm
