Kempf/GuidestarLaser/Project_Deliverables/CAD/Part41- ANU 2.sldprt

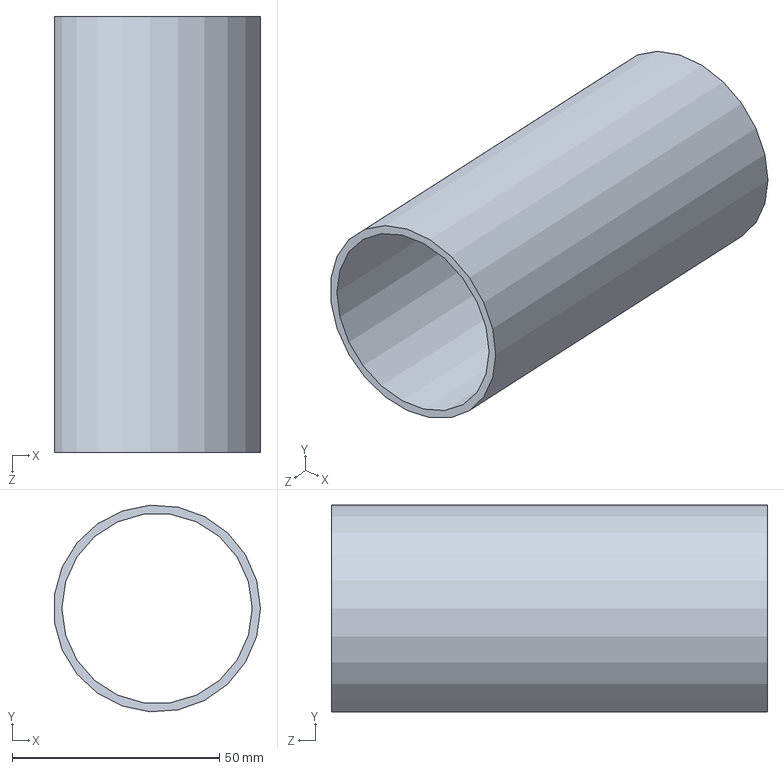
[picture p184: CAD file, 2017-10-06]
Project_Deliverables/CAD/Part41- ANU 2.sldprt
49.8 x 49.9 x 105.3 mm
