Kempf/GuidestarLaser/Project_Deliverables/CAD/Part35- ANU 2.sldprt

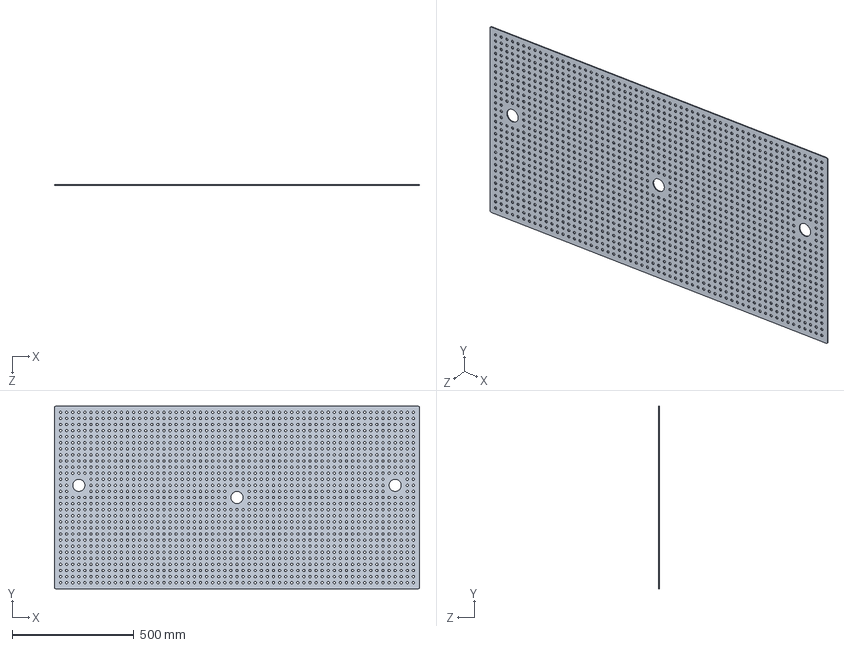
[picture p185: CAD file, 2017-10-06]
Project_Deliverables/CAD/Part35- ANU 2.sldprt
1500.0 x 750.0 x 3.30 mm
