Kempf/GuidestarLaser/Project_Deliverables/CAD/2_tier_inserts170927.SLDPRT

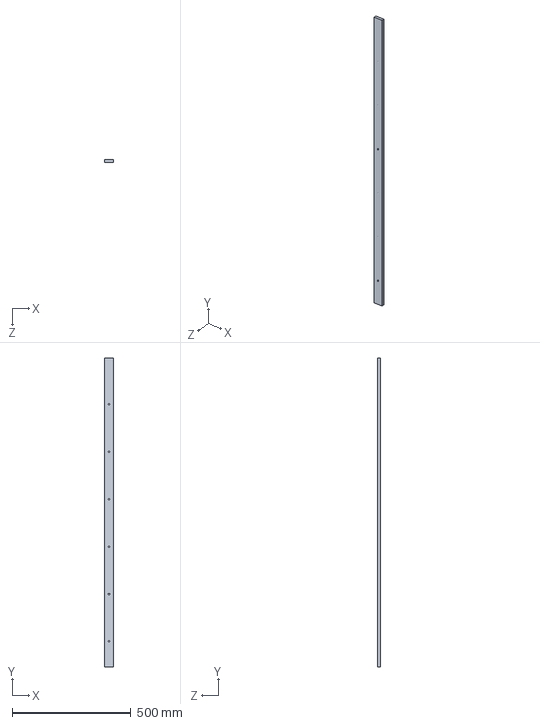
[picture p186: CAD file, 2017-10-06]
Project_Deliverables/CAD/2_tier_inserts170927.SLDPRT
40.0 x 1303.4 x 12.0 mm
