Kempf/GuidestarLaser/Project_Deliverables/CAD/DragonPlate_2_tier_frame.SLDPRT

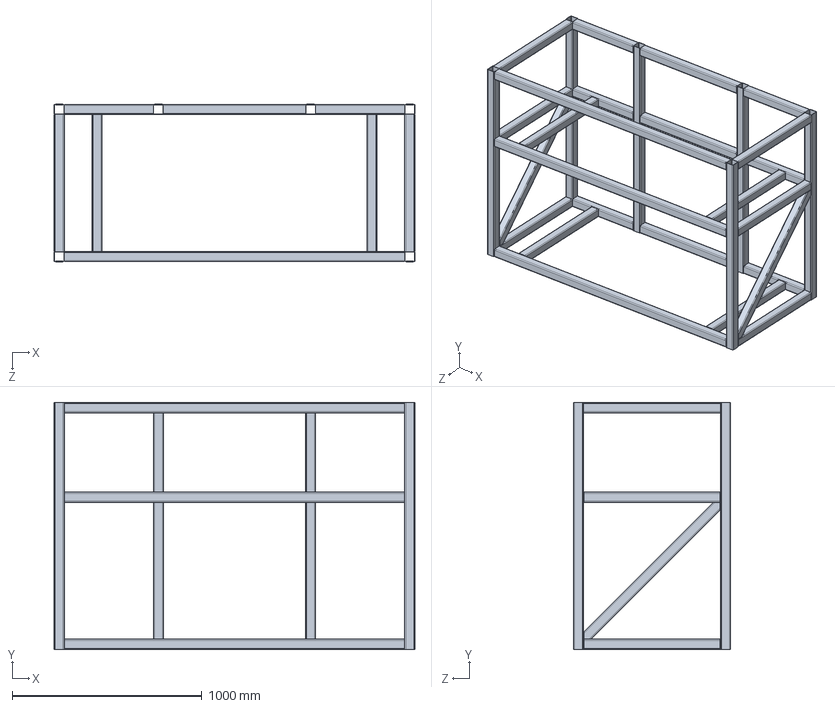
[picture p187: CAD file, 2017-10-06]
Project_Deliverables/CAD/DragonPlate_2_tier_frame.SLDPRT
1904.4 x 1303.4 x 830.5 mm
