Kempf/GuidestarLaser/Project_Deliverables/CAD/Part39- ANU 2.sldprt

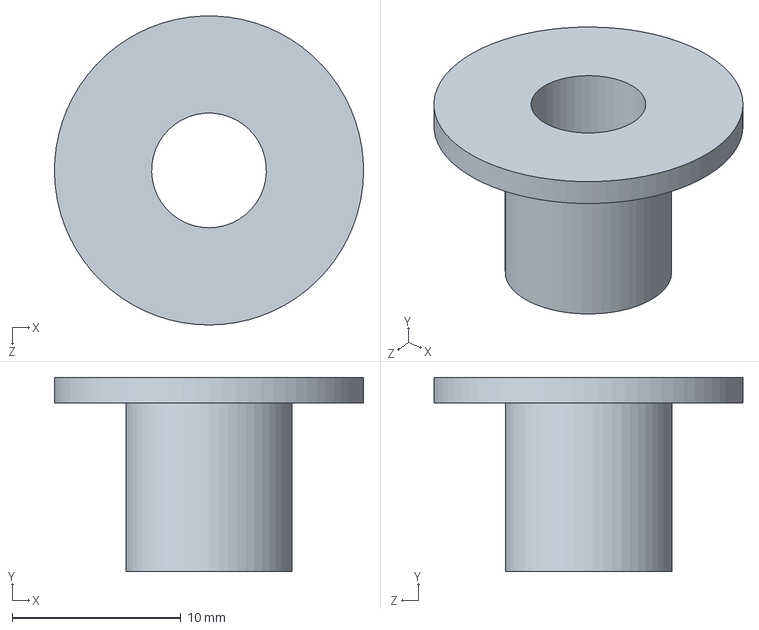
[picture p188: CAD file, 2017-10-06]
Project_Deliverables/CAD/Part39- ANU 2.sldprt
18.3 x 11.5 x 18.3 mm
