Kempf/GuidestarLaser/Project_Deliverables/CAD/2inch_plus170927.SLDPRT

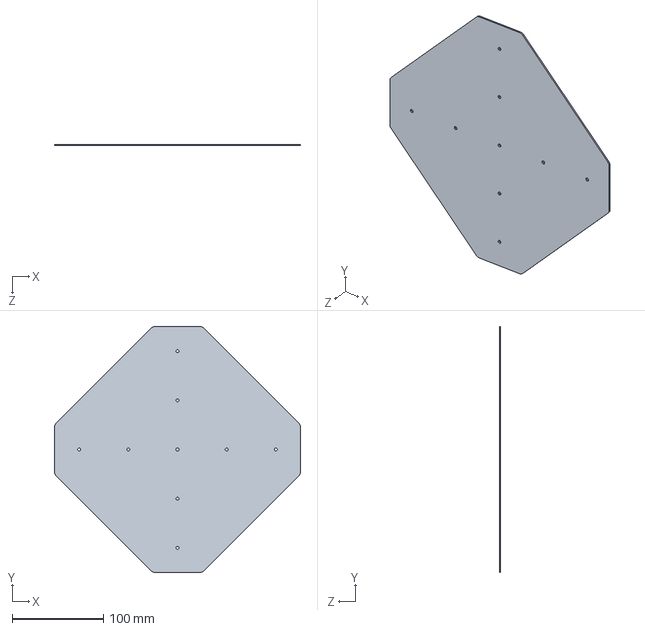
[picture p189: CAD file, 2017-10-06]
Project_Deliverables/CAD/2inch_plus170927.SLDPRT
269.9 x 269.9 x 1.59 mm
