Kempf/GuidestarLaser/Project_Deliverables/CAD/Part36- ANU 2.sldprt

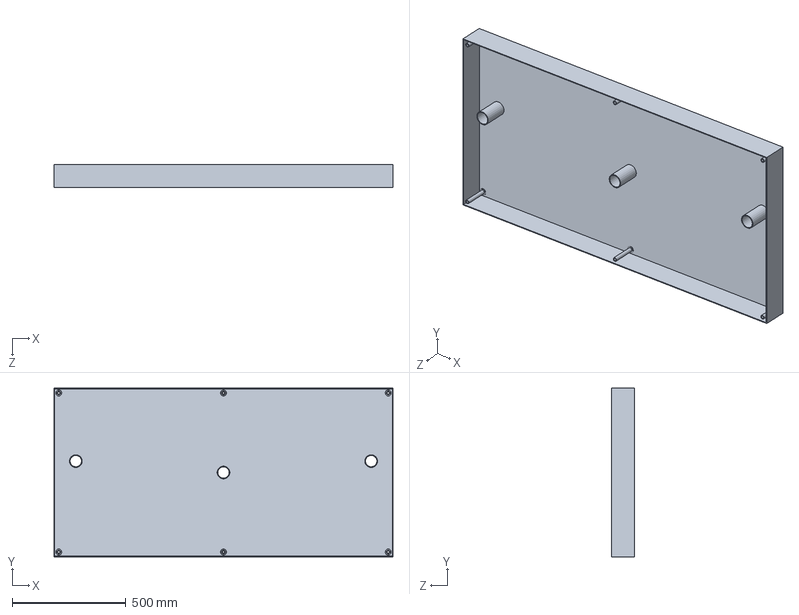
[picture p190: CAD file, 2017-09-05]
Project_Deliverables/CAD/Part36- ANU 2.sldprt
1492.0 x 742.0 x 102.0 mm
