Kempf/GuidestarLaser/ProjectRequirements/Project_Reviews/Project_Reviews.pdf

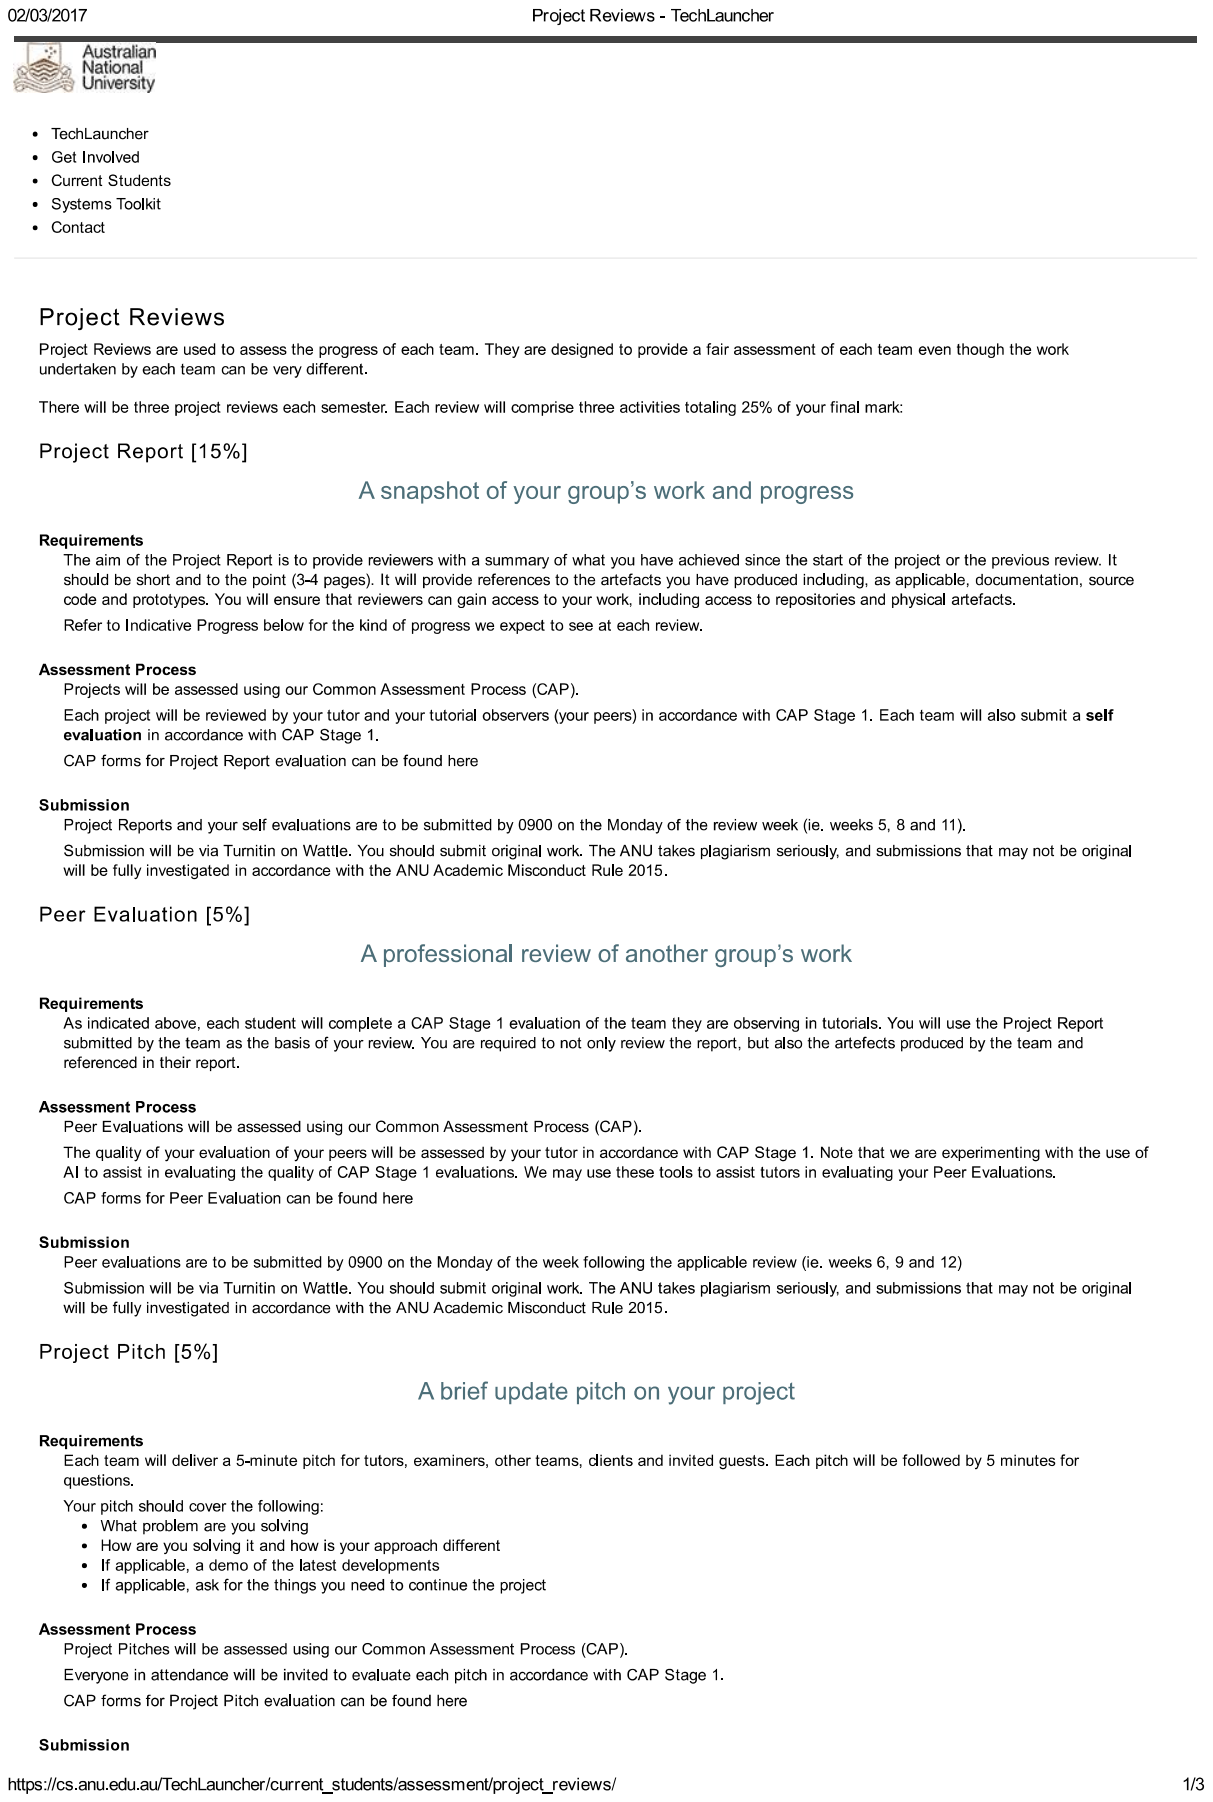
[picture p193: page 1]

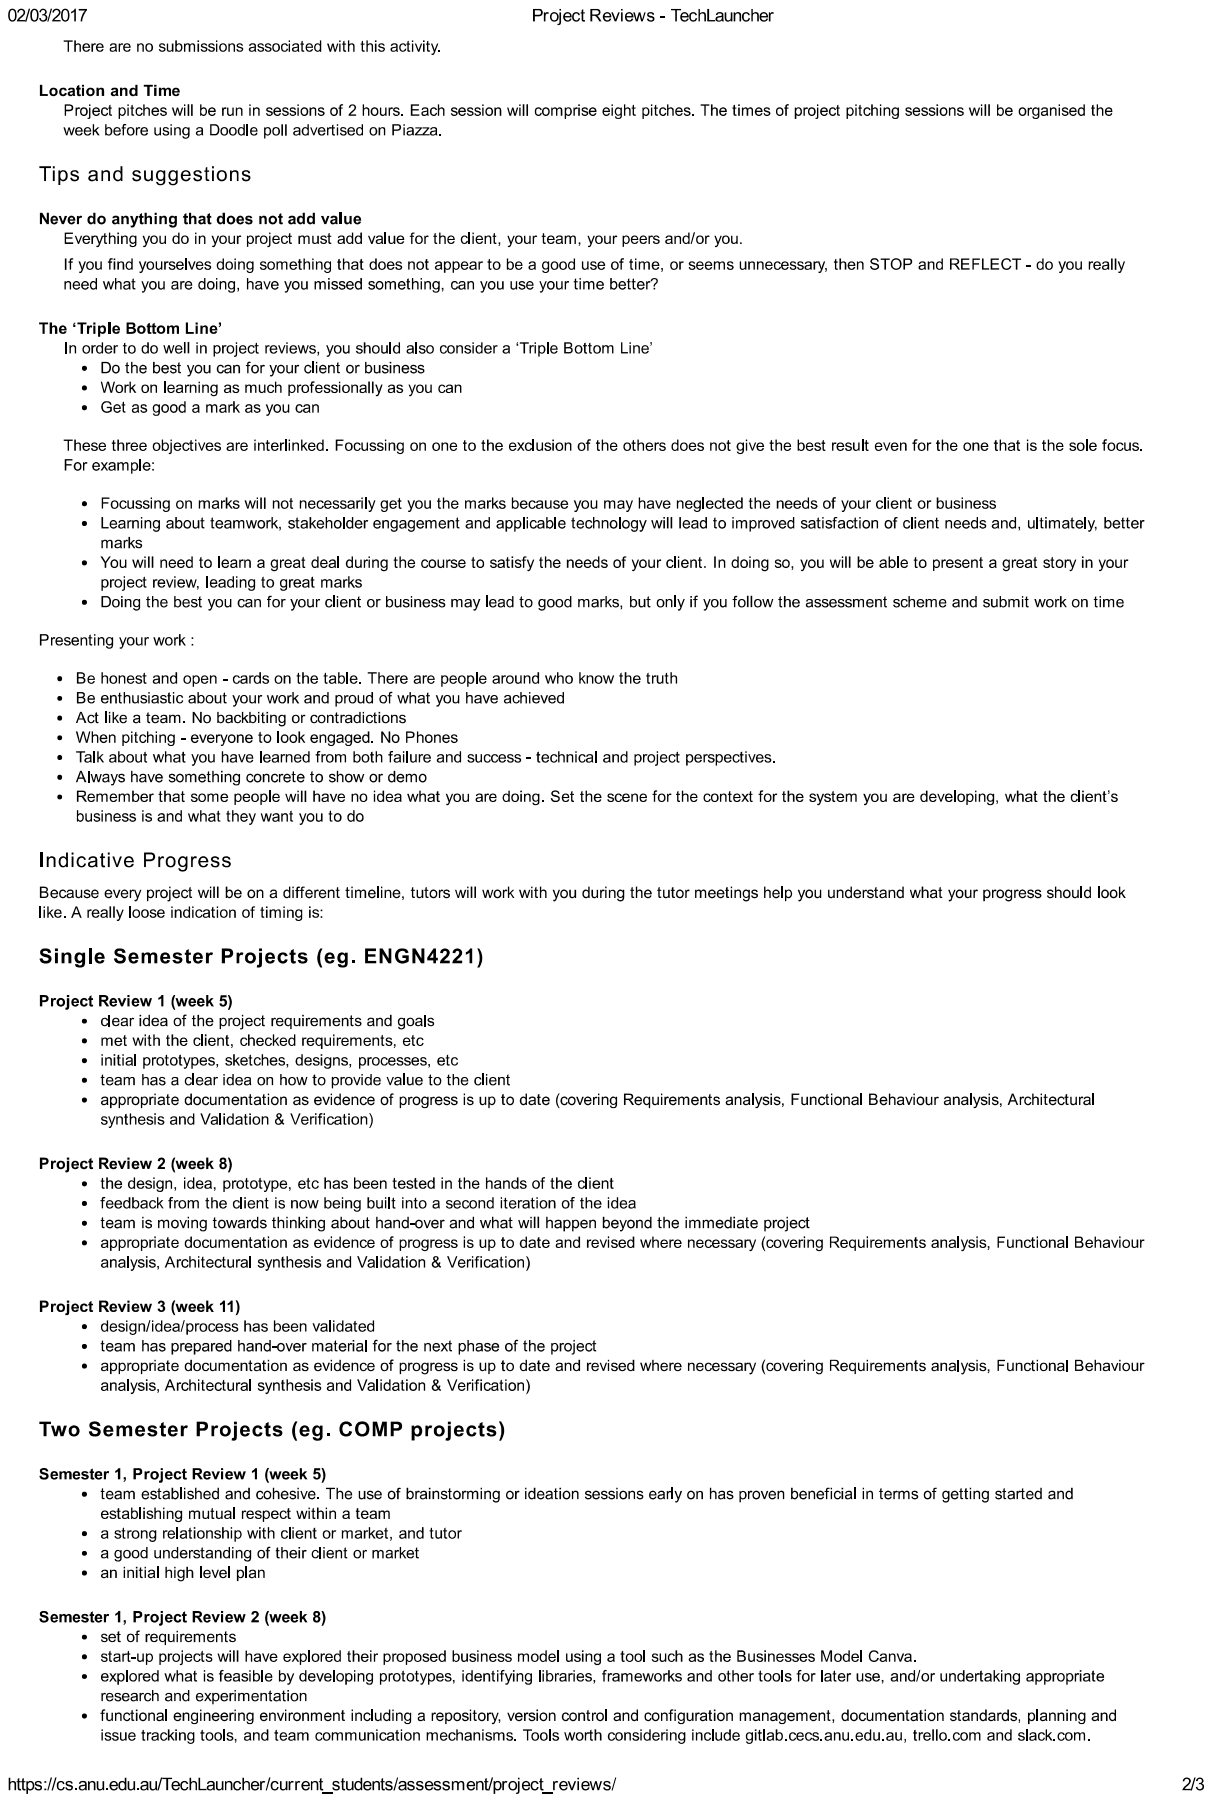
[picture p194: page 2]

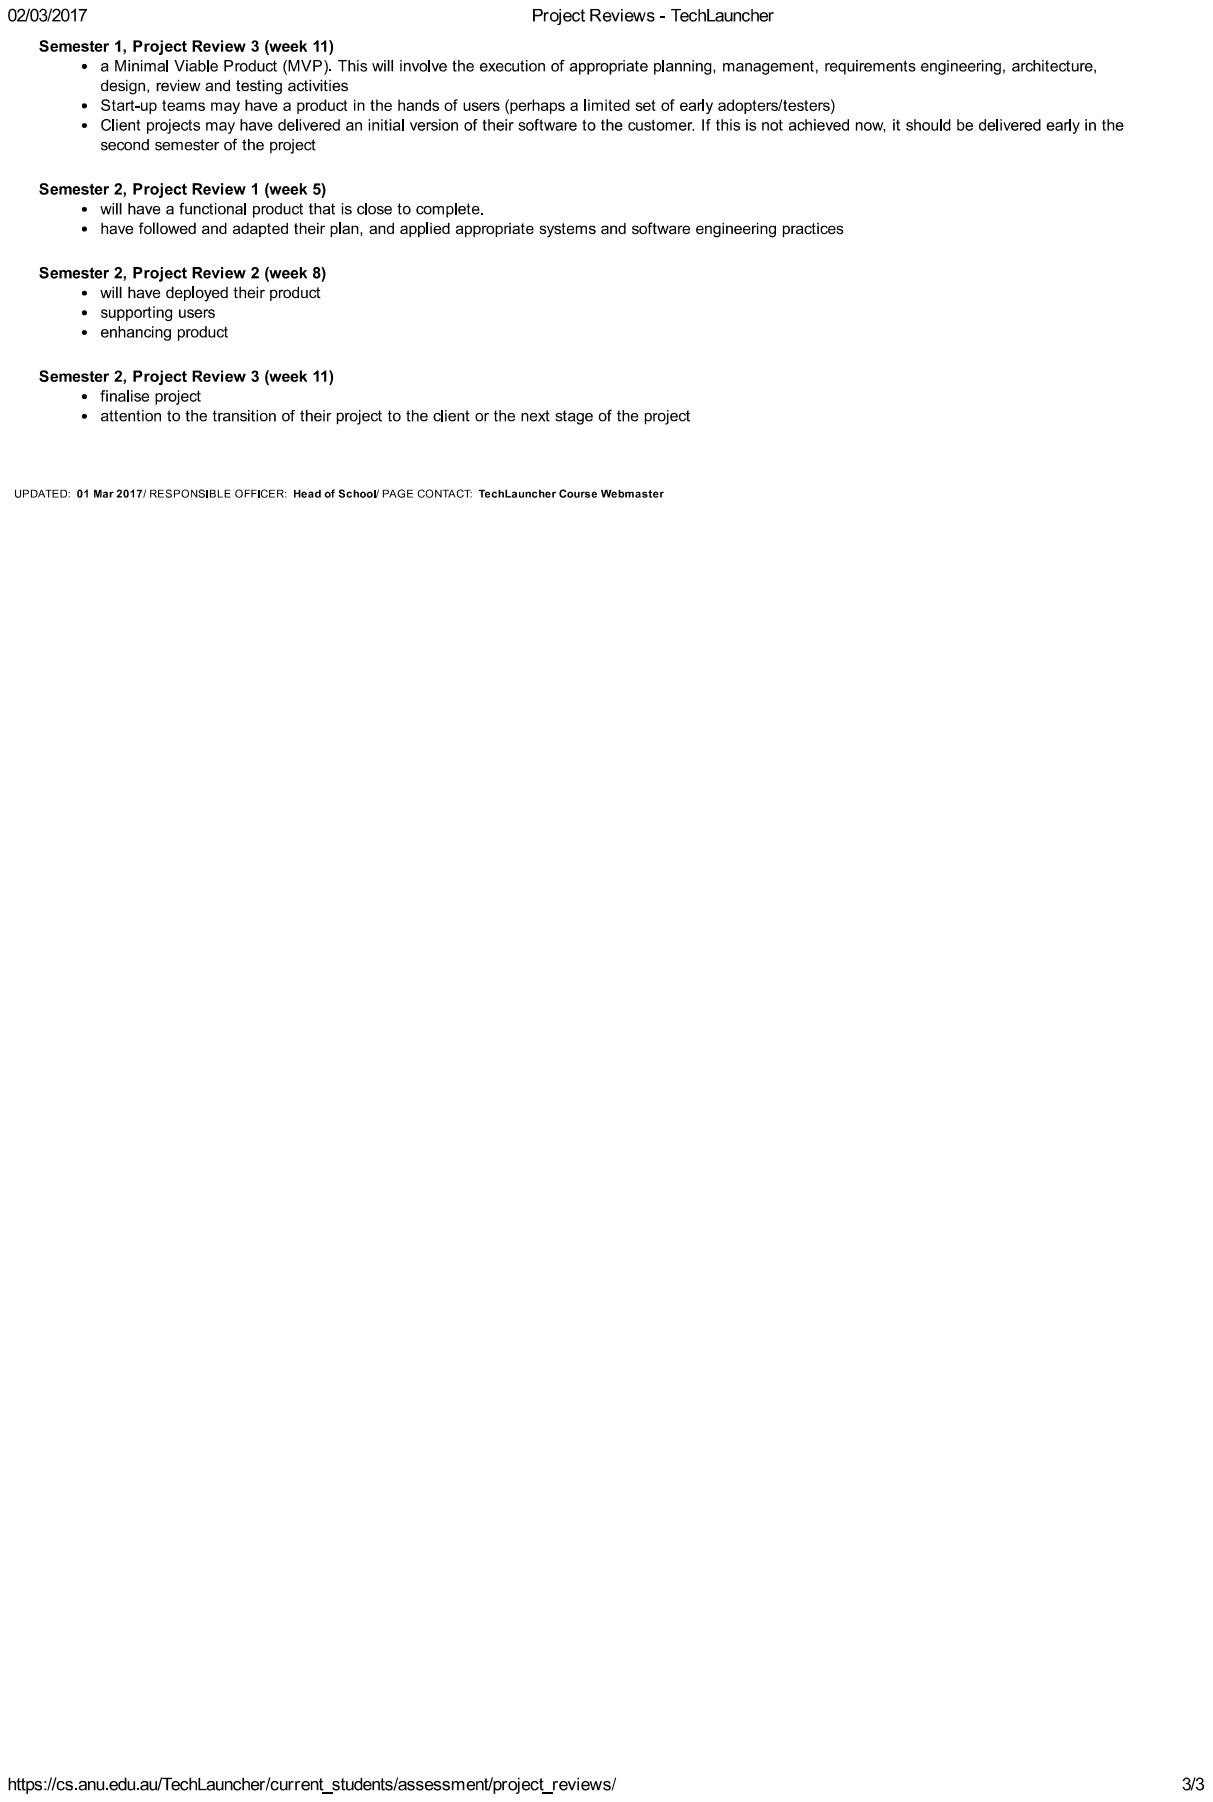
[picture p195: page 3]
