Kempf/GuidestarLaser/Working_Files/Liquid_Cooling/proposedcooling.pdf

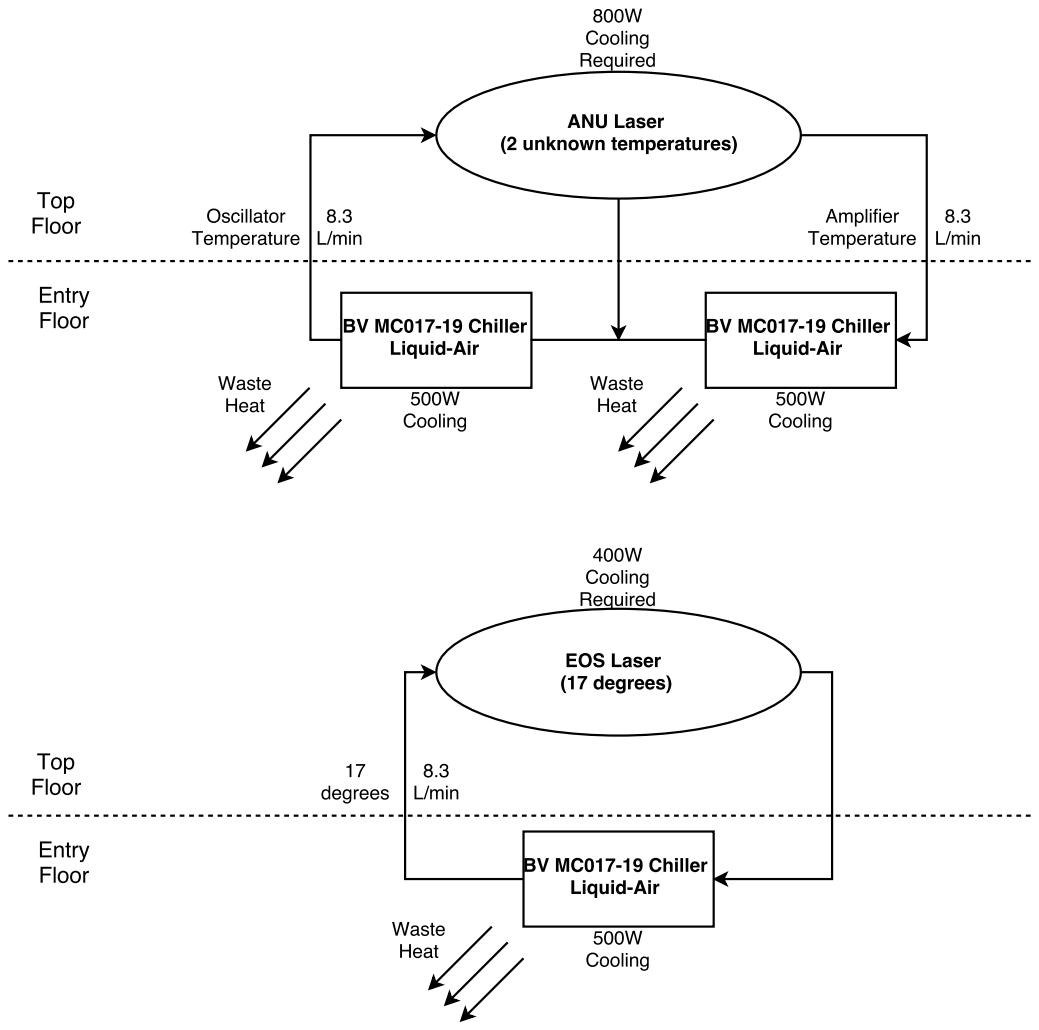
[picture p196: page 1]
